JordanAceto/josh_Ox_ribbon_synth/circuit_boards/ribbon_board/protoboard_buffer/README.md

# Protoboard Softpot Ribbon Buffer

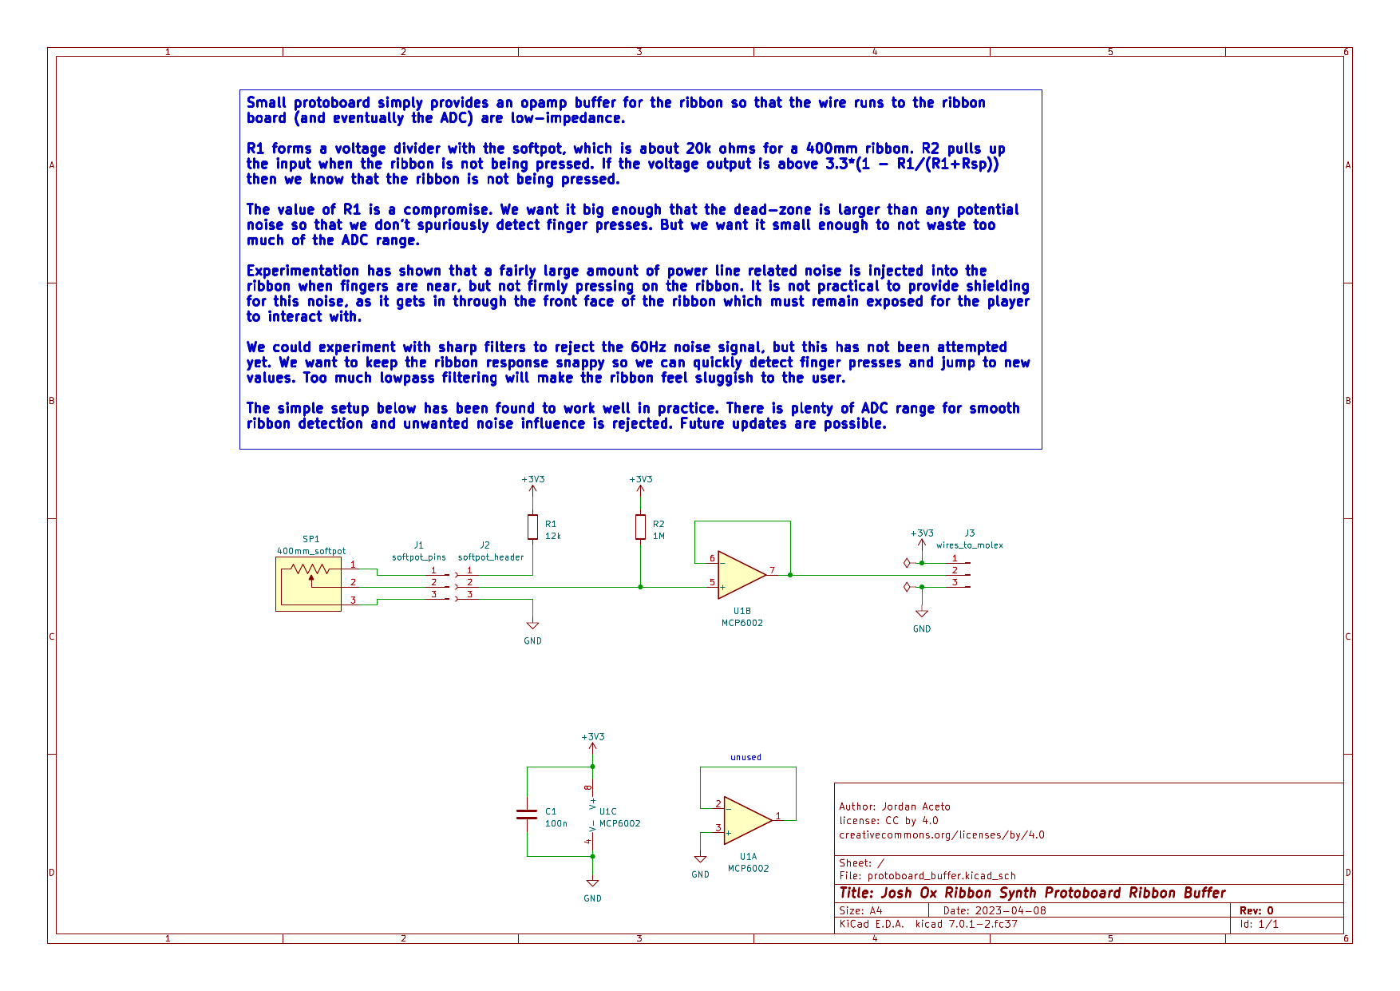
[picture p3: circuit_boards/ribbon_board/protoboard_buffer/images/schem.png]
schematic


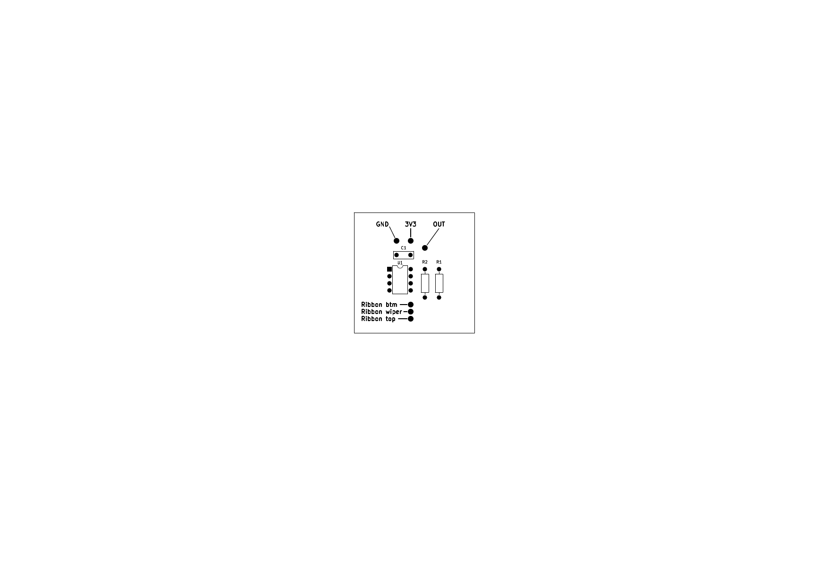
[picture p4: circuit_boards/ribbon_board/protoboard_buffer/images/layout.png]
layout
