JordanAceto/josh_Ox_ribbon_synth/circuit_boards/mains_transformer/mains_transformer.png

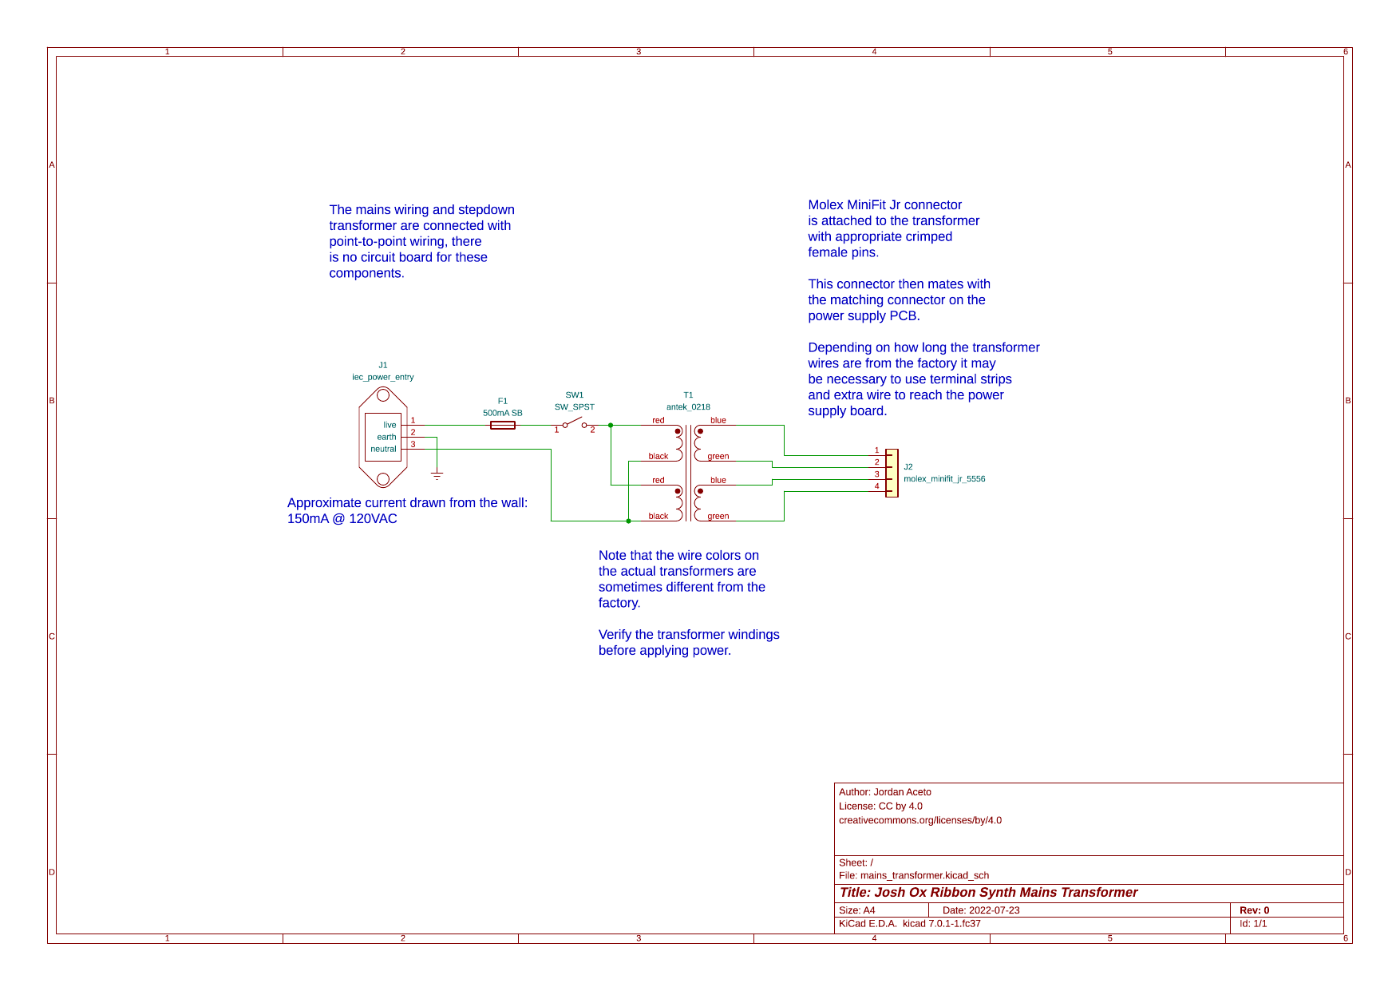
circuit_boards/mains_transformer/mains_transformer.png
