JordanAceto/josh_Ox_ribbon_synth/images/front_angle_2.JPG

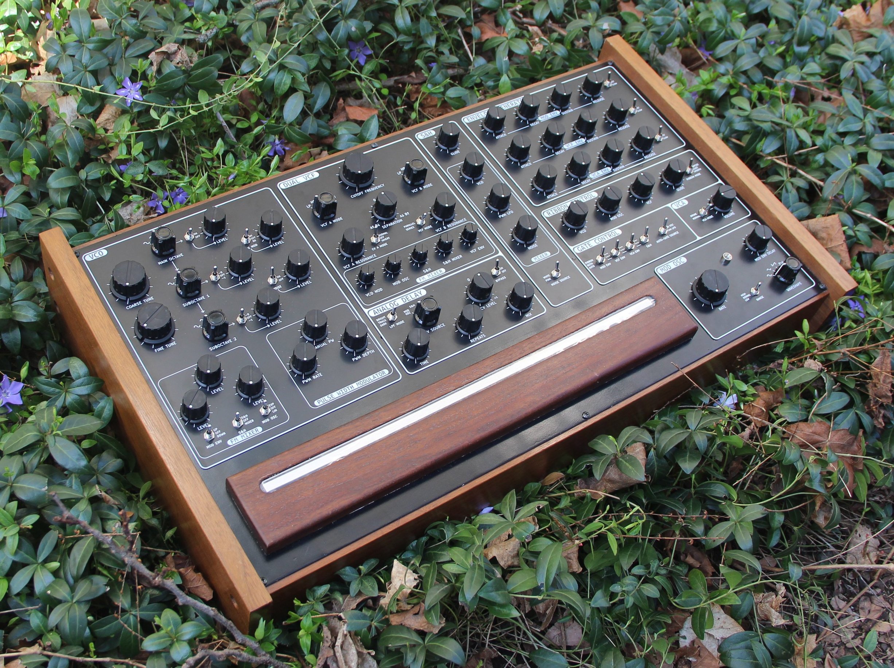
images/front_angle_2.JPG
