JordanAceto/josh_Ox_ribbon_synth/images/front_straight.JPG

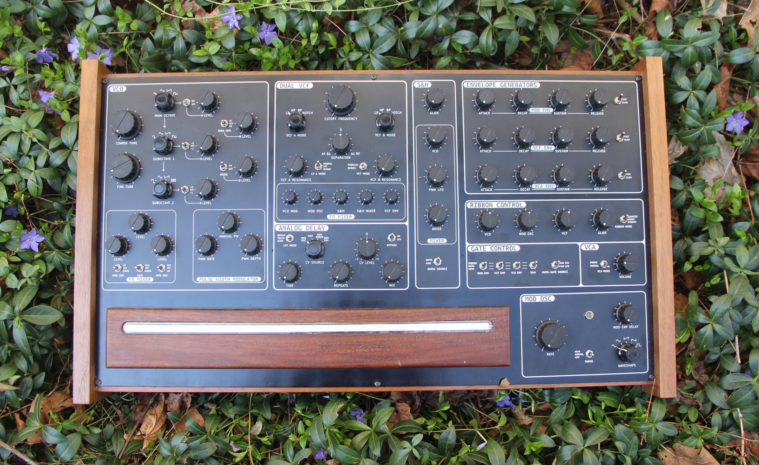
images/front_straight.JPG
