JordanAceto/josh_Ox_ribbon_synth/images/guts_angle.JPG

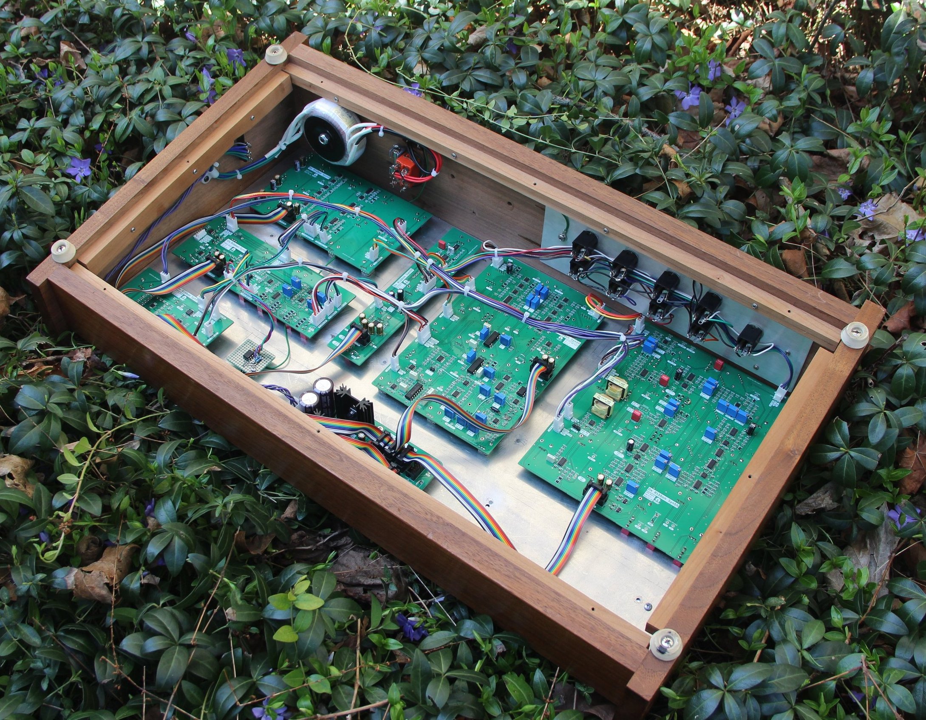
images/guts_angle.JPG
