JordanAceto/josh_Ox_ribbon_synth/images/guts_straight.JPG

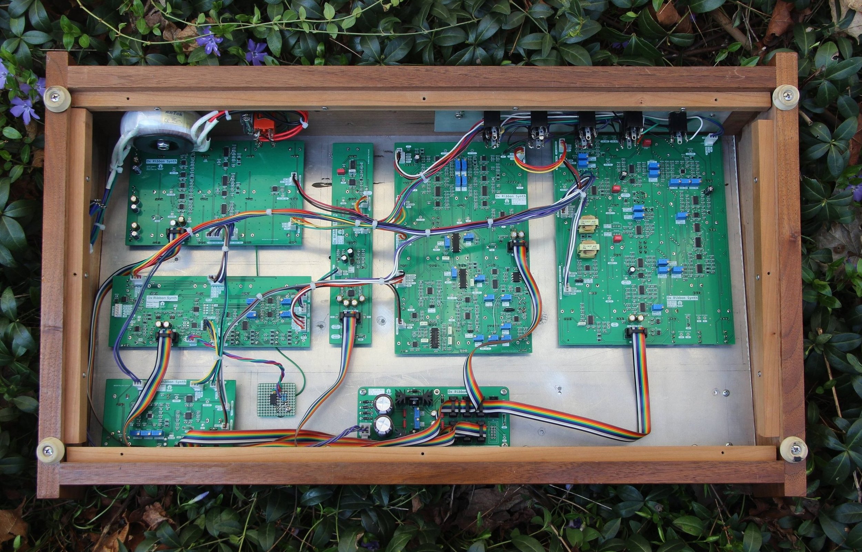
images/guts_straight.JPG
