JordanAceto/josh_Ox_ribbon_synth/images/ox_panel.png

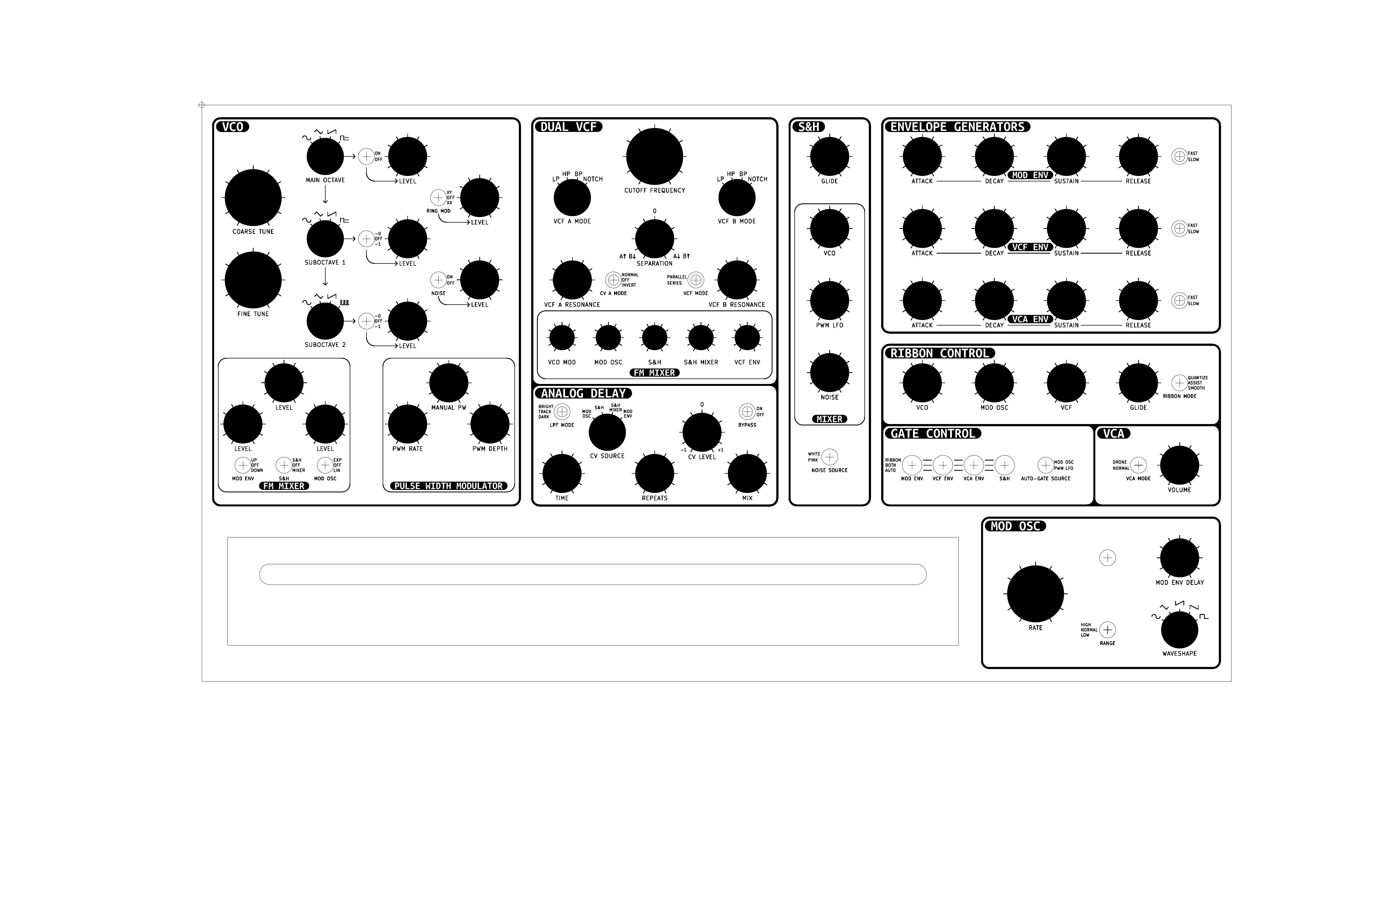
images/ox_panel.png
