JordanAceto/josh_Ox_ribbon_synth/panel/ribbon_pcb_panel/docs/2D/ribbon_pcb_panel_B.Cu.pdf

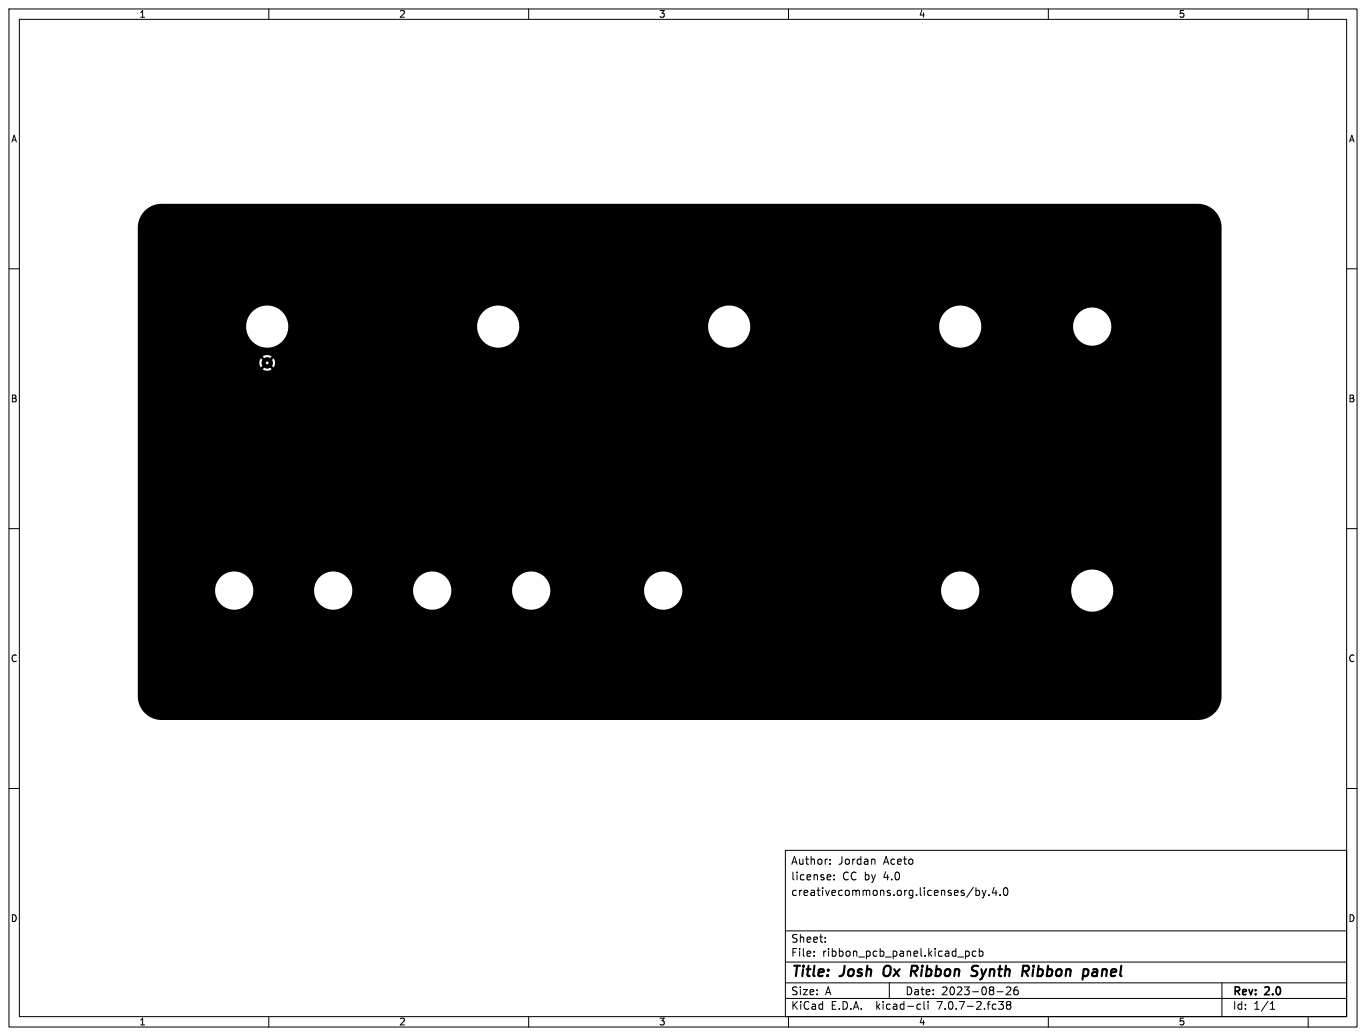
[picture p59: page 1]

license: CC by 4.0 Author: Jordan Aceto

Id: 1/1 Title: Josh Ox Ribbon Synth Ribbon panel File: ribbon_pcb_panel.kicad_pcb Sheet: creativecommons.org.licenses/by.4.0

E.D.A. | kicad-cli | 7.0.7-2.fc38 Size: A | Rev: 2.0 | D Date: 2023-08-26 KiCad
