JordanAceto/josh_Ox_ribbon_synth/circuit_boards/ADSR_board/docs/2D/ADSR_board_B.Cu.pdf

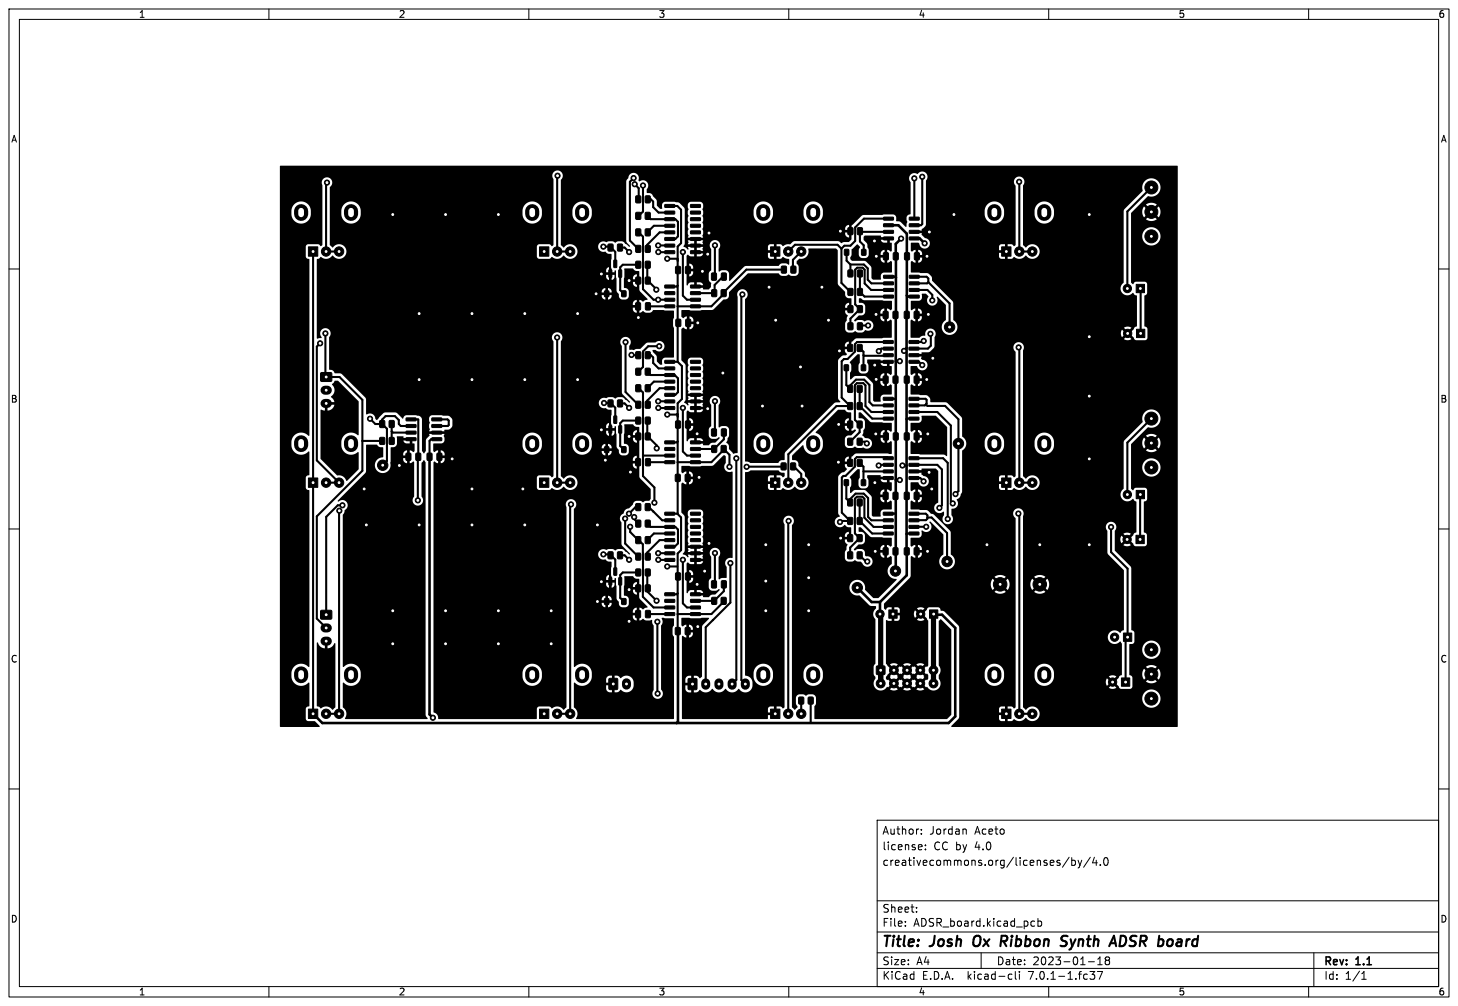
[picture p60: page 1]

File: ADSR_board.kicad_pcb Sheet: creativecommons.org/licenses/by/4.0

Id: 1/1 Title: Josh Ox Ribbon Synth ADSR board
