JordanAceto/josh_Ox_ribbon_synth/circuit_boards/main_VCO_board/docs/2D/main_VCO_board_B.Cu.pdf

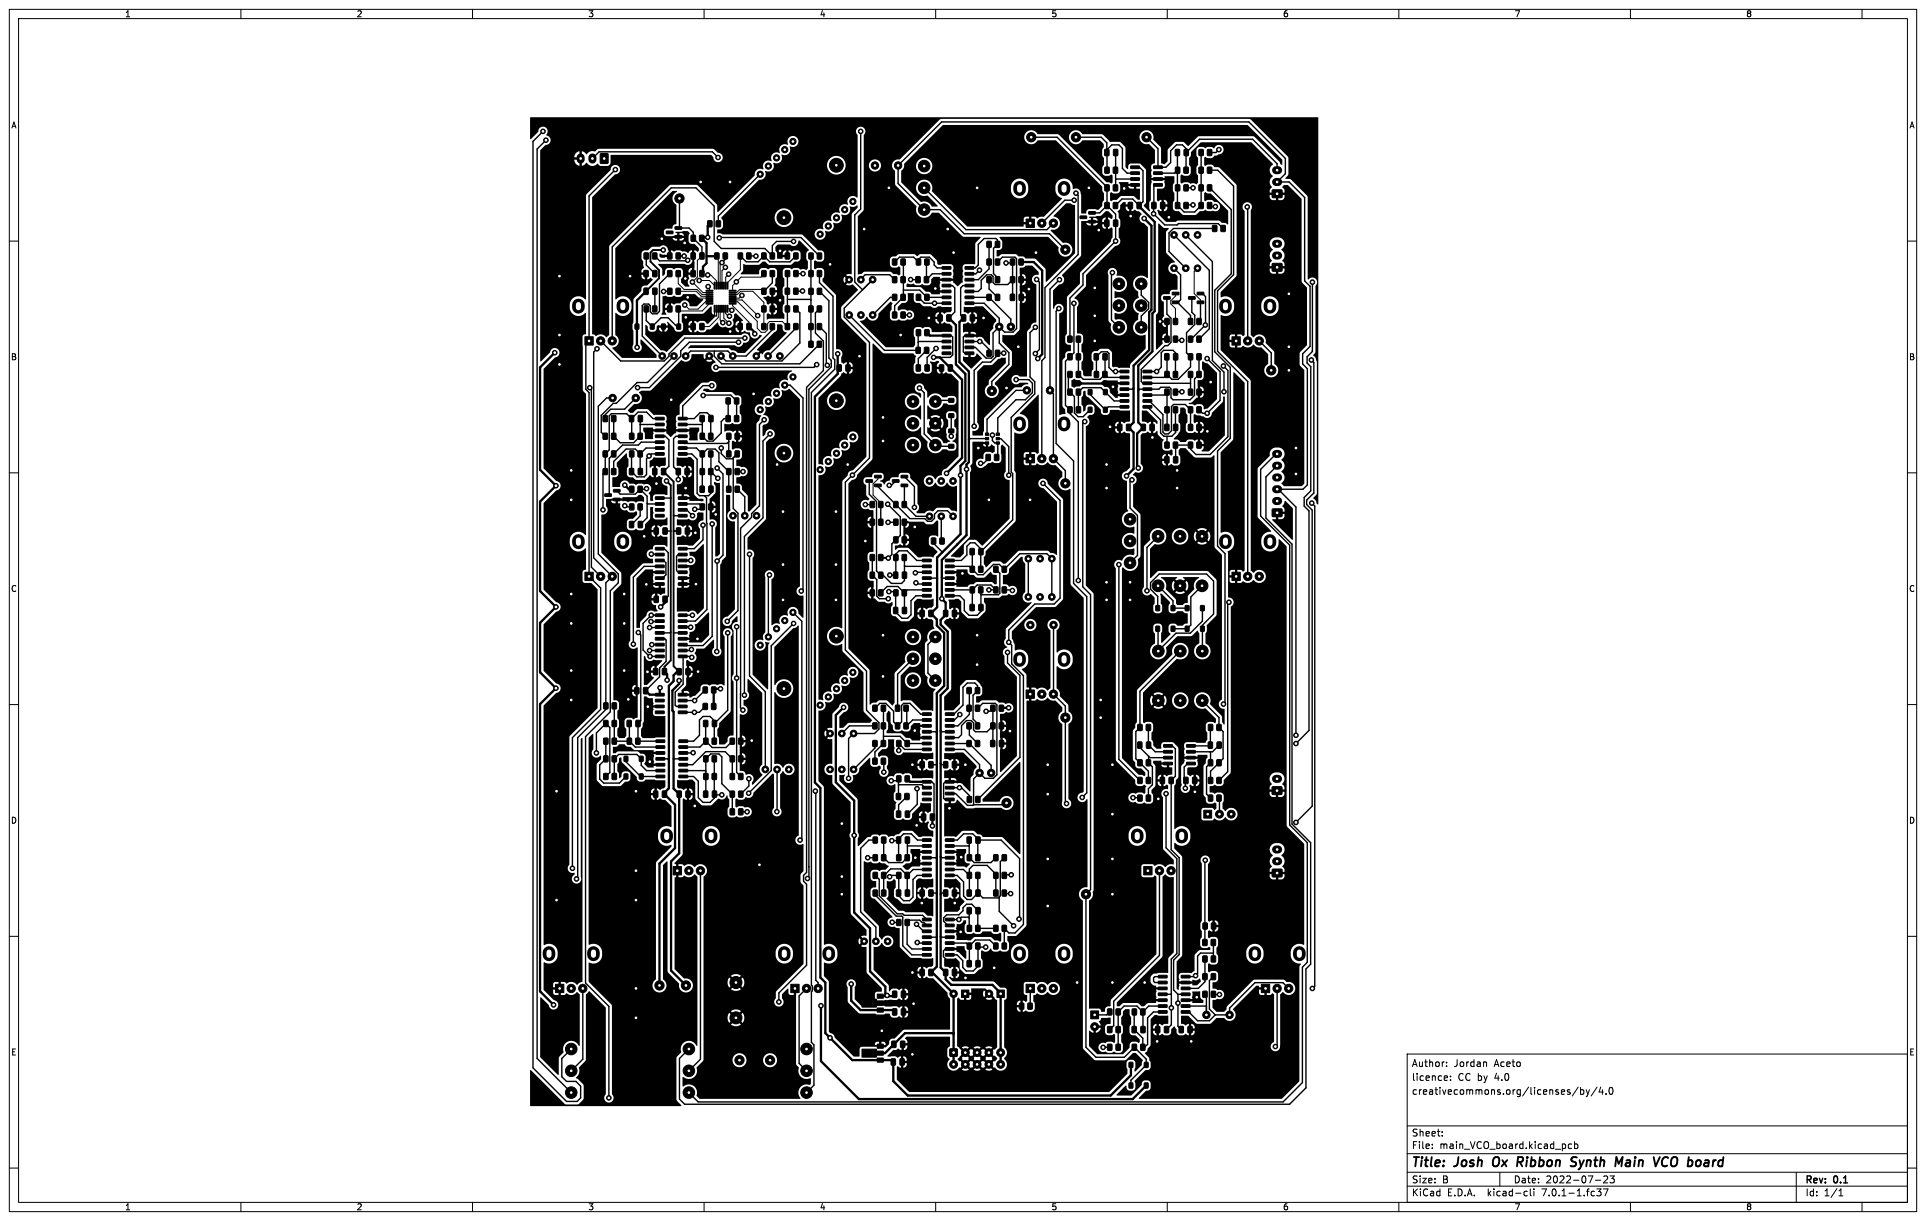
[picture p61: page 1]

File: main_VCO_board.kicad_pcb Sheet: creativecommons.org/licenses/by/4.0

Id: 1/1 Title: Josh Ox Ribbon Synth Main VCO board
