JordanAceto/josh_Ox_ribbon_synth/circuit_boards/power_supply_board/docs/2D/power_supply_F.Cu.pdf

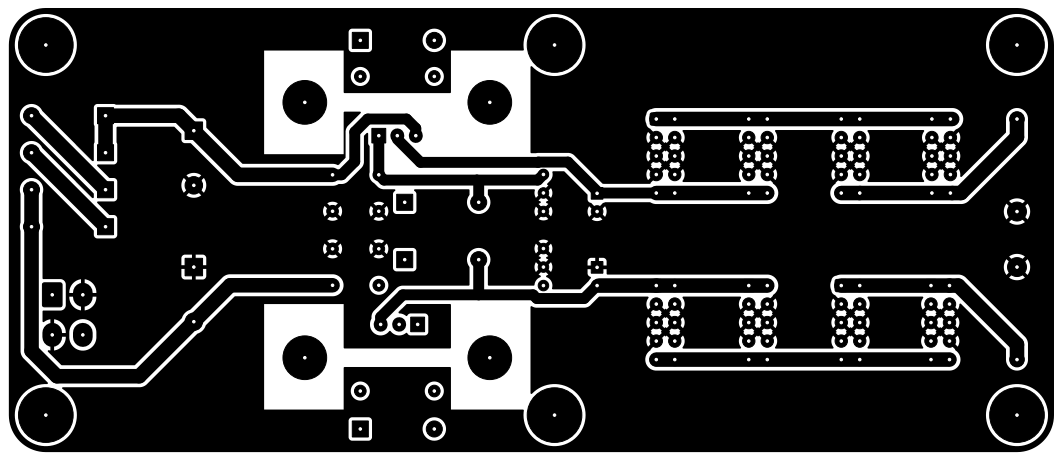
[picture p66: page 1]

Id: 1/1 Title: Josh Ox Ribbon Synth power supply board
