JordanAceto/josh_Ox_ribbon_synth/circuit_boards/power_supply_board/docs/2D/power_supply_F.Paste.pdf

Id: 1/1 Title: Josh Ox Ribbon Synth power supply board
