JordanAceto/josh_Ox_ribbon_synth/circuit_boards/VCF_VCA_BBD_board/docs/2D/VCF_VCA_BBD_board_B.Cu.pdf

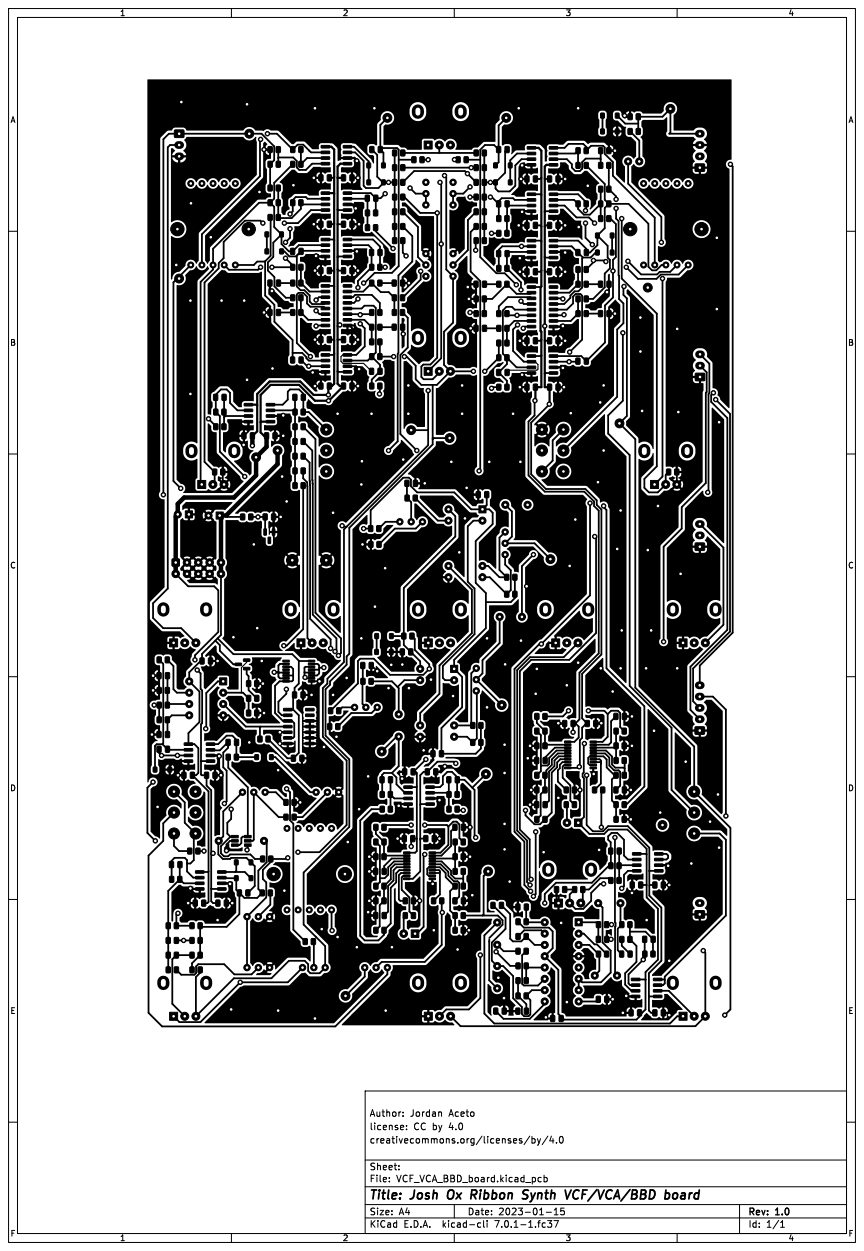
[picture p68: page 1]

File: VCF_VCA_BBD_board.kicad_pcb Sheet: creativecommons.org/licenses/by/4.0

Id: 1/1 Title: Josh Ox Ribbon Synth VCF/VCA/BBD board
