JordanAceto/josh_Ox_ribbon_synth/summer_2022_refurb/VCF_VCA_board/VCF_VCA_board.kicad_pcb

## KiCad design summer_2022_refurb/VCF_VCA_board/VCF_VCA_board.kicad_pcb (2022-06-16)

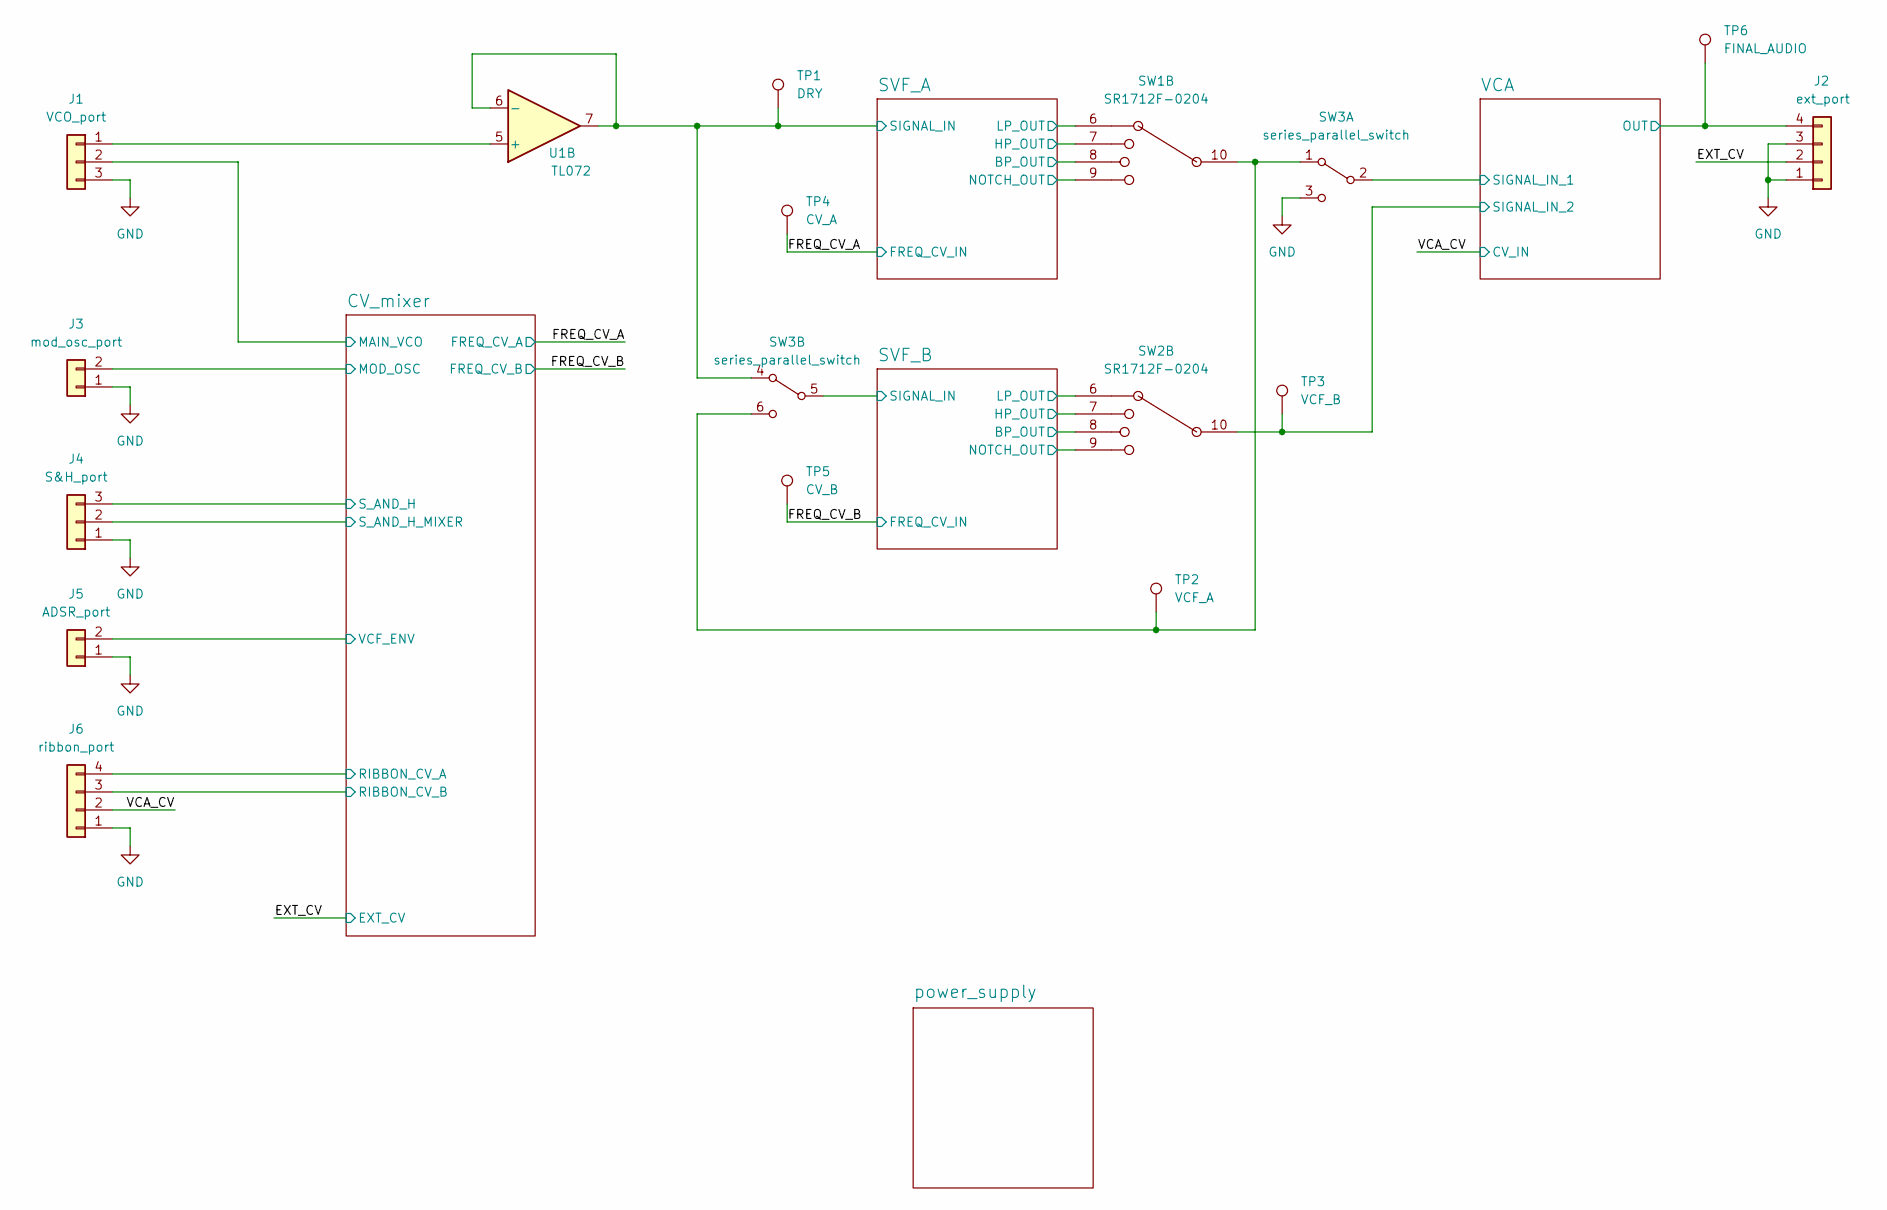
[picture p92: schematic VCF_VCA_board.kicad_sch, Josh Ox Ribbon Synth VCF/VCA board]

Parts:
J1: VCO_port; Molex_KK-254_AE-6410-03A_1x03_P2.54mm_Vertical
J2: ext_port; Molex_KK-254_AE-6410-04A_1x04_P2.54mm_Vertical
J3: mod_osc_port; Molex_KK-254_AE-6410-02A_1x02_P2.54mm_Vertical
J4: S&H_port; Molex_KK-254_AE-6410-03A_1x03_P2.54mm_Vertical
J5: ADSR_port; Molex_KK-254_AE-6410-02A_1x02_P2.54mm_Vertical
J6: ribbon_port; Molex_KK-254_AE-6410-04A_1x04_P2.54mm_Vertical
SW1, SW2: SR1712F-0204; SR1712F_rotary_switch
SW3: series_parallel_switch; DPDT_mini_toggle
TP1: DRY; TestPoint_Keystone_5000-5004_Miniature
TP2: VCF_A; TestPoint_Keystone_5000-5004_Miniature
TP3: VCF_B; TestPoint_Keystone_5000-5004_Miniature
TP4: CV_A; TestPoint_Keystone_5000-5004_Miniature
TP5: CV_B; TestPoint_Keystone_5000-5004_Miniature
TP6: FINAL_AUDIO; TestPoint_Keystone_5000-5004_Miniature
U1: TL072; SO-8_5.3x6.2mm_P1.27mm

Connections:
/CV_mixer/MAIN_VCO: J1.2; also elsewhere on the board
/CV_mixer/MOD_OSC: J3.2; also elsewhere on the board
/CV_mixer/RIBBON_CV_A: J6.4; also elsewhere on the board
/CV_mixer/RIBBON_CV_B: J6.3; also elsewhere on the board
/CV_mixer/S_AND_H: J4.3; also elsewhere on the board
/CV_mixer/S_AND_H_MIXER: J4.2; also elsewhere on the board
/CV_mixer/VCF_ENV: J5.2; also elsewhere on the board
/EXT_CV: J2.2; also elsewhere on the board
/FREQ_CV_A: TP4.1; also elsewhere on the board
/FREQ_CV_B: TP5.1; also elsewhere on the board
/SVF_A/BP_OUT: SW1.8; also elsewhere on the board
/SVF_A/HP_OUT: SW1.7; also elsewhere on the board
/SVF_A/LP_OUT: SW1.6; also elsewhere on the board
/SVF_A/NOTCH_OUT: SW1.9; also elsewhere on the board
/SVF_A/SIGNAL_IN: SW3.4 (A), TP1.1, U1.6 (-), U1.7; also elsewhere on the board
/SVF_B/BP_OUT: SW2.8; also elsewhere on the board
/SVF_B/HP_OUT: SW2.7; also elsewhere on the board
/SVF_B/LP_OUT: SW2.6; also elsewhere on the board
/SVF_B/NOTCH_OUT: SW2.9; also elsewhere on the board
/SVF_B/SIGNAL_IN: SW3.5 (B); also elsewhere on the board
/VCA/OUT: J2.4, TP6.1; also elsewhere on the board
/VCA/SIGNAL_IN_1: SW3.2 (B); also elsewhere on the board
/VCA/SIGNAL_IN_2: SW2.10, TP3.1; also elsewhere on the board
/VCA_CV: J6.2; also elsewhere on the board
unnamed: J1.1, U1.5 (+)
unnamed: SW1.10, SW3.1 (A), SW3.6 (C), TP2.1

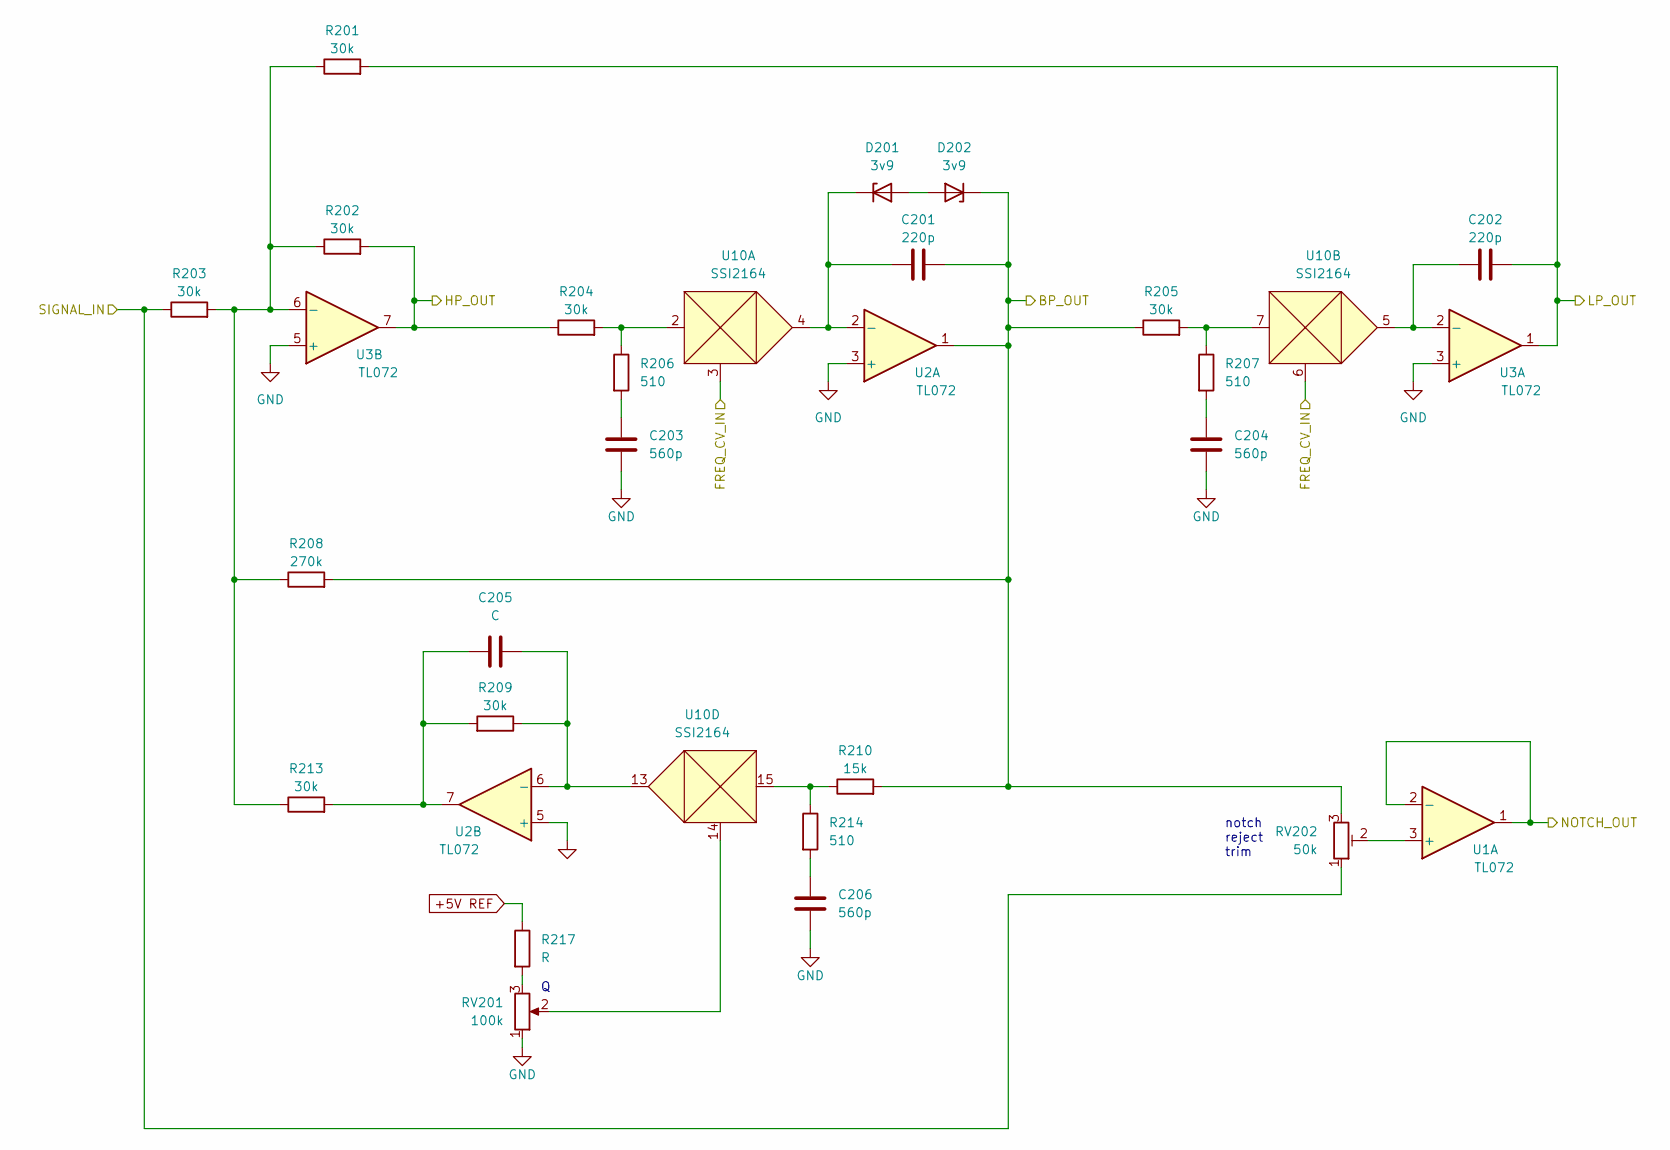
[picture p93: schematic SVF.kicad_sch, Josh Ox Ribbon Synth VCF/VCA board]

Parts:
C201, C202: 220p; C_Rect_L7.2mm_W4.5mm_P5.00mm_FKS2_FKP2_MKS2_MKP2
C203, C204, C206: 560p; C_0805_2012Metric
C205: C; C_0805_2012Metric
D201, D202: 3v9; D_SOD-123
R201, R202, R203, R204, R205, R209, R213: 30k; R_0805_2012Metric
R206, R207, R214: 510; R_0805_2012Metric
R208: 270k; R_0805_2012Metric
R210: 15k; R_0805_2012Metric
R217: R; R_0805_2012Metric
RV201: 100k; Potentiometer_Alpha_RD901F-40-00D_Single_Vertical
RV202: 50k; Potentiometer_Bourns_3296W_Vertical
U1, U2, U3: TL072; SO-8_5.3x6.2mm_P1.27mm
U10: SSI2164; SOIC-16_3.9x9.9mm_P1.27mm

Connections:
+5V REF: R217.1; also elsewhere on the board
/FREQ_CV_A: U10.3, U10.6; also elsewhere on the board
/SVF_A/BP_OUT: C201.2, D202.1 (K), R205.1, R208.2, R210.2, RV202.3, U2.1; also elsewhere on the board
/SVF_A/HP_OUT: R202.2, R204.1, U3.7; also elsewhere on the board
/SVF_A/LP_OUT: C202.2, R201.2, U3.1; also elsewhere on the board
/SVF_A/NOTCH_OUT: U1.1, U1.2 (-); also elsewhere on the board
/SVF_A/SIGNAL_IN: R203.1, RV202.1; also elsewhere on the board
unnamed: C201.1, D201.1 (K), U2.2 (-), U10.4
unnamed: C202.1, U3.2 (-), U10.5
unnamed: C203.1, R206.2
unnamed: C204.1, R207.2
unnamed: C205.1, R209.2, R213.2, U2.7
unnamed: C205.2, R209.1, U2.6 (-), U10.13
unnamed: C206.1, R214.2
unnamed: D201.2 (A), D202.2 (A)
unnamed: R201.1, R202.1, R203.2, R208.1, R213.1, U3.6 (-)
unnamed: R204.2, R206.1, U10.2
unnamed: R205.2, R207.1, U10.7
unnamed: R210.1, R214.1, U10.15
unnamed: R217.2, RV201.3
unnamed: RV201.2, U10.14
unnamed: RV202.2, U1.3 (+)

Notes on the sheet:
notch reject trim

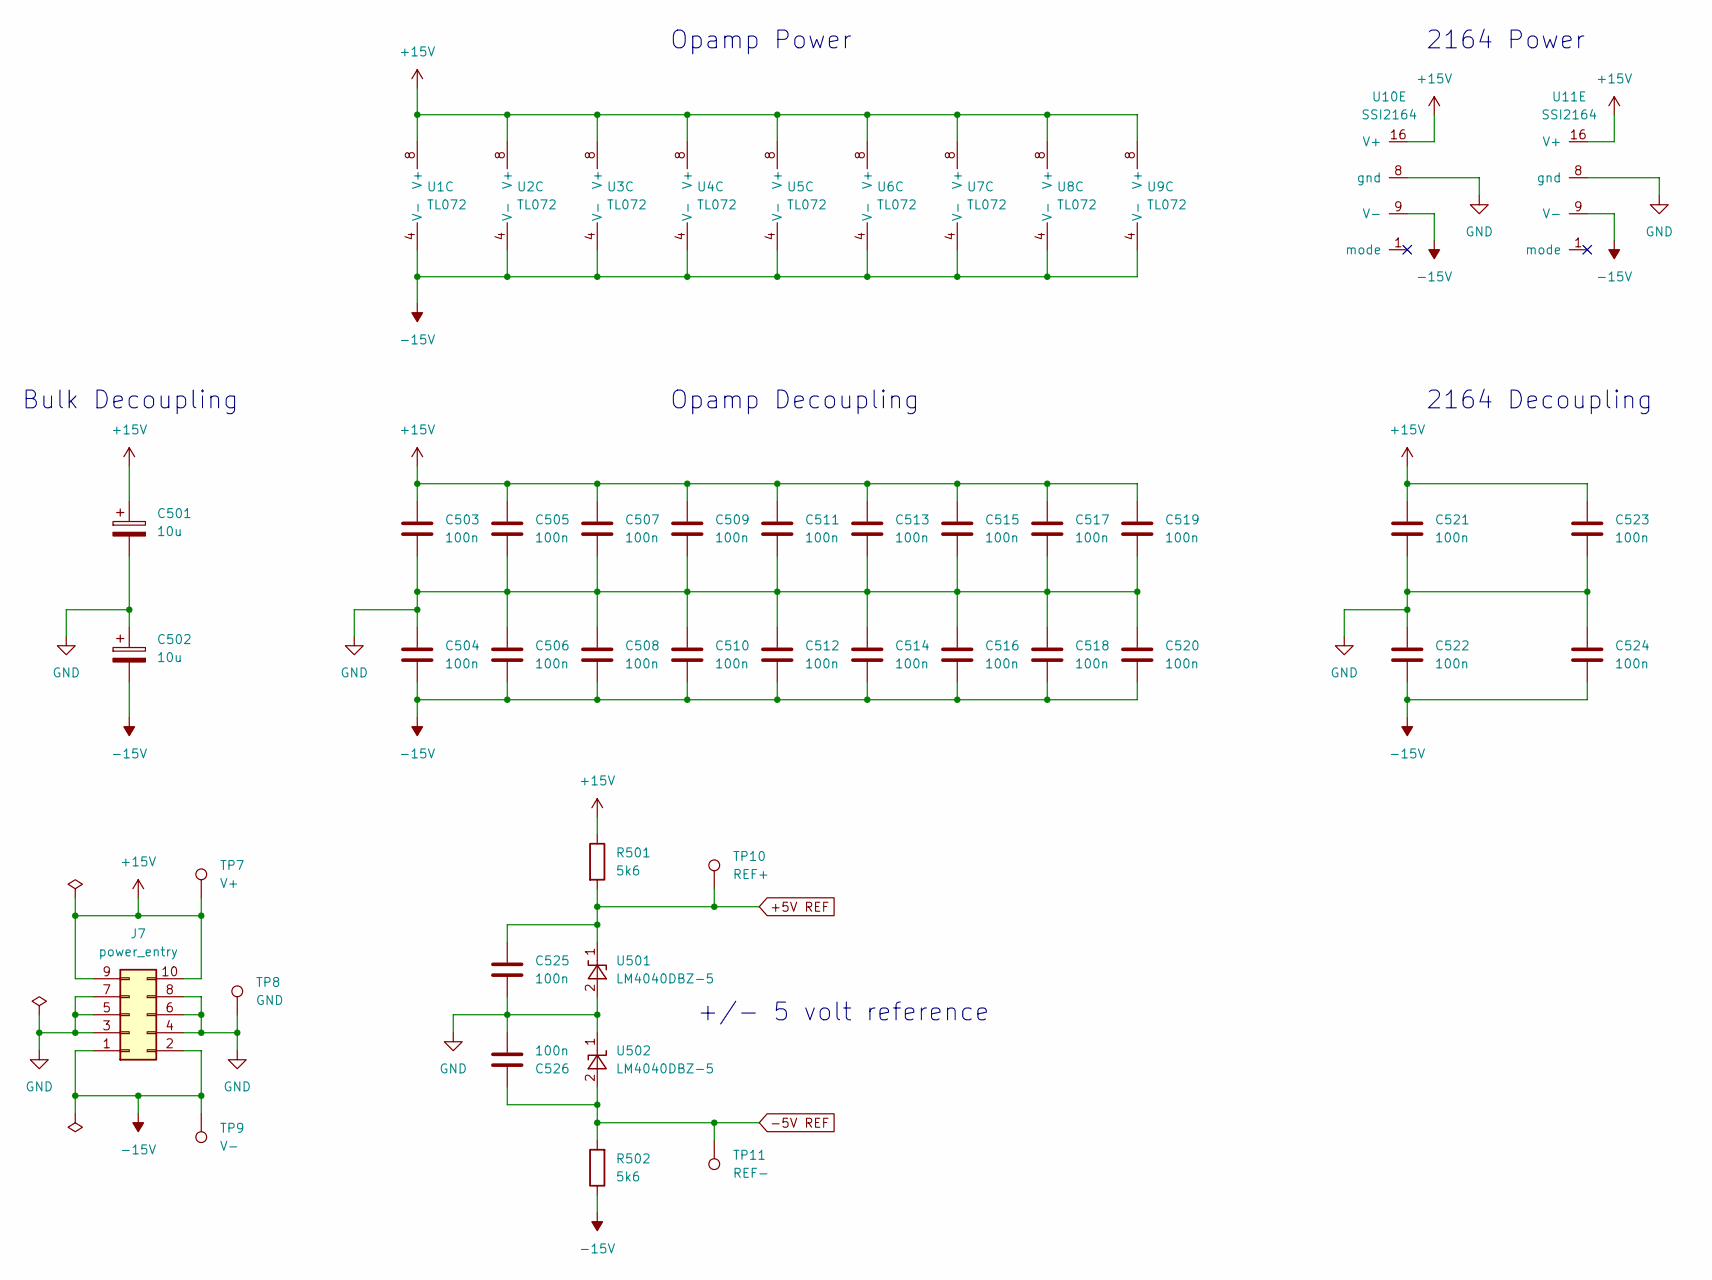
[picture p94: schematic power_supply.kicad_sch, Josh Ox Ribbon Synth VCF/VCA board]

Parts:
C501, C502: 10u; CP_Radial_D6.3mm_P2.50mm
C503, C504, C505, C506, C507, C508, C509, C510, C511, C512, C513, C514, C515, C516, C517, C518, C519, C520, C521, C522, C523, C524, C525, C526: 100n; C_0805_2012Metric
J7: power_entry; IDC-Header_2x05_P2.54mm_Vertical
R501, R502: 5k6; R_0805_2012Metric
TP7: V+; TestPoint_Keystone_5000-5004_Miniature
TP8: GND; TestPoint_Bridge_Pitch7.62mm_Drill1.3mm
TP9: V-; TestPoint_Keystone_5000-5004_Miniature
TP10: REF+; TestPoint_Keystone_5000-5004_Miniature
TP11: REF-; TestPoint_Keystone_5000-5004_Miniature
U1, U2, U3, U4, U5, U6, U7, U8, U9: TL072; SO-8_5.3x6.2mm_P1.27mm
U10, U11: SSI2164; SOIC-16_3.9x9.9mm_P1.27mm
U501, U502: LM4040DBZ-5; SOT-23

Connections:
+5V REF: C525.1, R501.2, TP10.1, U501.1 (K); also elsewhere on the board
+15V: C501.1, C503.1, C505.1, C507.1, C509.1, C511.1, C513.1, C515.1, C517.1, C519.1, C521.1, C523.1, J7.9, J7.10, R501.1, TP7.1, U1.8 (V+), U2.8 (V+), U3.8 (V+), U4.8 (V+), U5.8 (V+), U6.8 (V+), U7.8 (V+), U8.8 (V+), U9.8 (V+), U10.16 (V+), U11.16 (V+)
-5V REF: C526.1, R502.2, TP11.1, U502.2 (A); also elsewhere on the board
-15V: C502.2, C504.2, C506.2, C508.2, C510.2, C512.2, C514.2, C516.2, C518.2, C520.2, C522.2, C524.2, J7.1, J7.2, R502.1, TP9.1, U1.4 (V-), U2.4 (V-), U3.4 (V-), U4.4 (V-), U5.4 (V-), U6.4 (V-), U7.4 (V-), U8.4 (V-), U9.4 (V-), U10.9 (V-), U11.9 (V-)
/FREQ_CV_B: U11.3, U11.6; also elsewhere on the board
/SVF_B/BP_OUT: U4.1; also elsewhere on the board
/SVF_B/HP_OUT: U5.7; also elsewhere on the board
/SVF_B/LP_OUT: U5.1; also elsewhere on the board
/SVF_B/NOTCH_OUT: U6.6 (-), U6.7; also elsewhere on the board
unnamed 35: U4.2 (-), U11.4; also elsewhere on the board
unnamed 36: U5.2 (-), U11.5; also elsewhere on the board
unnamed 39: U4.7; also elsewhere on the board
unnamed 40: U4.6 (-), U11.13; also elsewhere on the board
unnamed 68: U5.6 (-); also elsewhere on the board
unnamed 69: U11.2; also elsewhere on the board
unnamed 70: U11.7; also elsewhere on the board
unnamed 71: U11.15; also elsewhere on the board
unnamed 90: U11.14; also elsewhere on the board
unnamed 91: U6.5 (+); also elsewhere on the board

Notes on the sheet:
Opamp Power
2164 Decoupling
+/- 5 volt reference
2164 Power
Bulk Decoupling
Opamp Decoupling

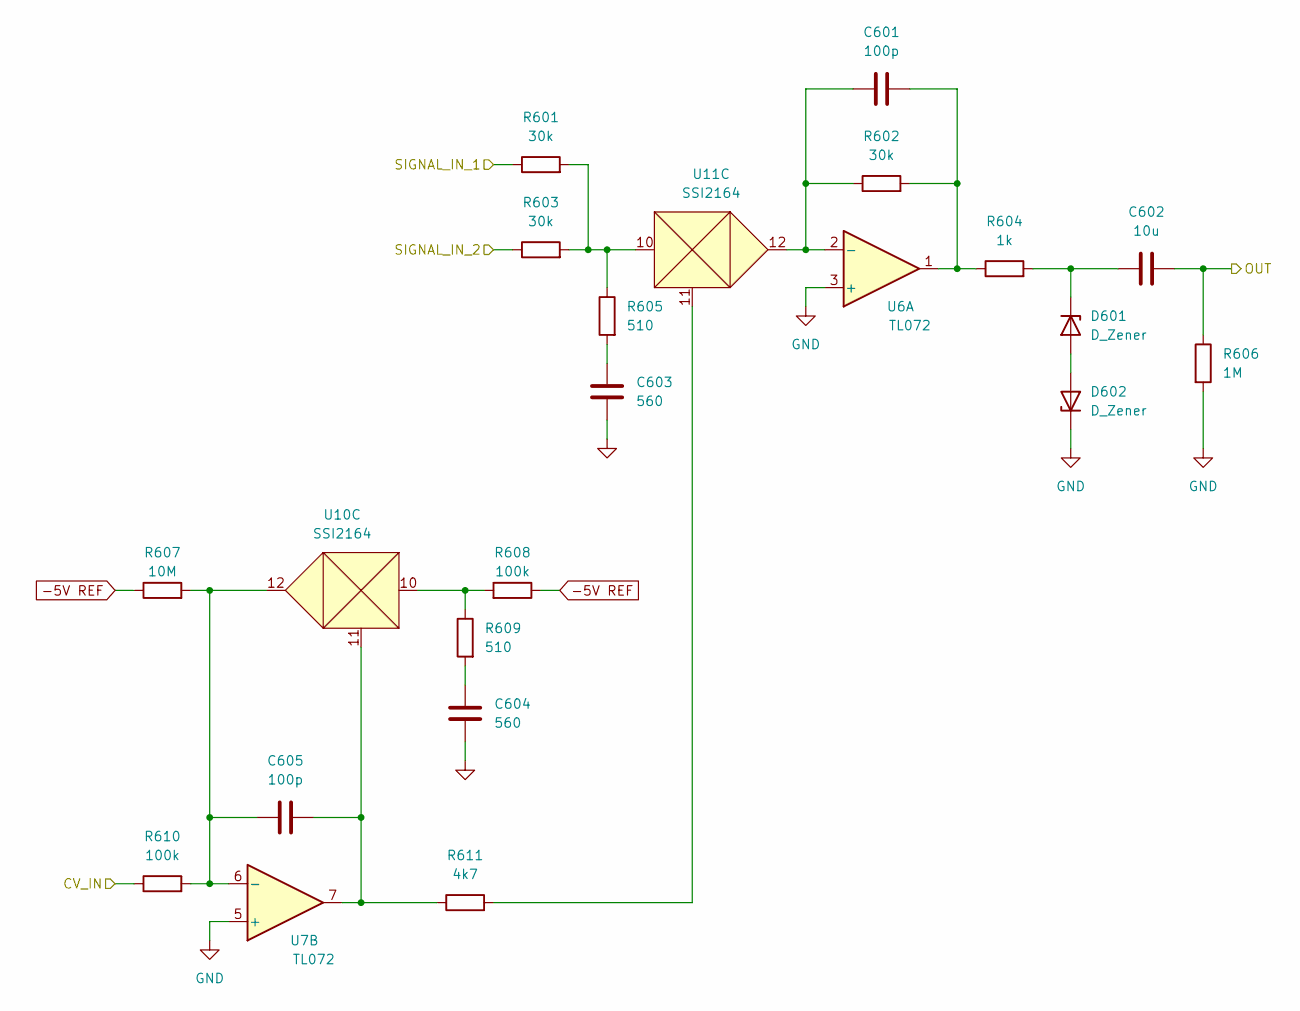
[picture p95: schematic VCA.kicad_sch, Josh Ox Ribbon Synth VCF/VCA board]

Parts:
C601, C605: 100p; C_0805_2012Metric
C602: 10u; C_Radial_D6.3mm_H5.0mm_P2.50mm
C603, C604: 560; C_0805_2012Metric
D601, D602: D_Zener; D_SOD-123
R601, R602, R603: 30k; R_0805_2012Metric
R604: 1k; R_0805_2012Metric
R605, R609: 510; R_0805_2012Metric
R606: 1M; R_0805_2012Metric
R607: 10M; R_0805_2012Metric
R608, R610: 100k; R_0805_2012Metric
R611: 4k7; R_0805_2012Metric
U6, U7: TL072; SO-8_5.3x6.2mm_P1.27mm
U10, U11: SSI2164; SOIC-16_3.9x9.9mm_P1.27mm

Connections:
-5V REF: R607.1, R608.1; also elsewhere on the board
/FREQ_CV_B: U11.3, U11.6; also elsewhere on the board
/SVF_B/NOTCH_OUT: U6.6 (-), U6.7; also elsewhere on the board
/VCA/OUT: C602.2, R606.1; also elsewhere on the board
/VCA/SIGNAL_IN_1: R601.1; also elsewhere on the board
/VCA/SIGNAL_IN_2: R603.1; also elsewhere on the board
/VCA_CV: R610.1; also elsewhere on the board
unnamed 35: U11.4; also elsewhere on the board
unnamed 36: U11.5; also elsewhere on the board
unnamed 40: U11.13; also elsewhere on the board
unnamed: C601.1, R602.1, U6.2 (-), U11.12
unnamed: C601.2, R602.2, R604.1, U6.1
unnamed: C602.1, D601.1 (K), R604.2
unnamed: C603.1, R605.2
unnamed: C604.1, R609.2
unnamed: C605.1, R607.2, R610.2, U7.6 (-), U10.12
unnamed: C605.2, R611.1, U7.7, U10.11
unnamed: D601.2 (A), D602.2 (A)
unnamed 69: U11.2; also elsewhere on the board
unnamed 70: U11.7; also elsewhere on the board
unnamed 71: U11.15; also elsewhere on the board
unnamed: R601.2, R603.2, R605.1, U11.10
unnamed: R608.2, R609.1, U10.10
unnamed: R611.2, U11.11
unnamed 90: U11.14; also elsewhere on the board
unnamed 91: U6.5 (+); also elsewhere on the board

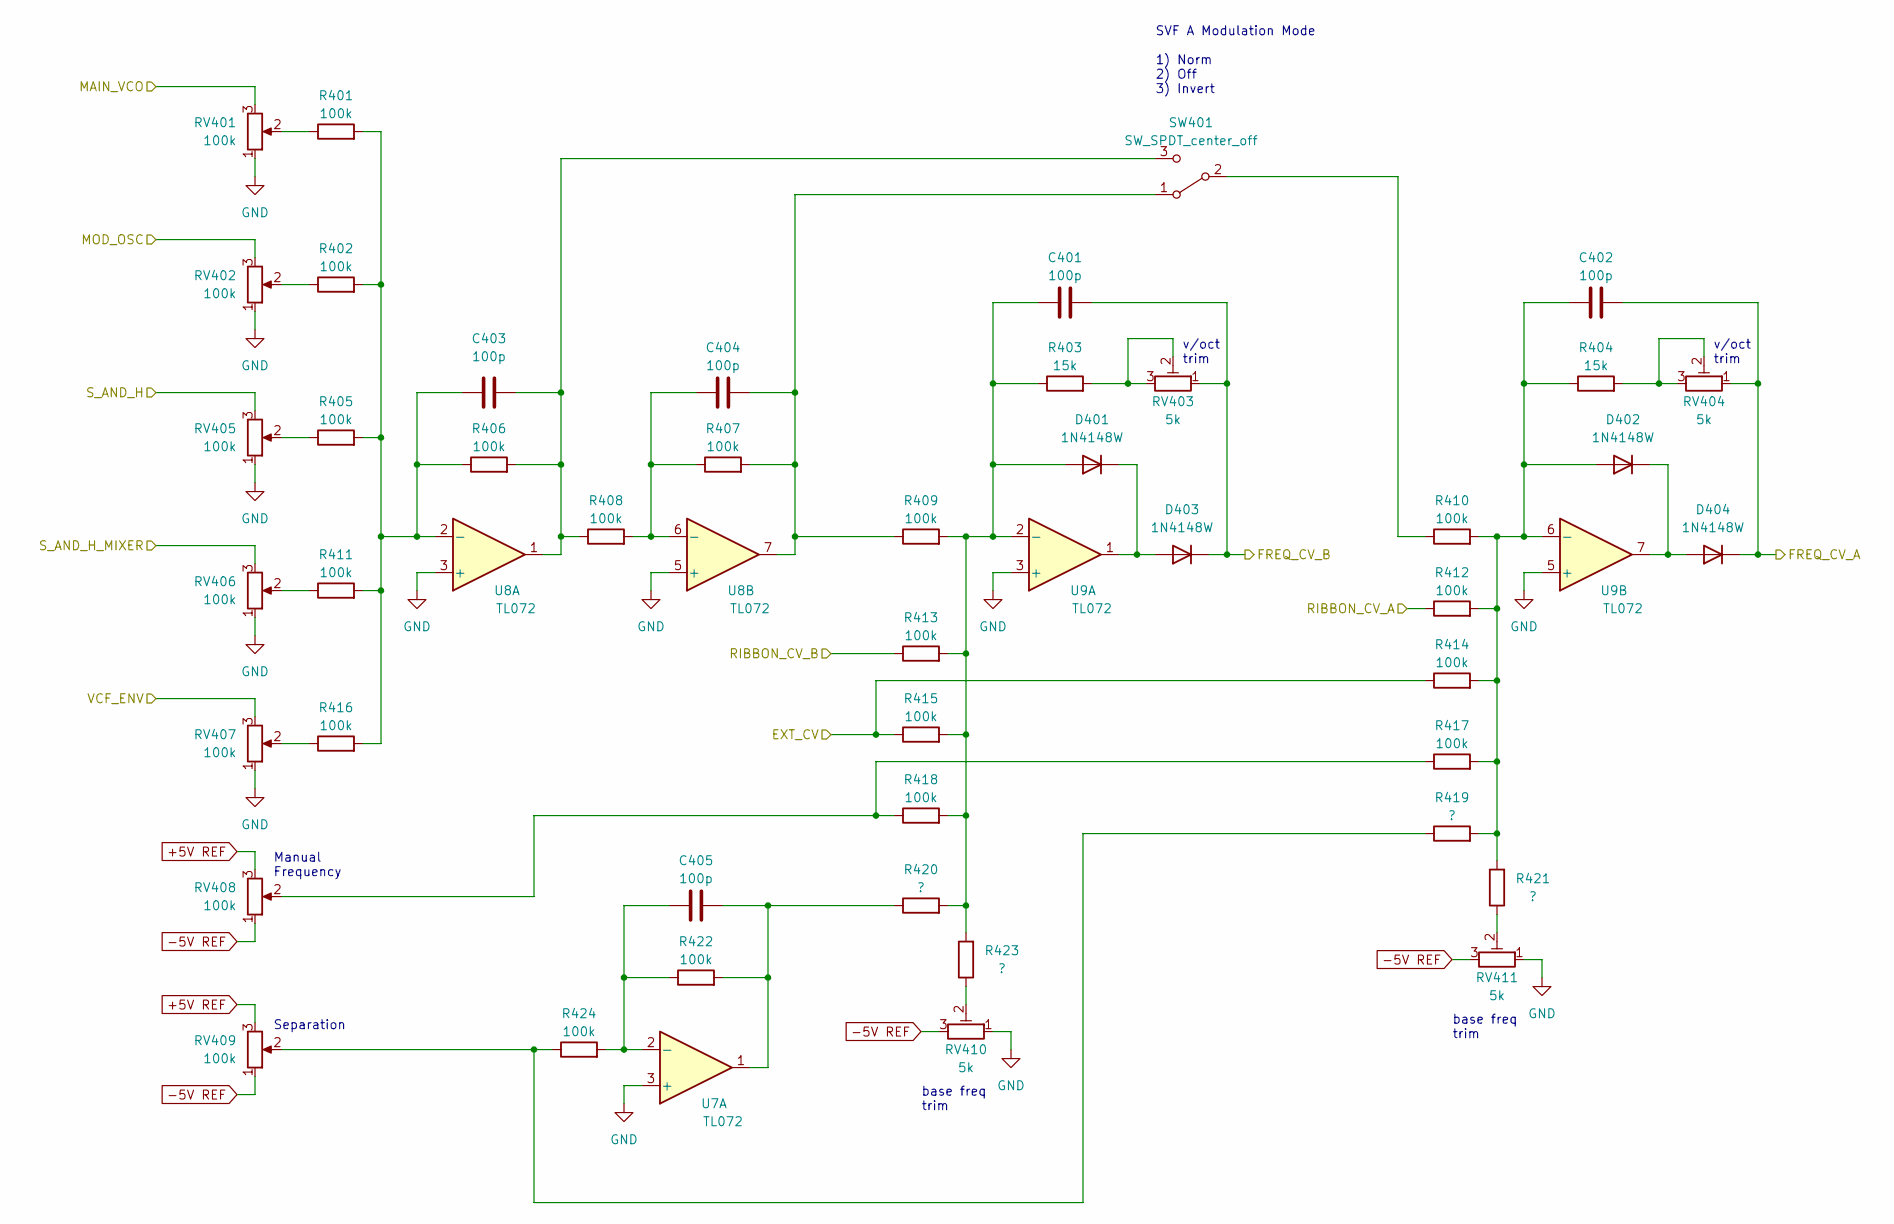
[picture p96: schematic CV_mixer.kicad_sch, Josh Ox Ribbon Synth VCF/VCA board]

Parts:
C401, C402, C403, C404, C405: 100p; C_0805_2012Metric
D401, D402, D403, D404: 1N4148W; D_SOD-123
R401, R402, R405, R406, R407, R408, R409, R410, R411, R412, R413, R414, R415, R416, R417, R418, R422, R424: 100k; R_0805_2012Metric
R403, R404: 15k; R_0805_2012Metric
R419, R420, R421, R423: ?; R_0805_2012Metric
RV401, RV402, RV405, RV406, RV407, RV408, RV409: 100k; Potentiometer_Alpha_RD901F-40-00D_Single_Vertical
RV403, RV404, RV410, RV411: 5k; Potentiometer_Bourns_3296W_Vertical
SW401: SW_SPDT_center_off; SPDT_mini_toggle
U7, U8, U9: TL072; SO-8_5.3x6.2mm_P1.27mm

Connections:
+5V REF: RV408.3, RV409.3; also elsewhere on the board
-5V REF: RV408.1, RV409.1, RV410.3, RV411.3; also elsewhere on the board
/CV_mixer/MAIN_VCO: RV401.3; also elsewhere on the board
/CV_mixer/MOD_OSC: RV402.3; also elsewhere on the board
/CV_mixer/RIBBON_CV_A: R412.1; also elsewhere on the board
/CV_mixer/RIBBON_CV_B: R413.1; also elsewhere on the board
/CV_mixer/S_AND_H: RV405.3; also elsewhere on the board
/CV_mixer/S_AND_H_MIXER: RV406.3; also elsewhere on the board
/CV_mixer/VCF_ENV: RV407.3; also elsewhere on the board
/EXT_CV: R414.1, R415.1; also elsewhere on the board
/FREQ_CV_A: C402.2, D404.1 (K), RV404.1; also elsewhere on the board
/FREQ_CV_B: C401.2, D403.1 (K), RV403.1; also elsewhere on the board
unnamed: C401.1, D401.2 (A), R403.1, R409.2, R413.2, R415.2, R418.2, R420.2, R423.2, U9.2 (-)
unnamed: C402.1, D402.2 (A), R404.1, R410.2, R412.2, R414.2, R417.2, R419.2, R421.2, U9.6 (-)
unnamed: C403.1, R401.2, R402.2, R405.2, R406.1, R411.2, R416.2, U8.2 (-)
unnamed: C403.2, R406.2, R408.1, SW401.3 (C), U8.1
unnamed: C404.1, R407.1, R408.2, U8.6 (-)
unnamed: C404.2, R407.2, R409.1, SW401.1 (A), U8.7
unnamed: C405.1, R422.1, R424.2, U7.2 (-)
unnamed: C405.2, R420.1, R422.2, U7.1
unnamed: D401.1 (K), D403.2 (A), U9.1
unnamed: D402.1 (K), D404.2 (A), U9.7
unnamed: R401.1, RV401.2
unnamed: R402.1, RV402.2
unnamed: R403.2, RV403.2, RV403.3
unnamed: R404.2, RV404.2, RV404.3
unnamed: R405.1, RV405.2
unnamed: R410.1, SW401.2 (B)
unnamed: R411.1, RV406.2
unnamed: R416.1, RV407.2
unnamed: R417.1, R418.1, RV408.2
unnamed: R419.1, R424.1, RV409.2
unnamed: R421.1, RV411.2
unnamed: R423.1, RV410.2

Notes on the sheet:
Manual Frequency
SVF A Modulation Mode 1) Norm 2) Off 3) Invert
Separation
base freq trim
v/oct trim

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
