JordanAceto/josh_Ox_ribbon_synth/summer_2022_refurb/VCF_VCA_board/VCF_VCA_board.kicad_pcb

## KiCad design summer_2022_refurb/VCF_VCA_board/VCF_VCA_board.kicad_pcb (continued)

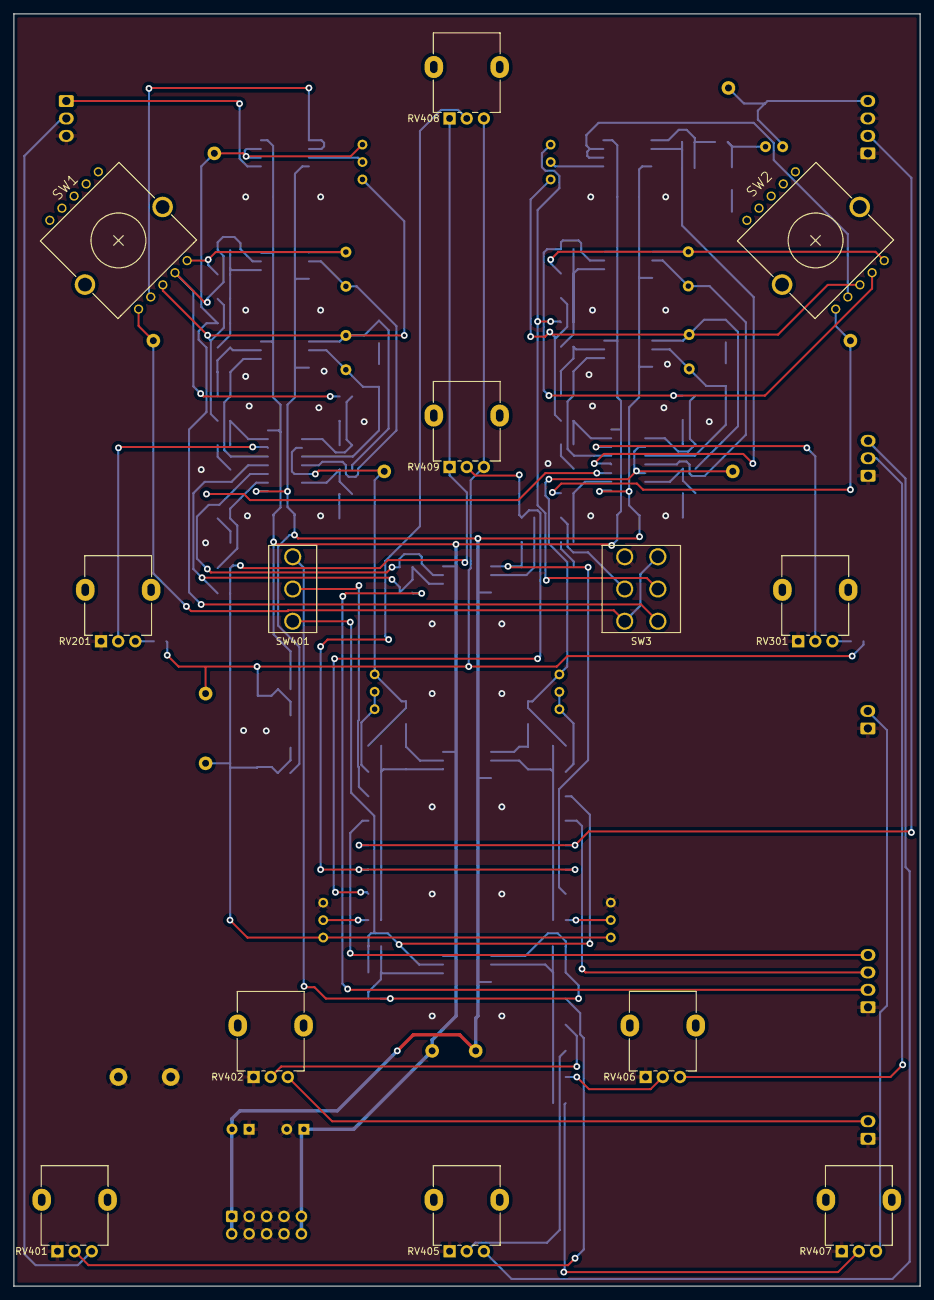
[picture p97: board VCF_VCA_board.kicad_pcb from above]

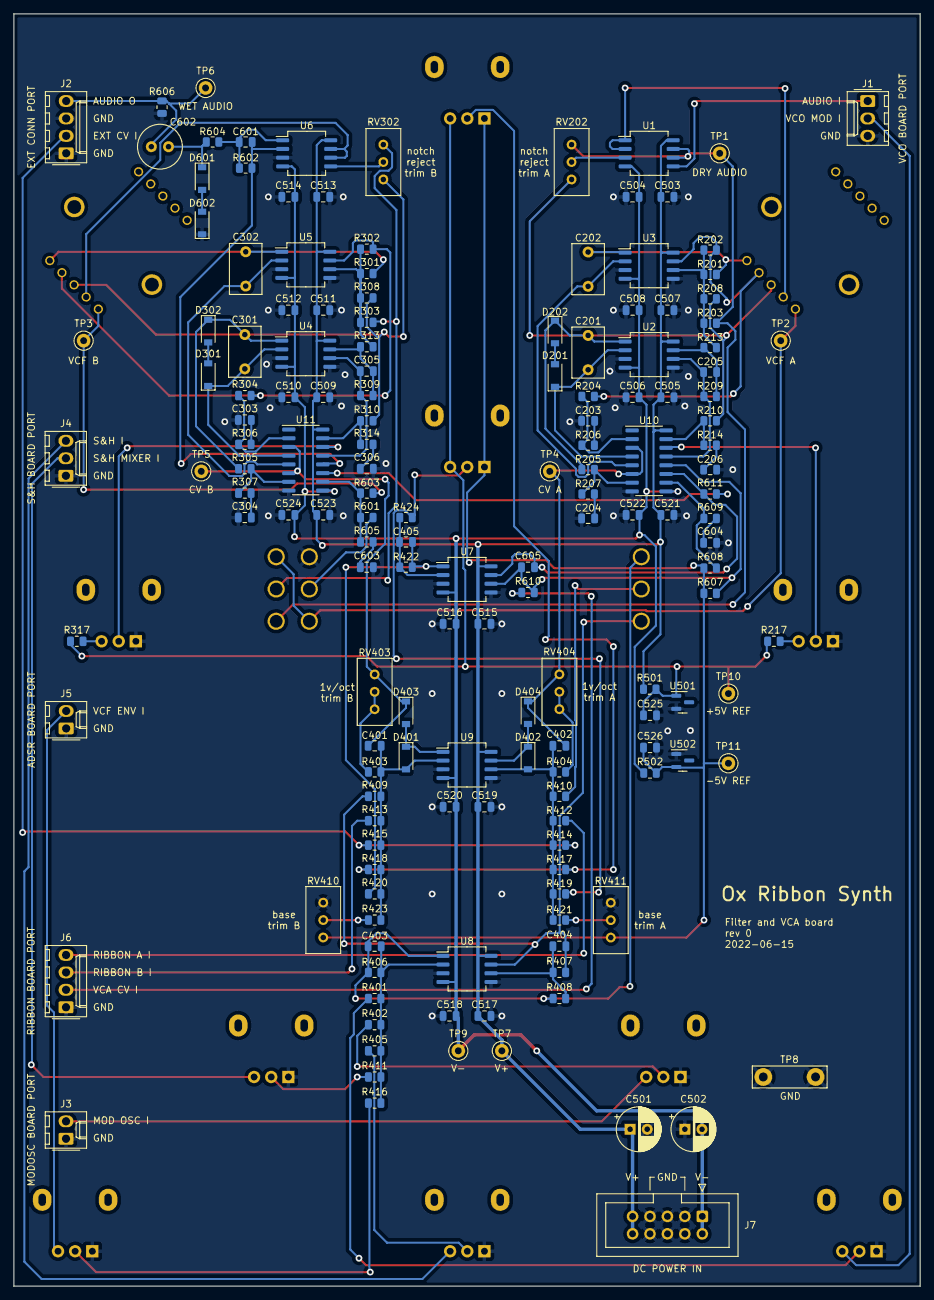
[picture p98: board VCF_VCA_board.kicad_pcb from below]

Board: 2 copper layers, 132.1 x 185.4 mm, 171 parts (158 on the bottom side), 94 nets.

Other parts of the board:
C301, C302: 220p; C_Rect_L7.2mm_W4.5mm_P5.00mm_FKS2_FKP2_MKS2_MKP2
C303, C304, C306: 560p; C_0805_2012Metric
C305: C; C_0805_2012Metric
D301, D302: 3v9; D_SOD-123
R301, R302, R303, R304, R305, R309, R313: 30k; R_0805_2012Metric
R306, R307, R314: 510; R_0805_2012Metric
R308: 270k; R_0805_2012Metric
R310: 15k; R_0805_2012Metric
R317: R; R_0805_2012Metric
RV301: 100k; Potentiometer_Alpha_RD901F-40-00D_Single_Vertical
RV302: 50k; Potentiometer_Bourns_3296W_Vertical

Their connections:
+5V REF: R317.1; also elsewhere on the board
/SVF_B/BP_OUT: C301.2, D302.1 (K), R305.1, R308.2, R310.2, RV302.3; also elsewhere on the board
/SVF_B/HP_OUT: R302.2, R304.1; also elsewhere on the board
/SVF_B/LP_OUT: C302.2, R301.2; also elsewhere on the board
/SVF_B/SIGNAL_IN: R303.1, RV302.1; also elsewhere on the board
unnamed 35: C301.1, D301.1 (K); also elsewhere on the board
unnamed 36: C302.1; also elsewhere on the board
unnamed: C303.1, R306.2
unnamed: C304.1, R307.2
unnamed 39: C305.1, R309.2, R313.2; also elsewhere on the board
unnamed 40: C305.2, R309.1; also elsewhere on the board
unnamed: C306.1, R314.2
unnamed: D301.2 (A), D302.2 (A)
unnamed 68: R301.1, R302.1, R303.2, R308.1, R313.1; also elsewhere on the board
unnamed 69: R304.2, R306.1; also elsewhere on the board
unnamed 70: R305.2, R307.1; also elsewhere on the board
unnamed 71: R310.1, R314.1; also elsewhere on the board
unnamed: R317.2, RV301.3
unnamed 90: RV301.2; also elsewhere on the board
unnamed 91: RV302.2; also elsewhere on the board
