JordanAceto/josh_Ox_ribbon_synth/summer_2022_refurb/ADSR_board/ADSR_board.kicad_pcb

## KiCad design summer_2022_refurb/ADSR_board/ADSR_board.kicad_pcb (2022-06-15, an earlier design)

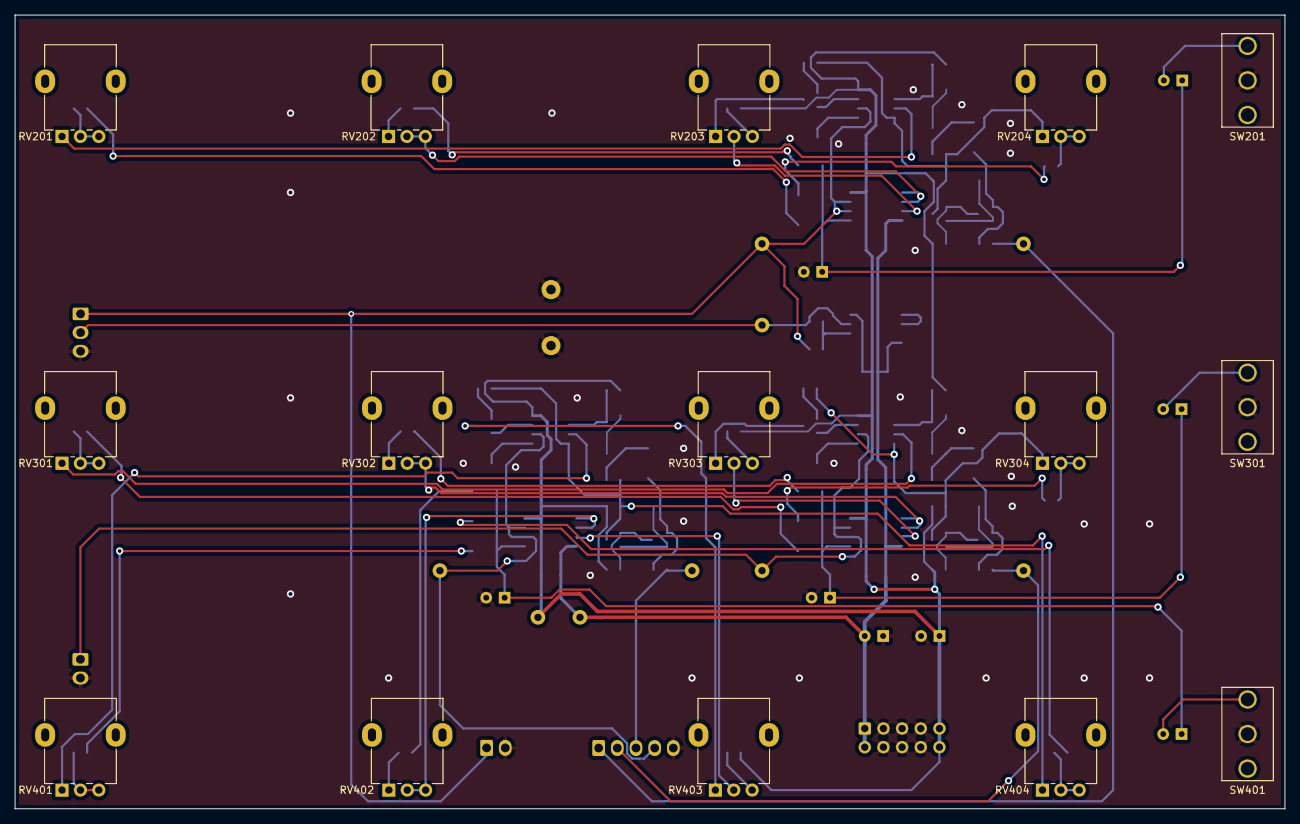
[picture p99: board summer_2022_refurb/ADSR_board/ADSR_board.kicad_pcb from above]

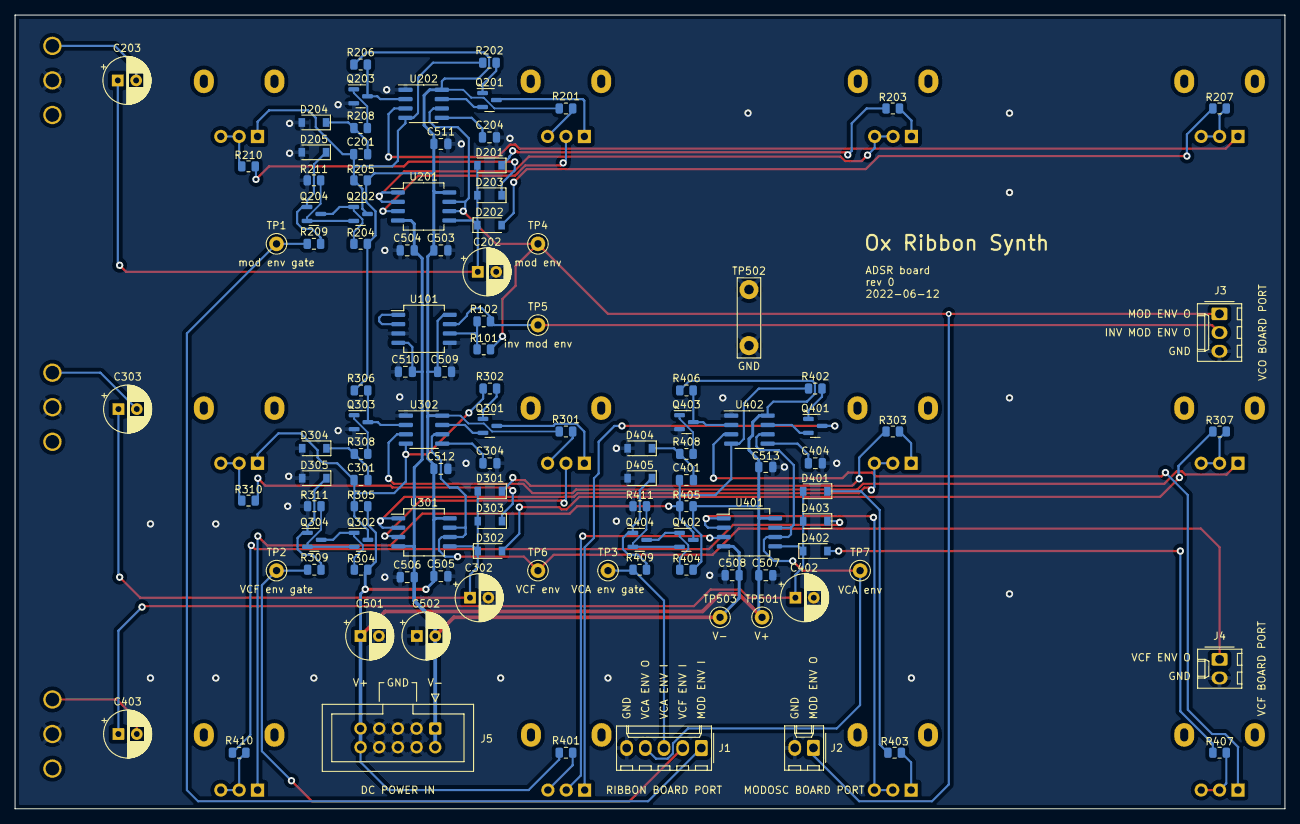
[picture p100: board summer_2022_refurb/ADSR_board/ADSR_board.kicad_pcb from below]

Board: 2 copper layers, 172.7 x 107.9 mm, 124 parts (109 on the bottom side), 81 nets.

Parts:
C201, C204, C301, C304, C401, C404: 10n; C_0805_2012Metric
C202, C302, C402: 2u2; CP_Radial_D6.3mm_P2.50mm
C203, C303, C403: 22u; CP_Radial_D6.3mm_P2.50mm
C501, C502: 10u; CP_Radial_D6.3mm_P2.50mm
C503, C504, C505, C506, C507, C508, C509, C510, C511, C512, C513: 100n; C_0805_2012Metric
D201, D202, D203, D204, D205, D301, D302, D303, D304, D305, D401, D402, D403, D404, D405: 1N4148W; D_SOD-123
J1: ribbon_port; Molex_KK-254_AE-6410-05A_1x05_P2.54mm_Vertical
J2: modosc_port; Molex_KK-254_AE-6410-02A_1x02_P2.54mm_Vertical
J3: VCO_port; Molex_KK-254_AE-6410-03A_1x03_P2.54mm_Vertical
J4: VCF_port; Molex_KK-254_AE-6410-02A_1x02_P2.54mm_Vertical
J5: power_entry; IDC-Header_2x05_P2.54mm_Vertical
Q201, Q301, Q401: 2N7002; SOT-23
Q202, Q203, Q204, Q302, Q303, Q304, Q402, Q403, Q404: MMBT3904; SOT-23
R101, R102, R209, R309, R409: 100k; R_0805_2012Metric
R201, R301, R401: 4k7; R_0805_2012Metric
R202, R302, R402: 1M; R_0805_2012Metric
R203, R207, R210, R303, R307, R310, R403, R407, R410: R; R_0805_2012Metric
R204, R205, R206, R208, R304, R305, R306, R308, R404, R405, R406, R408: 10k; R_0805_2012Metric
R211, R311, R411: 22; R_0805_2012Metric
RV201, RV202, RV204, RV301, RV302, RV304, RV401, RV402, RV404: 500kA; Potentiometer_Alpha_RD901F-40-00D_Single_Vertical
RV203, RV303, RV403: 10k; Potentiometer_Alpha_RD901F-40-00D_Single_Vertical
SW201, SW301, SW401: SW_SPDT; SPDT_mini_toggle
TP1: mod env gate; TestPoint_Keystone_5000-5004_Miniature
TP2: VCF env gate; TestPoint_Keystone_5000-5004_Miniature
TP3: VCA env gate; TestPoint_Keystone_5000-5004_Miniature
TP4: mod env; TestPoint_Keystone_5000-5004_Miniature
TP5: inv mod env; TestPoint_Keystone_5000-5004_Miniature
TP6: VCF env; TestPoint_Keystone_5000-5004_Miniature
TP7: VCA env; TestPoint_Keystone_5000-5004_Miniature
TP501: V+; TestPoint_Keystone_5000-5004_Miniature
TP502: GND; TestPoint_Bridge_Pitch7.62mm_Drill1.3mm
TP503: V-; TestPoint_Keystone_5000-5004_Miniature
U101, U201, U301, U401: TL072; SO-8_5.3x6.2mm_P1.27mm
U202, U302, U402: LM555xM; SOIC-8_3.9x4.9mm_P1.27mm

Connections:
+15V: C501.1, C503.1, C505.1, C507.1, C509.1, C511.1, C512.1, C513.1, J5.9, J5.10, R201.1, R204.1, R205.1, R206.1, R301.1, R304.1, R305.1, R306.1, R401.1, R404.1, R405.1, R406.1, TP501.1, U101.8 (V+), U201.8 (V+), U202.8 (VCC), U301.8 (V+), U302.8 (VCC), U401.8 (V+), U402.8 (VCC)
-15V: C502.2, C504.2, C506.2, C508.2, C510.2, J5.1, J5.2, TP503.1, U101.4 (V-), U201.4 (V-), U301.4 (V-), U401.4 (V-)
/VCA_ADSR/GATE: J1.3, R409.1, TP3.1
/VCA_ENV: J1.4, TP7.1, U401.6 (-), U401.7, U402.6 (THR)
/VCF_ADSR/GATE: J1.2, R309.1, TP2.1
/VCF_ADSR/OUT: J4.1, TP6.1, U301.6 (-), U301.7, U302.6 (THR)
/modulation_ADSR/GATE: J1.1, R209.1, TP1.1
/modulation_ADSR/OUT: J2.1, J3.1, R101.1, TP4.1, U201.6 (-), U201.7, U202.6 (THR)
GND: C202.2, C204.2, C302.2, C304.2, C402.2, C404.2, C501.2, C502.1, C503.2, C504.1, C505.2, C506.1, C507.2, C508.1, C509.2, C510.1, C511.2, C512.2, C513.2, D204.2 (A), D205.2 (A), D304.2 (A), D305.2 (A), D404.2 (A), D405.2 (A), J1.5, J2.2, J3.3, J4.2, J5.3, J5.4, J5.5, J5.6, J5.7, J5.8, Q203.2 (E), Q303.2 (E), Q403.2 (E), R211.2, R311.2, R411.2, SW201.2 (B), SW301.2 (B), SW401.2 (B), TP502.1, U101.3 (+), U101.5 (+), U202.1 (GND), U302.1 (GND), U402.1 (GND)
unnamed: C201.1, Q202.3 (C), R202.1, R205.2, RV204.1, U202.4 (R)
unnamed: C201.2, D204.1 (K), R208.1
unnamed: C202.1, C203.1, D201.2 (A), D202.1 (K), D203.2 (A), U201.5 (+)
unnamed: C203.2, SW201.3 (C)
unnamed: C204.1, U202.5 (CV)
unnamed: C301.1, Q302.3 (C), R302.1, R305.2, RV304.1, U302.4 (R)
unnamed: C301.2, D304.1 (K), R308.1
unnamed: C302.1, C303.1, D301.2 (A), D302.1 (K), D303.2 (A), U301.5 (+)
unnamed: C303.2, SW301.3 (C)
unnamed: C304.1, U302.5 (CV)
unnamed: C401.1, Q402.3 (C), R402.1, R405.2, RV404.1, U402.4 (R)
unnamed: C401.2, D404.1 (K), R408.1
unnamed: C402.1, C403.1, D401.2 (A), D402.1 (K), D403.2 (A), U401.5 (+)
unnamed: C403.2, SW401.3 (C)
unnamed: C404.1, U402.5 (CV)
unnamed: D201.1 (K), R203.2
unnamed: D202.2 (A), R207.2
unnamed: D203.1 (K), R210.1
unnamed: D205.1 (K), Q204.1 (B), R209.2
unnamed: D301.1 (K), R303.2
unnamed: D302.2 (A), R307.2
unnamed: D303.1 (K), R310.1
unnamed: D305.1 (K), Q304.1 (B), R309.2
unnamed: D401.1 (K), R403.2
unnamed: D402.2 (A), R407.2
unnamed: D403.1 (K), R410.1
unnamed: D405.1 (K), Q404.1 (B), R409.2
unnamed: Q201.1 (G), R202.2
unnamed: Q201.2 (S), U202.7 (DIS)
unnamed: Q201.3 (D), RV203.1
unnamed: Q202.1 (B), Q204.3 (C), R204.2
unnamed: Q202.2 (E), Q204.2 (E), R211.1
unnamed: Q203.1 (B), R208.2
unnamed: Q203.3 (C), R206.2, U202.2 (TR)
unnamed: Q301.1 (G), R302.2
unnamed: Q301.2 (S), U302.7 (DIS)
unnamed: Q301.3 (D), RV303.1
unnamed: Q302.1 (B), Q304.3 (C), R304.2
unnamed: Q302.2 (E), Q304.2 (E), R311.1
unnamed: Q303.1 (B), R308.2
unnamed: Q303.3 (C), R306.2, U302.2 (TR)
unnamed: Q401.1 (G), R402.2
unnamed: Q401.2 (S), U402.7 (DIS)
unnamed: Q401.3 (D), RV403.1
unnamed: Q402.1 (B), Q404.3 (C), R404.2
unnamed: Q402.2 (E), Q404.2 (E), R411.1
unnamed: Q403.1 (B), R408.2
unnamed: Q403.3 (C), R406.2, U402.2 (TR)
unnamed: R101.2, R102.1, U101.6 (-)
unnamed: J3.2, R102.2, TP5.1, U101.7
unnamed: R201.2, RV203.3
unnamed: R203.1, RV202.1
unnamed: R207.1, RV201.2, RV201.3
unnamed: R210.2, RV204.2, RV204.3
unnamed: R301.2, RV303.3
unnamed: R303.1, RV302.1
unnamed: R307.1, RV301.2, RV301.3
unnamed: R310.2, RV304.2, RV304.3
unnamed: R401.2, RV403.3
unnamed: R403.1, RV402.1
unnamed: R407.1, RV401.2, RV401.3
unnamed: R410.2, RV404.2, RV404.3
unnamed: RV201.1, U202.3 (Q)
unnamed: RV202.2, RV202.3, U201.1, U201.2 (-)
unnamed: RV203.2, U201.3 (+)
unnamed: RV301.1, U302.3 (Q)
unnamed: RV302.2, RV302.3, U301.1, U301.2 (-)
unnamed: RV303.2, U301.3 (+)
unnamed: RV401.1, U402.3 (Q)
unnamed: RV402.2, RV402.3, U401.1, U401.2 (-)
unnamed: RV403.2, U401.3 (+)
unnamed: U101.1, U101.2 (-)
