JordanAceto/josh_Ox_ribbon_synth/summer_2022_refurb/main_VCO_board/kicad_6_docs/main_VCO_board.kicad_pcb

## KiCad design summer_2022_refurb/main_VCO_board/kicad_6_docs/main_VCO_board.kicad_pcb (2022-06-19)

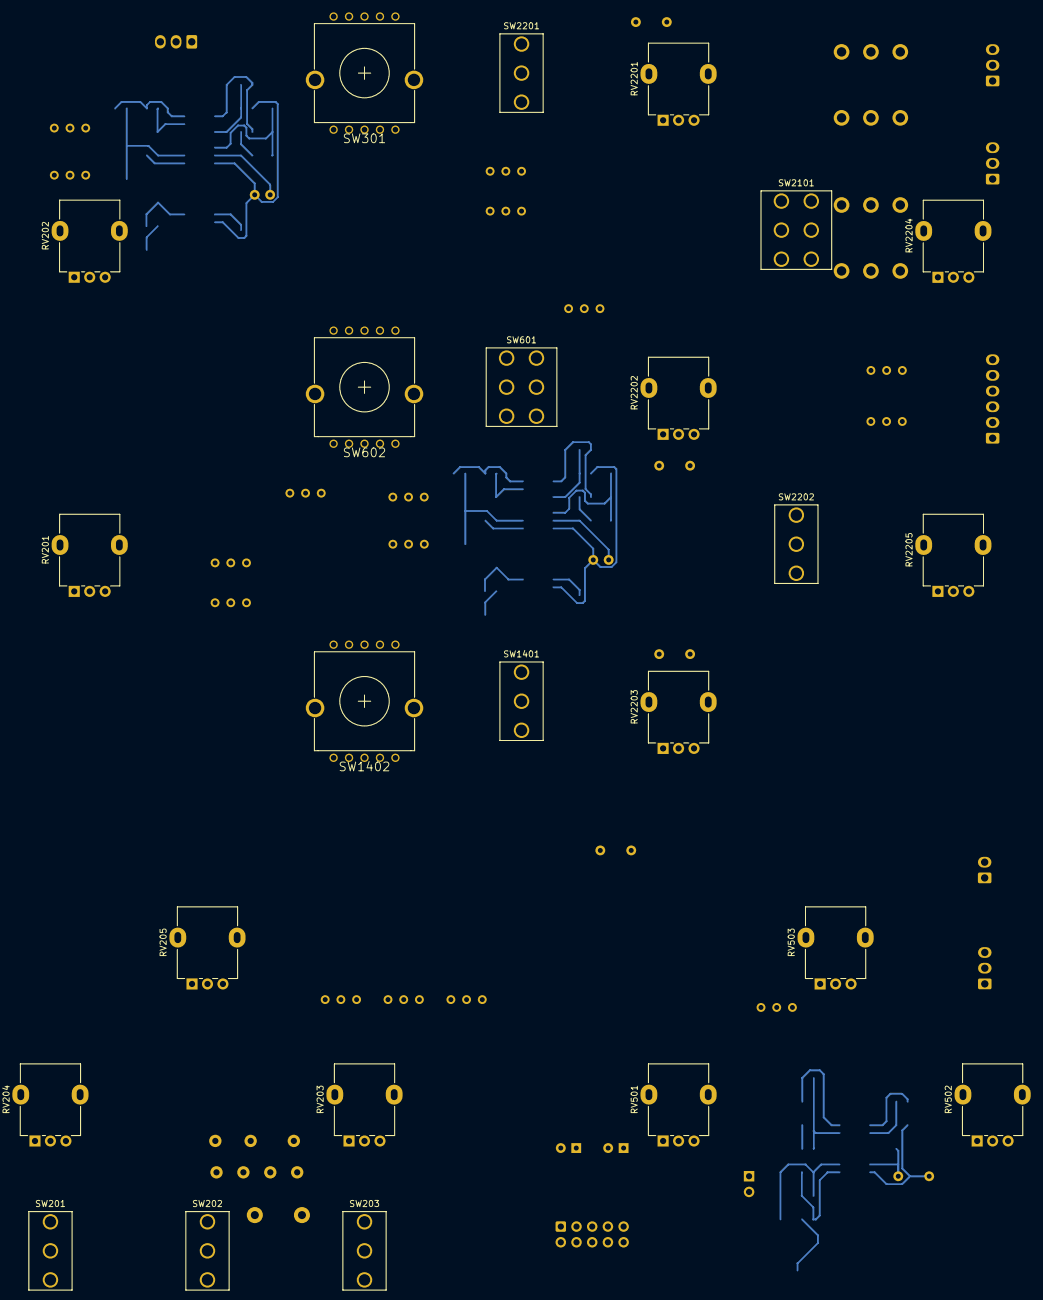
[picture p101: board main_VCO_board.kicad_pcb from above]

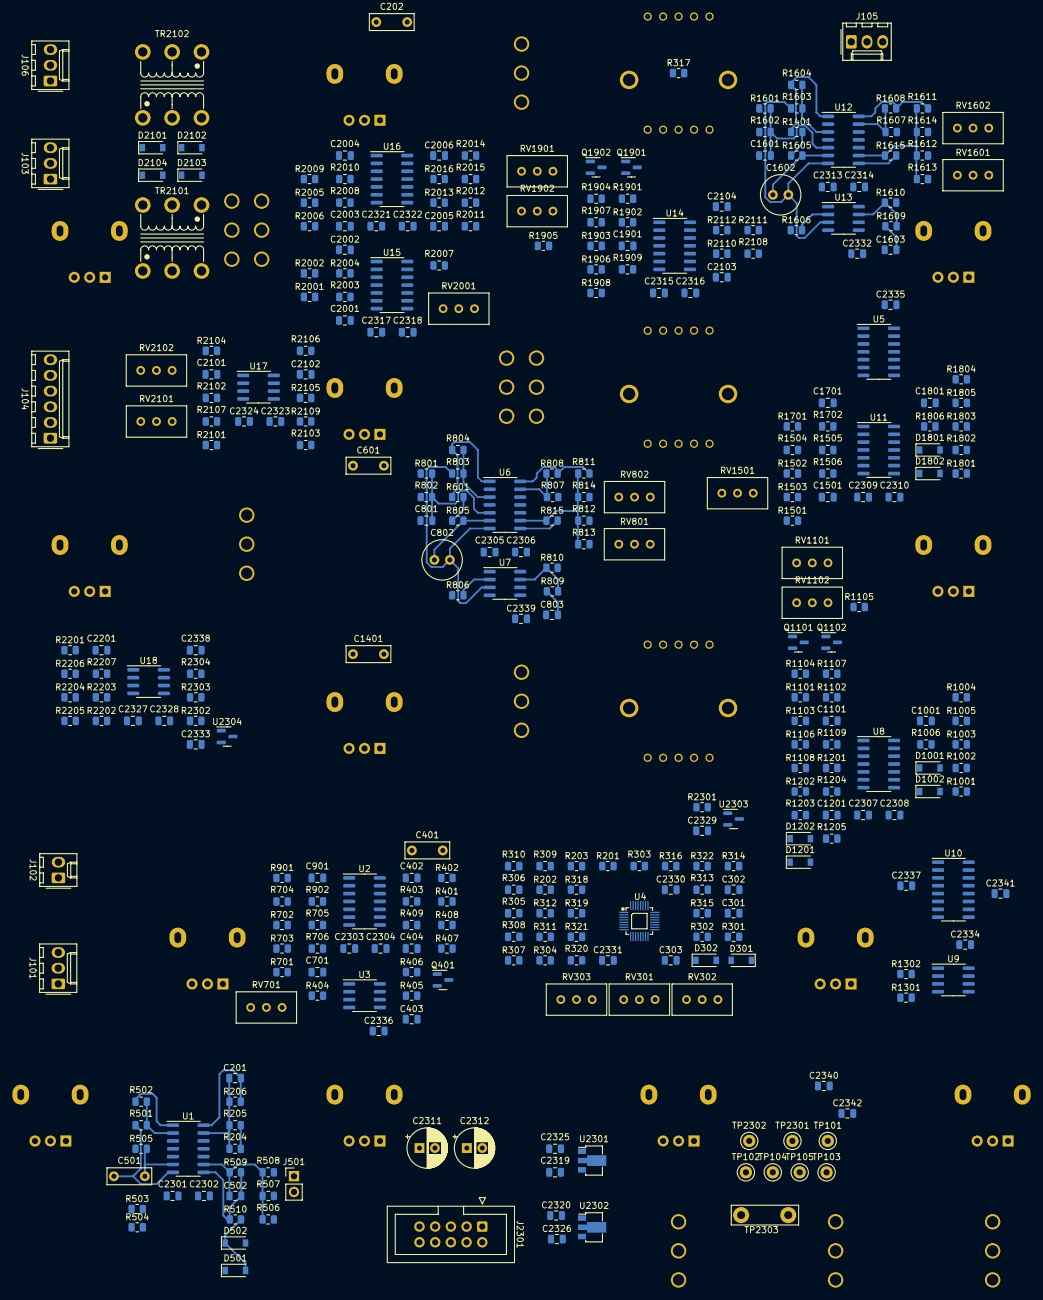
[picture p102: board main_VCO_board.kicad_pcb from below]

Board: 2 copper layers, 351 parts (327 on the bottom side), 214 nets.

Parts:
C201, C701, C901, C1001, C1101, C1501, C1701, C1801, C1901: C; C_0805_2012Metric
C202, C501, C601, C1401: 220n; C_Rect_L7.0mm_W2.5mm_P5.00mm
C301, C801, C1601: 10u; C_0805_2012Metric
C302: 10N; C_0805_2012Metric
C303: 3N9 COG; C_0805_2012Metric
C401: 100n; C_Rect_L7.0mm_W2.5mm_P5.00mm
C402: 20p; C_0805_2012Metric
C403, C404, C502, C803, C1603, C2003, C2004, C2101, C2102, C2103, C2104: 100p; C_0805_2012Metric
C802, C1602: 10u BP; C_Radial_D6.3mm_H5.0mm_P2.50mm
C1201, C2001, C2002, C2005, C2006, C2201: 10p; C_0805_2012Metric
C2301, C2302, C2303, C2304, C2305, C2306, C2307, C2308, C2309, C2310, C2313, C2314, C2315, C2316, C2317, C2318, C2321, C2322, C2323, C2324, C2325, C2326, C2327, C2328, C2329, C2330, C2331, C2332, C2333, C2334, C2335, C2336, C2337, C2338, C2339, C2340, C2341, C2342: 100n; C_0805_2012Metric
C2311, C2312: 10u; CP_Radial_D6.3mm_P2.50mm
C2319, C2320: 330n; C_0805_2012Metric
D301, D302, D1001, D1002, D1801, D1802: 1N4148W; D_SOD-123
D501, D502: D_Schottky; D_SOD-123
D1201, D1202: 5v1; D_SOD-123
D2101, D2102, D2103, D2104: BAT48ZFILM; D_SOD-123
J101: ribbon_port; Molex_KK-254_AE-6410-03A_1x03_P2.54mm_Vertical
J102: modosc_port; Molex_KK-254_AE-6410-02A_1x02_P2.54mm_Vertical
J103: ADSR_port; Molex_KK-254_AE-6410-03A_1x03_P2.54mm_Vertical
J104: S&H_port; Molex_KK-254_AE-6410-06A_1x06_P2.54mm_Vertical
J105: ext_con; Molex_KK-254_AE-6410-03A_1x03_P2.54mm_Vertical
J106: vcf_port; Molex_KK-254_AE-6410-03A_1x03_P2.54mm_Vertical
J501: aux_pwm; PinHeader_1x02_P2.54mm_Vertical
J2301: power_entry; IDC-Header_2x05_P2.54mm_Vertical
Q401: 2N7002; SOT-23
Q1101, Q1102, Q1901, Q1902: MMBT3904; SOT-23
R201: 150k; R_0805_2012Metric
R202: 56k; R_0805_2012Metric
R203, R804, R1004, R1006, R1604, R1804, R1806: 120k; R_0805_2012Metric
R204, R205, R311, R317, R401, R402, R403, R405, R501, R505, R509, R704, R705, R706, R805, R807, R808, R811, R813, R815, R902, R1504, R1505, R1506, R1605, R1607, R1608, R1611, R1613, R1615, R1702, R2002, R2004, R2008, R2009, R2010, R2011, R2012, R2015, R2101, R2102, R2103, R2105, R2107, R2108, R2109, R2110, R2112, R2201, R2202, R2203, R2204, R2205, R2206: 100k; R_0805_2012Metric
R206, R702, R703, R814, R1502, R1503, R1614, R2005, R2006: 200k; R_0805_2012Metric
R301, R302, R322, R406, R504, R803, R1103, R1106, R1201, R1301, R1302, R1603, R1903, R1906, R2001, R2303, R2304: 10k; R_0805_2012Metric
R303, R304, R306, R307, R308, R309, R310: 100K; R_0805_2012Metric
R305: 1m; R_0805_2012Metric
R312: 270K; R_0805_2012Metric
R313: 47K; R_0805_2012Metric
R314: 270; R_0805_2012Metric
R315: 470K; R_0805_2012Metric
R316, R2302: 4k7; R_0805_2012Metric
R318: 3K9; R_0805_2012Metric
R319, R321: 4K7; R_0805_2012Metric
R320: 12K; R_0805_2012Metric
R404, R503: 100; R_0805_2012Metric
R407, R408, R409, R2013: 20k; R_0805_2012Metric
R502: 270k; R_0805_2012Metric
R506, R2014: 220k; R_0805_2012Metric
R507, R508, R701, R812, R1501, R1612, R2016: 180k; R_0805_2012Metric
R510, R806, R810, R1606, R1610: 1k; R_0805_2012Metric
R601: 1M5; R_0805_2012Metric
R801, R1601: 8k2; R_0805_2012Metric
R802, R1602: 2k7; R_0805_2012Metric
R809, R1609: 51k; R_0805_2012Metric
R901, R1701: 33k; R_0805_2012Metric
R1001, R1002, R1005, R1801, R1802, R1805: 15k; R_0805_2012Metric
R1003, R1803: 7k5; R_0805_2012Metric
R1101, R1901: 27k; R_0805_2012Metric
R1102, R1107, R1205, R1902, R1907: 2k2; R_0805_2012Metric
R1104, R1904: 390; R_0805_2012Metric
R1105, R1905: 18k; R_0805_2012Metric
R1108, R1109, R1908, R1909: 12k; R_0805_2012Metric
R1202, R1203, R2111: R; R_0805_2012Metric
R1204, R2003: 10M; R_0805_2012Metric
R1401: 2M2; R_0805_2012Metric
R2007: 2k; R_0805_2012Metric
R2104, R2106: 330; R_0805_2012Metric
R2207: 82k; R_0805_2012Metric
R2301: 1k8; R_0805_2012Metric
RV201, RV202: 10k; Potentiometer_Alpha_RD901F-40-00D_Single_Vertical
RV203, RV204, RV205, RV501, RV502, RV503, RV2201, RV2202, RV2203, RV2204, RV2205: 100k; Potentiometer_Alpha_RD901F-40-00D_Single_Vertical
RV301, RV302, RV303, RV802, RV1602: 5k; Potentiometer_Bourns_3296W_Vertical
RV701, RV801, RV1101, RV1102, RV1501, RV1601, RV1901, RV1902, RV2001: 50k; Potentiometer_Bourns_3296W_Vertical
RV2101, RV2102: 20k; Potentiometer_Bourns_3296W_Vertical
SW201, SW202, SW203, SW1401: SW_SPDT_CO; SPDT_mini_toggle
SW301, SW602, SW1402: SR1712F-0204; SR1712F_rotary_switch
SW601, SW2101: SW_DPDT_CO; DPDT_mini_toggle
SW2201, SW2202: SW_SPDT; SPDT_mini_toggle
TP101: pwm_cv; TestPoint_Keystone_5000-5004_Miniature
TP102: oct_0; TestPoint_Keystone_5000-5004_Miniature
TP103: oct_1; TestPoint_Keystone_5000-5004_Miniature
TP104: oct_2; TestPoint_Keystone_5000-5004_Miniature
TP105: ring_mod; TestPoint_Keystone_5000-5004_Miniature
TP2301: V+; TestPoint_Keystone_5000-5004_Miniature
TP2302: V-; TestPoint_Keystone_5000-5004_Miniature
TP2303: GND; TestPoint_Bridge_Pitch7.62mm_Drill1.3mm
TR2101, TR2102: Triad_TY_141P; Triad_TY-141P
U1, U2, U6, U8, U11, U12, U14, U15, U16: TL074; SOIC-14_3.9x8.7mm_P1.27mm
U3, U7, U13: LM311; SOIC-8_3.9x4.9mm_P1.27mm
U4: SSI2130; PQN32_HandSoldering
U5: 4013; SOIC-14_3.9x8.7mm_P1.27mm
U9: LM555xM; SOIC-8_3.9x4.9mm_P1.27mm
U10: DG413xY; SOIC-16_3.9x9.9mm_P1.27mm
U17: NE5532; SOIC-8_3.9x4.9mm_P1.27mm
U18: TL072; SOIC-8_3.9x4.9mm_P1.27mm
U2301: L78L05_SOT89; SOT-89-3
U2302: L79L05_SOT89; SOT-89-3
U2303: LM4040C-2.5; SOT-23
U2304: LM4040DBZ-5; SOT-23

Connections:
+2V5 REF: C2329.1, R2301.2, U2303.1 (K)
+2V5_REF: R303.2, R320.2, R401.2, RV301.3, RV302.2, RV302.3, U4.23 (vref)
+5V: C301.2, C2325.1, C2330.1, C2332.1, C2334.1, C2335.1, C2336.1, C2339.1, C2341.1, D301.1 (K), D501.1 (K), R316.2, R317.1, R406.2, R801.1, R810.2, R1301.1, R1302.1, R1601.1, R1610.2, R2301.1, U4.27 (V+), U5.14 (VDD), U7.8 (V+), U9.8 (VCC), U10.12 (VL), U10.13 (V+), U13.8 (V+), U2301.1 (OUT)
+5V REF: C2333.1, R1004.2, R1804.2, R2302.2, R2303.2, U2304.1 (K)
+5V_REF: R203.1, R2005.1, RV201.3, RV202.3, RV503.3
+15V: C2301.1, C2303.1, C2305.1, C2307.1, C2309.1, C2311.1, C2313.1, C2315.1, C2317.1, C2319.1, C2321.1, C2323.1, C2327.1, J2301.9, J2301.10, R1103.1, R1106.1, R1903.1, R1906.1, R2302.1, TP2301.1, U1.4 (V+), U2.4 (V+), U3.8 (V+), U6.4 (V+), U8.4 (V+), U11.4 (V+), U12.4 (V+), U14.4 (V+), U15.4 (V+), U16.4 (V+), U17.8 (V+), U18.8 (V+), U2301.3 (IN)
-5V: C2326.2, C2331.2, C2337.2, C2340.2, C2342.2, D502.2 (A), U4.8 (V-), U10.4 (V-), U2302.3 (VO)
-5V REF: C2338.1, R703.1, R1503.1, R2304.1, RV802.3, RV1602.3, U18.7
-5V_REF: RV201.1, RV202.1, RV503.1
-15V: C2302.2, C2304.2, C2306.2, C2308.2, C2310.2, C2312.2, C2314.2, C2316.2, C2318.2, C2320.2, C2322.2, C2324.2, C2328.2, J2301.1, J2301.2, R1105.2, R1905.2, TP2302.1, U1.11 (V-), U2.11 (V-), U3.4 (V-), U6.11 (V-), U8.11 (V-), U11.11 (V-), U12.11 (V-), U14.11 (V-), U15.11 (V-), U16.11 (V-), U17.4 (V-), U18.4 (V-), U2302.2 (VI)
/EXT_AUDIO: J105.1, R2201.1
/MOD_OSC: J102.1, RV203.3, SW2101.1
/NOISE: J104.3, SW2202.1 (A)
/OCTAVE_0: C202.2, J104.4, J106.2, R2101.1, SW2101.3, SW2201.1 (A), TP102.1
/PWM_LFO_SQR: J101.2, R504.2
/PWM_LFO_TRI: C501.2, J104.5, R501.2, RV502.3, U1.7
/PWM_generator/PWM_CV_OUT: D501.2 (A), D502.1 (K), R201.1, R510.2, R1202.1, R2006.1, TP101.1
/audio_mixer/OUT: C2201.2, J106.1, R2207.2, U18.1
/audio_mixer/RING_MOD: RV2204.3, SW2101.5, TP105.1
/audio_mixer/SUBOSC_1: C601.2, RV2202.3, TP103.1
/audio_mixer/SUBOSC_2: C1401.2, RV2203.3, TP104.1
/main_VCO/EXT_CV: J105.2, R306.2
/main_VCO/MOD_ENV_DOWN: J103.2, SW201.3
/main_VCO/MOD_ENV_UP: J103.1, SW201.1
/main_VCO/RIBBON_CV: J101.1, R307.2
/main_VCO/S_AND_H: J104.1, SW202.1
/main_VCO/S_AND_H_MIXER: J104.2, SW202.3
/main_VCO/VCO_core/COARSE_TUNE_IN: R304.2, RV202.2
/main_VCO/VCO_core/FINE_TUNE_IN: R305.2, RV201.2
/main_VCO/VCO_core/LIN_FM_IN: C404.1, R315.2, R409.1, U2.8
/main_VCO/VCO_core/PWM_CV_IN: R201.2, R202.1, R203.2, U4.32 (pwm_in_+)
/main_VCO/VCO_core/SWITCHED_OUT: R204.1, R205.1, R322.2, U4.25 (mix_out)
/main_VCO/VCO_core/TIME_REV_IN: C403.1, Q401.1 (G), R406.1, U3.7, U4.18 (time_rev)
/main_VCO/VCO_core/V_PER_OCT_IN_3: R308.2, RV204.2
/main_VCO/VCO_core/V_PER_OCT_IN_4: R309.2, RV205.2
/main_VCO/VCO_core/V_PER_OCT_IN_5: R310.2, SW203.1
/main_VCO/lin_FM_conditioner/LIN_FM_IN: C401.2, SW203.3
/sub_osc_1/OCT_DWN_SAW: C701.2, R705.2, R706.2, SW601.3, U2.7, U10.2
/sub_osc_1/OCT_DWN_SQR: RV701.1, U5.1 (Q), U10.6
/sub_osc_1/SAW_IN: R702.1, SW601.1, U4.29 (saw_out), U10.15
/sub_osc_1/SQUARE_IN: R316.1, U4.28 (square_out), U5.3 (C), U10.10
/sub_osc_1/SQUARE_OUT: U5.11 (C), U10.7, U10.11
/sub_osc_1/STATIC_SAW_OUT: R1502.1, SW1401.1, U10.3, U10.14
/sub_osc_1/basic_pulse_shaper/PULSE_OUT: D1201.1 (K), R1205.2, SW602.5
/sub_osc_1/basic_pulse_shaper/SIGNAL_IN: C1001.2, R1006.1, R1201.1, RV1101.2, RV1101.3, SW602.3, U8.14
/sub_osc_1/level_shifter_1/IN: R815.2, R1001.2, R1005.2, U2.3 (+), U6.8
/sub_osc_1/level_shifter_1/OUT: C901.2, R902.2, SW602.4, U2.1
/sub_osc_1/passthrough_switching/SWITCH_0: R1302.2, SW601.6, U9.2 (TR)
/sub_osc_1/passthrough_switching/SWITCH_1: R1301.2, SW601.4, U9.4 (R)
/sub_osc_1/passthrough_switching/SWITCH_CTL: U9.3 (Q), U10.1, U10.8, U10.9, U10.16
/sub_osc_1/saw_animator_1/RATE_R_1: R601.1, R804.2, U6.1
/sub_osc_1/saw_animator_1/RATE_R_2: R601.2, R805.1
/sub_osc_1/saw_animator_1/SAW_IN: R806.1, R807.1, SW601.2
/sub_osc_1/tri_to_sine_shaper_1/SINE_OUT: C1101.2, R1109.2, SW602.2, U8.1
/sub_osc_2/harmonic_pulse_shaper/PULSE_OUT: C2006.2, R2016.2, SW1402.5, U16.14
/sub_osc_2/harmonic_pulse_shaper/SIGNAL_IN: C1801.2, R1806.1, R2001.1, R2002.1, RV1901.2, RV1901.3, SW1402.3, U11.14
/sub_osc_2/level_shifter_2/IN: R1615.2, R1801.2, R1805.2, U11.3 (+), U12.8
/sub_osc_2/level_shifter_2/OUT: C1701.2, R1702.2, SW1402.4, U11.1
/sub_osc_2/octave_divider_2/OCTAVE_DOWN_SAW_OUT: C1501.2, R1505.2, R1506.2, SW1401.3, U11.7
/sub_osc_2/octave_divider_2/OCTAVE_DOWN_SQR_OUT: RV1501.1, U5.13 (Q)
/sub_osc_2/saw_animator_2/RATE_R_1: R1401.1, R1604.2, U12.1
/sub_osc_2/saw_animator_2/RATE_R_2: R1401.2, R1605.1
/sub_osc_2/saw_animator_2/SAW_IN: R1606.1, R1607.1, SW1401.2
/sub_osc_2/tri_to_sine_shaper_2/SINE_OUT: C1901.2, R1909.2, SW1402.2, U14.1
GND: C302.2, C303.2, C801.2, C1601.2, C2301.2, C2302.1, C2303.2, C2304.1, C2305.2, C2306.1, C2307.2, C2308.1, C2309.2, C2310.1, C2311.2, C2312.1, C2313.2, C2314.1, C2315.2, C2316.1, C2317.2, C2318.1, C2319.2, C2320.1, C2321.2, C2322.1, C2323.2, C2324.1, C2325.2, C2326.1, C2327.2, C2328.1, C2329.2, C2330.2, C2331.1, C2332.2, C2333.2, C2334.2, C2335.2, C2336.2, C2337.1, C2339.2, C2340.1, C2341.2, C2342.1, D302.2 (A), D1202.1 (K), J101.3, J102.2, J103.3, J104.6, J105.3, J106.3, J501.2, J2301.3, J2301.4, J2301.5, J2301.6, J2301.7, J2301.8, Q401.2 (S), R202.2, R302.2, R319.1, R321.1, R322.1, R404.1, R503.2, R704.2, R802.2, R901.1, R1102.2, R1107.2, R1108.1, R1203.2, R1504.2, R1602.2, R1701.1, R1902.2, R1907.2, R1908.1, RV203.1, RV204.1, RV205.1, RV301.1, RV303.1, RV502.1, RV802.1, RV1602.1, RV2001.1, RV2201.1, RV2202.1, RV2203.1, RV2204.1, RV2205.1, SW601.5, TP2303.1, TR2101.3, TR2102.2, TR2102.6, U1.3 (+), U1.5 (+), U1.10 (+), U1.12 (+), U2.12 (+), U3.1 (GND), U4.15 (dgnd), U4.16 (agnd), U4.20 (hft_base), U5.4 (R), U5.6 (S), U5.7 (VSS), U5.8 (S), U5.10 (R), U6.10 (+), U6.12 (+), U7.1 (GND), U7.4 (V-), U8.10 (+), U8.12 (+), U9.1 (GND), U9.6 (THR), U10.5 (GND), U11.10 (+), U11.12 (+), U12.10 (+), U12.12 (+), U13.1 (GND), U13.4 (V-), U14.10 (+), U14.12 (+), U15.3 (+), U15.6 (-), U16.3 (+), U16.5 (+), U16.10 (+), U16.12 (+), U17.3 (+), U17.5 (+), U18.3 (+), U18.5 (+), U2301.2 (GND), U2302.1 (GND), U2303.2 (A), U2304.2 (A)
unnamed: C201.1, R204.2, R205.2, R206.1, U1.13 (-)
unnamed: C201.2, C202.1, R206.2, U1.14
unnamed: C301.1, R301.1
unnamed: C302.1, R314.2
unnamed: C303.1, U4.14 (tcap)
unnamed: C401.1, R402.2
unnamed: C402.1, R403.1, R407.2, R408.2, U2.14, U3.3 (-)
unnamed: C402.2, R401.1, R402.1, R403.2, U2.13 (-)
unnamed: C403.2, R405.1
unnamed: C404.2, R407.1, R409.2, U2.9 (-)
unnamed: C501.1, R505.2, U1.6 (-)
unnamed: C502.1, R506.2, R507.2, R508.2, R509.1, U1.9 (-)
unnamed: C502.2, R509.2, R510.1, U1.8
unnamed: C601.1, SW602.1
unnamed: C701.1, R701.2, R703.2, R705.1, R706.1, U2.6 (-)
unnamed: C801.1, R801.2, R802.1, U6.2 (-), U6.5 (+)
unnamed: C802.1, R805.2, U6.6 (-)
unnamed: C802.2, R803.2, R813.2, U6.7, U7.3 (-)
unnamed: C803.1, R806.2, U7.2 (+)
unnamed: C803.2, R809.1
unnamed: C1001.1, R1003.1, R1004.1, R1005.1, R1006.2, U8.13 (-)
unnamed: C1101.1, Q1101.3 (C), R1103.2, R1109.1, U8.2 (-)
unnamed: C1201.1, R1201.2, R1204.1, U8.5 (+)
unnamed: C1201.2, R1204.2, R1205.1, U8.7
unnamed: C1401.1, SW1402.1
unnamed: C1501.1, R1501.2, R1503.2, R1505.1, R1506.1, U11.6 (-)
unnamed: C1601.1, R1601.2, R1602.1, U12.2 (-), U12.5 (+)
unnamed: C1602.1, R1605.2, U12.6 (-)
unnamed: C1602.2, R1603.2, R1613.2, U12.7, U13.3 (-)
unnamed: C1603.1, R1606.2, U13.2 (+)
unnamed: C1603.2, R1609.1
unnamed: C1801.1, R1803.1, R1804.1, R1805.1, R1806.2, U11.13 (-)
unnamed: C1901.1, Q1901.3 (C), R1903.2, R1909.1, U14.2 (-)
unnamed: C2001.1, R2001.2, R2003.1, U15.5 (+)
unnamed: C2001.2, R2003.2, RV2001.3, U15.7
unnamed: C2002.1, R2002.2, R2004.1, U15.2 (-)
unnamed: C2002.2, R2004.2, R2007.1, U15.1
unnamed: C2003.1, R2005.2, R2006.2, R2008.1, U16.6 (-)
unnamed: C2003.2, R2008.2, R2009.1, U15.10 (+), U16.7
unnamed: C2004.1, R2009.2, R2010.1, U16.2 (-)
unnamed: C2004.2, R2010.2, U15.12 (+), U16.1
unnamed: C2005.1, R2011.2, R2012.2, R2013.1, U16.9 (-)
unnamed: C2005.2, R2013.2, R2015.1, U16.8
unnamed: C2006.1, R2014.2, R2015.2, R2016.1, U16.13 (-)
unnamed: C2101.1, R2101.2, R2102.1, U17.2 (-)
unnamed: C2101.2, R2104.1, U17.1
unnamed: C2102.1, R2103.2, R2105.1, U17.6 (-)
unnamed: C2102.2, R2106.1, U17.7
unnamed: C2103.1, R2108.2, R2110.1, RV2101.1, RV2102.1, U14.9 (-)
unnamed: C2103.2, R2110.2, R2111.1, U14.8
unnamed: C2104.1, R2111.2, R2112.1, RV2101.3, RV2102.3, U14.13 (-)
unnamed: C2104.2, R2112.2, SW2101.4, SW2101.6, U14.14
unnamed: C2201.1, R2201.2, R2202.2, R2203.2, R2204.2, R2205.2, R2206.2, R2207.1, U18.2 (-)
unnamed: C2338.2, R2303.1, R2304.2, U18.6 (-)
unnamed: D301.2 (A), D302.1 (K), R301.2, R302.1, U4.17 (hard_sync)
unnamed: D1001.1 (K), R1001.1, R1002.2, U8.9 (-)
unnamed: D1001.2 (A), D1002.1 (K), U8.8
unnamed: D1002.2 (A), R1002.1, R1003.2
unnamed: D1201.2 (A), D1202.2 (A)
unnamed: D1801.1 (K), R1801.1, R1802.2, U11.9 (-)
unnamed: D1801.2 (A), D1802.1 (K), U11.8
unnamed: D1802.2 (A), R1802.1, R1803.2
unnamed: D2101.1 (K), D2103.2 (A), TR2101.4
unnamed: D2101.2 (A), D2102.1 (K), TR2102.3
unnamed: D2102.2 (A), D2104.1 (K), TR2101.6
unnamed: D2103.1 (K), D2104.2 (A), TR2102.1
unnamed: J501.1, R508.1
unnamed: Q401.3 (D), R408.1, U2.10 (+)
unnamed: Q1101.1 (B), R1101.2, R1102.1
unnamed: Q1101.2 (E), R1104.1, RV1102.3
unnamed: Q1102.1 (B), R1107.1
unnamed: Q1102.2 (E), R1104.2, RV1102.1
unnamed: Q1102.3 (C), R1106.2, R1108.2, U8.3 (+)
unnamed: Q1901.1 (B), R1901.2, R1902.1
unnamed: Q1901.2 (E), R1904.1, RV1902.3
unnamed: Q1902.1 (B), R1907.1
unnamed: Q1902.2 (E), R1904.2, RV1902.1
unnamed: Q1902.3 (C), R1906.2, R1908.2, U14.3 (+)
unnamed: R303.1, R304.1, R305.1, R306.1, R307.1, R308.1, R309.1, R310.1, R311.1, R312.2, U4.7 (expo_freq)
unnamed: R311.2, RV301.2
unnamed: R312.1, RV303.2
unnamed: R313.1, RV302.1
unnamed: R313.2, U4.22 (expo_scale)
unnamed: R314.1, U4.26 (bw_comp)
unnamed: R315.1, U4.21 (lin_freq)
unnamed: R317.2, SW301.1
unnamed: R318.1, R319.2, U4.2 (sine_in_+)
unnamed: R318.2, U4.1 (tri_out), U4.31 (pwm_in_-)
unnamed: R320.1, R321.2, U4.3 (sine_in_-)
unnamed: R404.2, R405.2, U3.2 (+)
unnamed: R501.1, R502.1, U1.2 (-)
unnamed: R502.2, R504.1, RV501.3, U1.1
unnamed: R503.1, RV501.1
unnamed: R505.1, RV501.2
unnamed: R506.1, RV502.2
unnamed: R507.1, RV503.2
unnamed: R701.1, RV701.2, RV701.3
unnamed: R702.2, R704.1, U2.5 (+)
unnamed: R803.1, R804.1, U6.3 (+)
unnamed: R807.2, R808.1, U6.13 (-)
unnamed: R808.2, R811.1, U6.14
unnamed: R809.2, R810.1, RV801.1, U7.7
unnamed: R811.2, R812.2, R813.1, R814.2, R815.1, U6.9 (-)
unnamed: R812.1, RV801.2, RV801.3
unnamed: R814.1, RV802.2
unnamed: C901.1, R901.2, R902.1, U2.2 (-)
unnamed: R1101.1, RV1101.1
unnamed: R1105.1, RV1102.2
unnamed: R1202.2, R1203.1, U8.6 (-)
unnamed: R1501.1, RV1501.2, RV1501.3
unnamed: R1502.2, R1504.1, U11.5 (+)
unnamed: R1603.1, R1604.1, U12.3 (+)
unnamed: R1607.2, R1608.1, U12.13 (-)
unnamed: R1608.2, R1611.1, U12.14
unnamed: R1609.2, R1610.1, RV1601.1, U13.7
unnamed: R1611.2, R1612.2, R1613.1, R1614.2, R1615.1, U12.9 (-)
unnamed: R1612.1, RV1601.2, RV1601.3
unnamed: R1614.1, RV1602.2
unnamed: C1701.1, R1701.2, R1702.1, U11.2 (-)
unnamed: R1901.1, RV1901.1
unnamed: R1905.1, RV1902.2
unnamed: R2007.2, U15.9 (-), U15.13 (-)
unnamed: R2011.1, U15.8
unnamed: R2012.1, U15.14
unnamed: R2014.1, RV2001.2
unnamed: R2102.2, R2104.2, R2107.1, TR2101.1
unnamed: R2103.1, SW2101.2
unnamed: R2105.2, R2106.2, R2109.1, TR2101.5
unnamed: R2107.2, RV2101.2
unnamed: R2108.1, TR2102.4
unnamed: R2109.2, RV2102.2
unnamed: R2202.1, RV2201.2
unnamed: R2203.1, RV2202.2
unnamed: R2204.1, RV2203.2
unnamed: R2205.1, RV2204.2
unnamed: R2206.1, RV2205.2
unnamed: RV203.2, SW203.2
unnamed: RV204.3, SW201.2
unnamed: RV205.3, SW202.2
unnamed: RV303.3, U4.6 (hf_track)
unnamed: RV2201.3, SW2201.2 (B)
unnamed: RV2205.3, SW2202.2 (B)
unnamed: SW301.2, U4.13 (aux_2_mix)
unnamed: SW301.3, U4.9 (tri_mix)
unnamed: SW301.4, U4.10 (saw_mix)
unnamed: SW301.5, U4.11 (pulse_mix)
unnamed: U4.5 (aux_in_2), U4.24 (sine_out)
unnamed: U5.2 (~Q), U5.5 (D)
unnamed: U5.9 (D), U5.12 (~Q)
