JordanAceto/josh_Ox_ribbon_synth/circuit_boards/VCF_VCA_BBD_board/kicad_7/BBD_LPF.kicad_sch

## KiCad design circuit_boards/VCF_VCA_BBD_board/kicad_7/BBD_LPF.kicad_sch (2023-03-27)

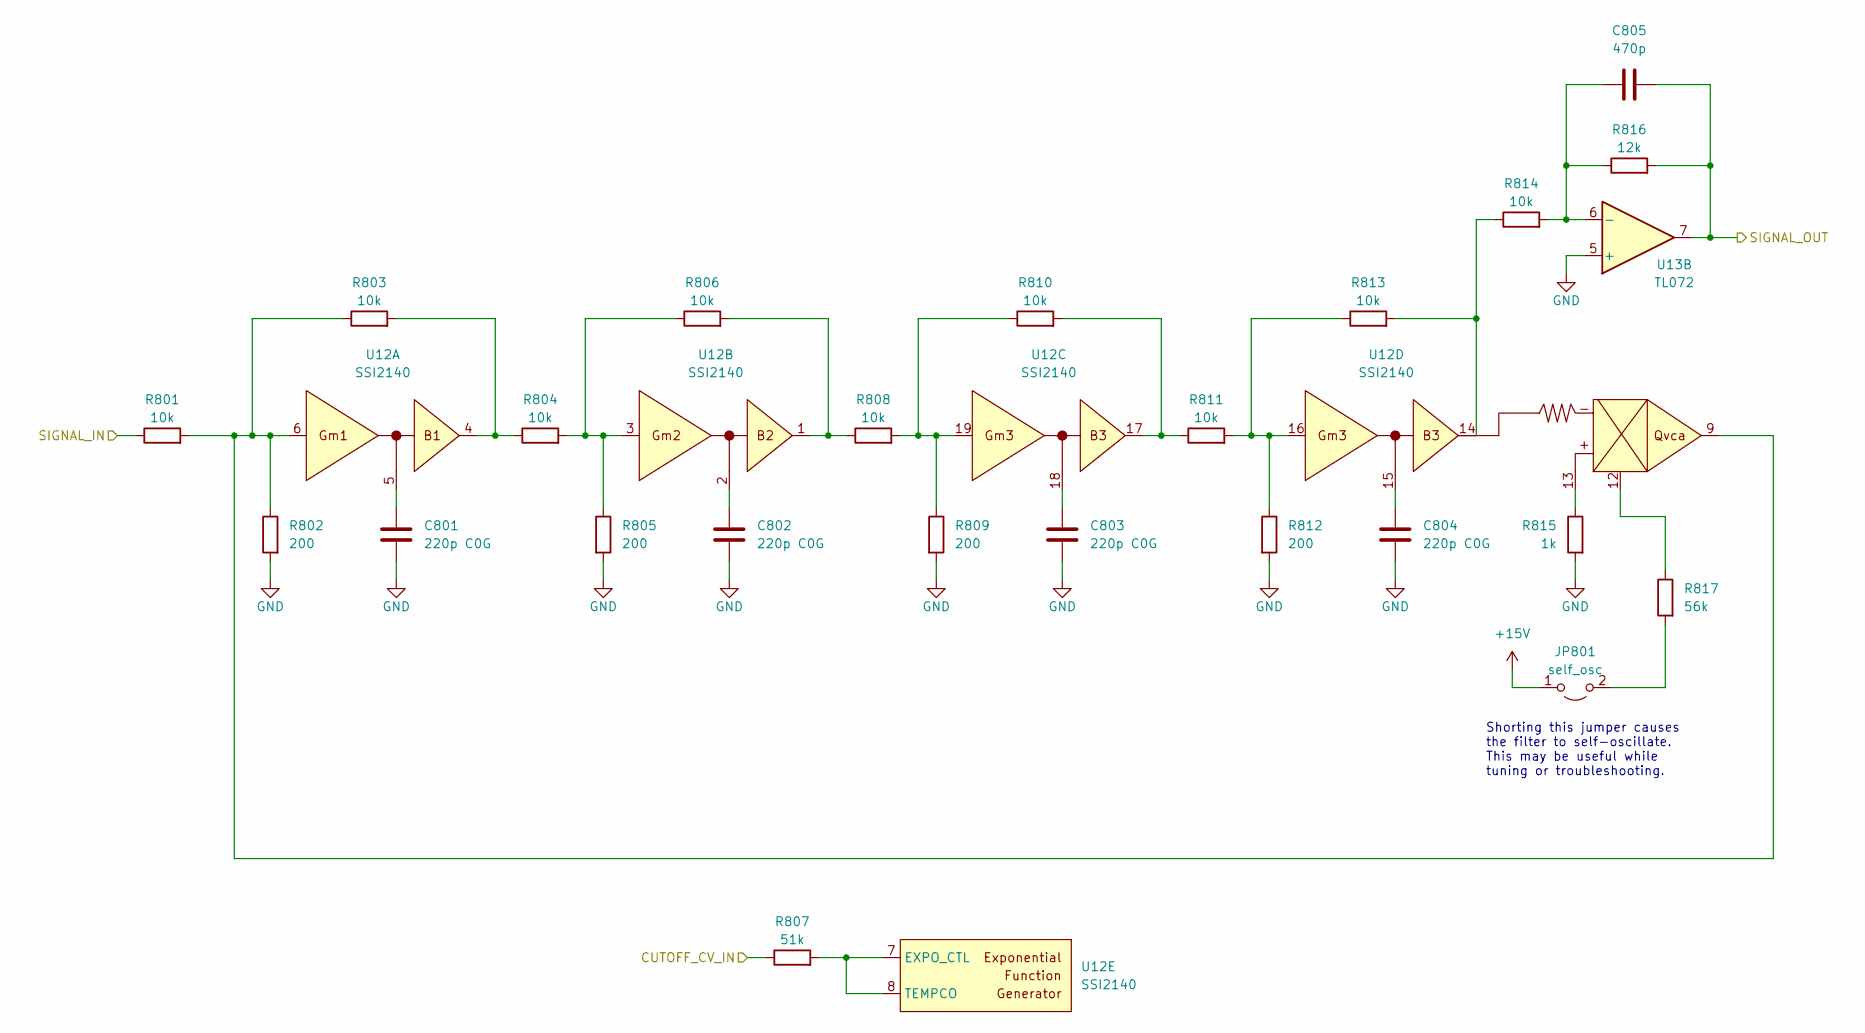
[picture p103: schematic BBD_LPF.kicad_sch]

Parts:
C801, C802, C803, C804: 220p C0G; C_0805_2012Metric
C805: 470p; C_0805_2012Metric
JP801: self_osc; PinHeader_1x02_P2.54mm_Vertical
R801, R803, R804, R806, R808, R810, R811, R813, R814: 10k; R_0805_2012Metric
R802, R805, R809, R812: 200; R_0805_2012Metric
R807: 51k; R_0805_2012Metric
R815: 1k; R_0805_2012Metric
R816: 12k; R_0805_2012Metric
R817: 56k; R_0805_2012Metric
U12: SSI2140; TSSOP-20_4.4x6.5mm_P0.65mm
U13: TL072; SOIC-8_3.9x4.9mm_P1.27mm

Connections:
+15V: JP801.1 (A)
CUTOFF_CV_IN: R807.1
GND: C801.2, C802.2, C803.2, C804.2, R802.2, R805.2, R809.2, R812.2, R815.2, U13.5 (+)
unnamed: C801.1, U12.5
unnamed: C802.1, U12.2
unnamed: C803.1, U12.18
unnamed: C804.1, U12.15
unnamed: C805.1, R814.2, R816.1, U13.6 (-)
unnamed: JP801.2 (B), R817.2
unnamed: R801.2, R802.1, R803.1, U12.6, U12.9
unnamed: R803.2, R804.1, U12.4
unnamed: R804.2, R805.1, R806.1, U12.3
unnamed: R806.2, R808.1, U12.1
unnamed: R807.2, U12.7 (EXPO_CTL), U12.8 (TEMPCO)
unnamed: R808.2, R809.1, R810.1, U12.19
unnamed: R810.2, R811.1, U12.17
unnamed: R811.2, R812.1, R813.1, U12.16
unnamed: R813.2, R814.1, U12.14
unnamed: R815.1, U12.13
unnamed: R817.1, U12.12
SIGNAL_IN: R801.1
SIGNAL_OUT: C805.2, R816.2, U13.7

Notes on the sheet:
Shorting this jumper causes the filter to self-oscillate. This may be useful while tuning or troubleshooting.
