JordanAceto/josh_Ox_ribbon_synth/circuit_boards/VCF_VCA_BBD_board/kicad_7/BBD_ctl_generators.kicad_sch

## KiCad design circuit_boards/VCF_VCA_BBD_board/kicad_7/BBD_ctl_generators.kicad_sch (2023-03-27)

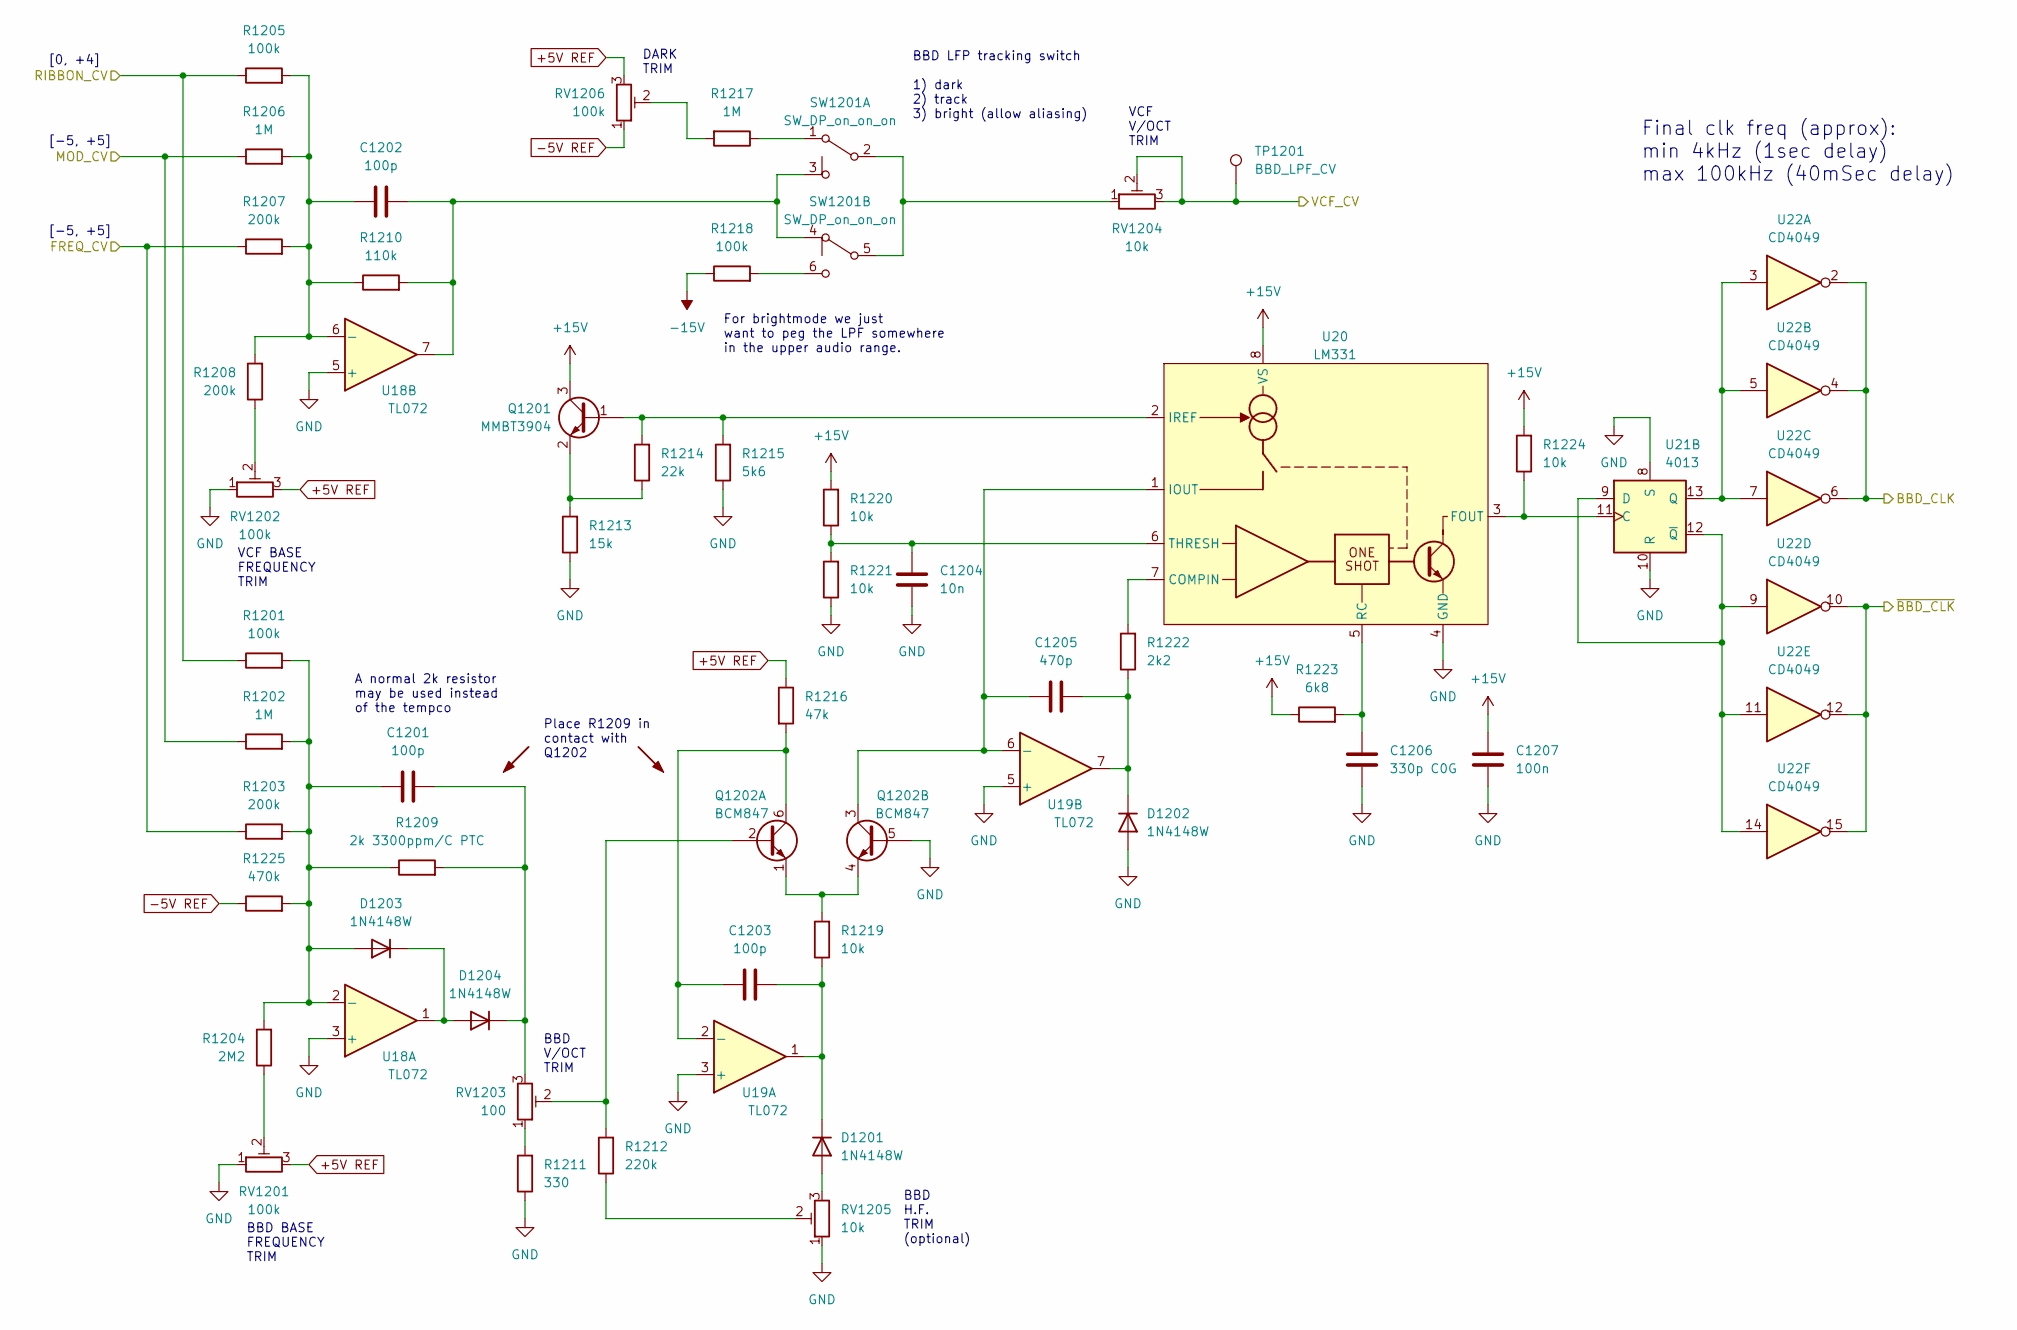
[picture p104: schematic BBD_ctl_generators.kicad_sch]

Parts:
C1201, C1202, C1203: 100p; C_0805_2012Metric
C1204: 10n; C_0805_2012Metric
C1205: 470p; C_0805_2012Metric
C1206: 330p C0G; C_0805_2012Metric
C1207: 100n; C_0805_2012Metric
D1201, D1202, D1203, D1204: 1N4148W; D_SOD-123
Q1201: MMBT3904; SOT-23
Q1202: BCM847; SOT457
R1201, R1205, R1218: 100k; R_0805_2012Metric
R1202, R1206, R1217: 1M; R_0805_2012Metric
R1203, R1207, R1208: 200k; R_0805_2012Metric
R1204: 2M2; R_0805_2012Metric
R1209: 2k 3300ppm/C PTC; R_Axial_DIN0207_L6.3mm_D2.5mm_P10.16mm_Horizontal
R1210: 110k; R_0805_2012Metric
R1211: 330; R_0805_2012Metric
R1212: 220k; R_0805_2012Metric
R1213: 15k; R_0805_2012Metric
R1214: 22k; R_0805_2012Metric
R1215: 5k6; R_0805_2012Metric
R1216: 47k; R_0805_2012Metric
R1219, R1220, R1221, R1224: 10k; R_0805_2012Metric
R1222: 2k2; R_0805_2012Metric
R1223: 6k8; R_0805_2012Metric
R1225: 470k; R_0805_2012Metric
RV1201, RV1202, RV1206: 100k; Potentiometer_Bourns_3296W_Vertical
RV1203: 100; Potentiometer_Bourns_3296W_Vertical
RV1204, RV1205: 10k; Potentiometer_Bourns_3296W_Vertical
SW1201: SW_DP_on_on_on; DPDT_mini_toggle
TP1201: BBD_LPF_CV; TestPoint_Keystone_5000-5004_Miniature
U18, U19: TL072; SOIC-8_3.9x4.9mm_P1.27mm
U20: LM331; DIP-8_W7.62mm_Socket
U21: 4013; SOIC-14_3.9x8.7mm_P1.27mm
U22: CD4049; TSSOP-16_4.4x5mm_P0.65mm

Connections:
+5V REF: R1216.1, RV1201.3, RV1202.3, RV1206.3
+15V: C1207.1, Q1201.3 (C), R1220.2, R1223.1, R1224.2, U20.8 (VS)
-5V REF: R1225.1, RV1206.1
-15V: R1218.1
BBD_CLK: U22.2, U22.4, U22.6
FREQ_CV: R1203.1, R1207.1
GND: C1204.2, C1206.2, C1207.2, D1202.2 (A), Q1202.5 (B), R1211.1, R1213.1, R1215.1, R1221.1, RV1201.1, RV1202.1, RV1205.1, U18.3 (+), U18.5 (+), U19.3 (+), U19.5 (+), U20.4 (GND), U21.8 (S), U21.10 (R)
MOD_CV: R1202.1, R1206.1
unnamed: C1201.1, D1203.2 (A), R1201.2, R1202.2, R1203.2, R1204.2, R1209.1, R1225.2, U18.2 (-)
unnamed: C1201.2, D1204.1 (K), R1209.2, RV1203.3
unnamed: C1202.1, R1205.2, R1206.2, R1207.2, R1208.2, R1210.1, U18.6 (-)
unnamed: C1202.2, R1210.2, SW1201.3 (C), SW1201.4 (A), U18.7
unnamed: C1203.1, Q1202.6 (C), R1216.2, U19.2 (-)
unnamed: C1203.2, D1201.1 (K), R1219.1, U19.1
unnamed: C1204.1, R1220.1, R1221.2, U20.6 (THRESH)
unnamed: C1205.1, Q1202.3 (C), U19.6 (-), U20.1 (IOUT)
unnamed: C1205.2, D1202.1 (K), R1222.1, U19.7
unnamed: C1206.1, R1223.2, U20.5 (RC)
unnamed: D1201.2 (A), RV1205.3
unnamed: D1203.1 (K), D1204.2 (A), U18.1
unnamed: Q1201.1 (B), R1214.2, R1215.2, U20.2 (IREF)
unnamed: Q1201.2 (E), R1213.2, R1214.1
unnamed: Q1202.1 (E), Q1202.4 (E), R1219.2
unnamed: Q1202.2 (B), R1212.2, RV1203.2
unnamed: R1204.1, RV1201.2
unnamed: R1208.1, RV1202.2
unnamed: R1211.2, RV1203.1
unnamed: R1212.1, RV1205.2
unnamed: R1217.1, SW1201.1 (A)
unnamed: R1217.2, RV1206.2
unnamed: R1218.2, SW1201.6 (C)
unnamed: R1222.2, U20.7 (COMPIN)
unnamed: R1224.1, U20.3 (FOUT), U21.11 (C)
unnamed: RV1204.1, SW1201.2 (B), SW1201.5 (B)
unnamed: U21.9 (D), U21.12 (~Q), U22.9, U22.11, U22.14
unnamed: U21.13 (Q), U22.3, U22.5, U22.7
RIBBON_CV: R1201.1, R1205.1
VCF_CV: RV1204.2, RV1204.3, TP1201.1
~BBD_CLK: U22.10, U22.12, U22.15

Notes on the sheet:
BBD BASE FREQUENCY TRIM
DARK TRIM
VCF V/OCT TRIM
Place R1209 in contact with Q1202
For brightmode we just want to peg the LPF somewhere in the upper audio range.
A normal 2k resistor may be used instead of the tempco
Final clk freq (approx): min 4kHz (1sec delay) max 100kHz (40mSec delay)
[-5, +5]
BBD V/OCT TRIM
BBD H.F. TRIM (optional)
[0, +4]
VCF BASE FREQUENCY TRIM
BBD LFP tracking switch 1) dark 2) track 3) bright (allow aliasing)
