JordanAceto/josh_Ox_ribbon_synth/circuit_boards/VCF_VCA_BBD_board/kicad_7/BBD_stages.kicad_sch

## KiCad design circuit_boards/VCF_VCA_BBD_board/kicad_7/BBD_stages.kicad_sch (2023-03-27)

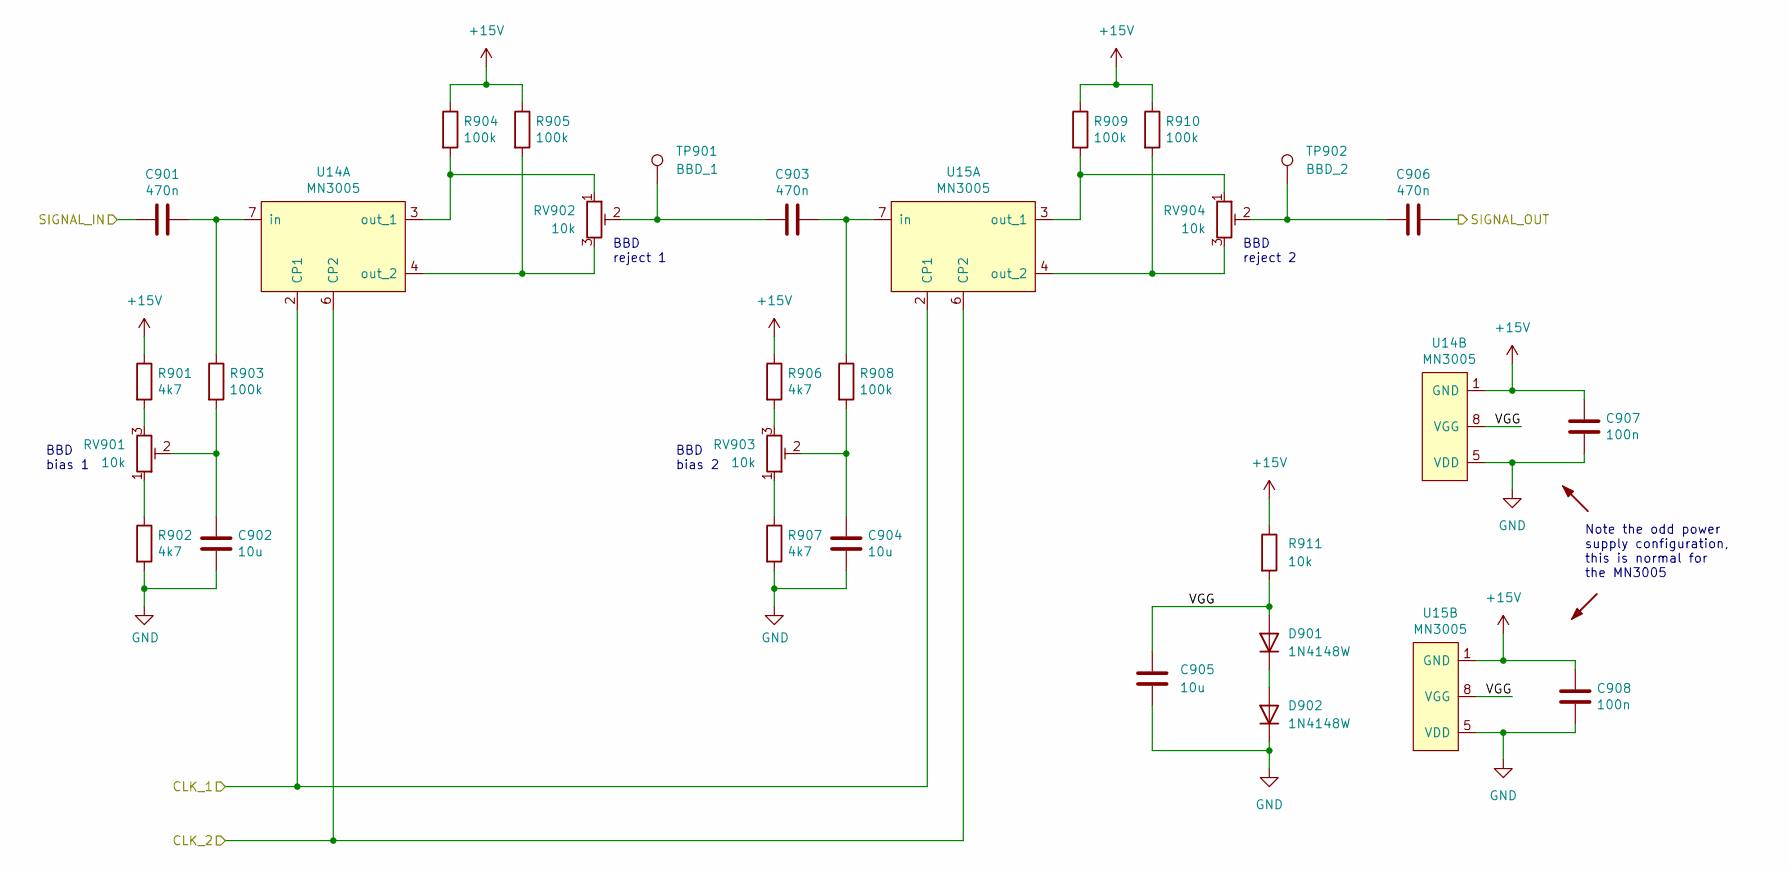
[picture p105: schematic BBD_stages.kicad_sch]

Parts:
C901, C903, C906: 470n; C_Rect_L7.0mm_W3.5mm_P5.00mm
C902, C904, C905: 10u; C_0805_2012Metric
C907, C908: 100n; C_0805_2012Metric
D901, D902: 1N4148W; D_SOD-123
R901, R902, R906, R907: 4k7; R_0805_2012Metric
R903, R904, R905, R908, R909, R910: 100k; R_0805_2012Metric
R911: 10k; R_0805_2012Metric
RV901, RV902, RV903, RV904: 10k; Potentiometer_Bourns_3296W_Vertical
TP901: BBD_1; TestPoint_Keystone_5000-5004_Miniature
TP902: BBD_2; TestPoint_Keystone_5000-5004_Miniature
U14, U15: MN3005; DIP-8-14_W7.62mm_Socket

Connections:
+15V: C907.1, C908.1, R901.1, R904.1, R905.1, R906.1, R909.1, R910.1, R911.1, U14.1 (GND), U15.1 (GND)
CLK_1: U14.2 (CP1), U15.2 (CP1)
CLK_2: U14.6 (CP2), U15.6 (CP2)
GND: C902.2, C904.2, C905.2, C907.2, C908.2, D902.1 (K), R902.2, R907.2, U14.5 (VDD), U15.5 (VDD)
unnamed: C901.1, R903.1, U14.7 (in)
unnamed: C902.1, R903.2, RV901.2
unnamed: C903.1, R908.1, U15.7 (in)
unnamed: C903.2, RV902.2, TP901.1
unnamed: C904.1, R908.2, RV903.2
unnamed: C906.2, RV904.2, TP902.1
unnamed: D901.1 (K), D902.2 (A)
unnamed: R901.2, RV901.3
unnamed: R902.1, RV901.1
unnamed: R904.2, RV902.1, U14.3 (out_1)
unnamed: R905.2, RV902.3, U14.4 (out_2)
unnamed: R906.2, RV903.3
unnamed: R907.1, RV903.1
unnamed: R909.2, RV904.1, U15.3 (out_1)
unnamed: R910.2, RV904.3, U15.4 (out_2)
SIGNAL_IN: C901.2
SIGNAL_OUT: C906.1
VGG: C905.1, D901.2 (A), R911.2, U14.8 (VGG), U15.8 (VGG)

Notes on the sheet:
BBD reject 1
BBD bias 2
BBD bias 1
Note the odd power supply configuration, this is normal for the MN3005
BBD reject 2
