JordanAceto/josh_Ox_ribbon_synth/circuit_boards/VCF_VCA_BBD_board/kicad_7/CV_mixer.kicad_sch

## KiCad design circuit_boards/VCF_VCA_BBD_board/kicad_7/CV_mixer.kicad_sch (2023-03-27)

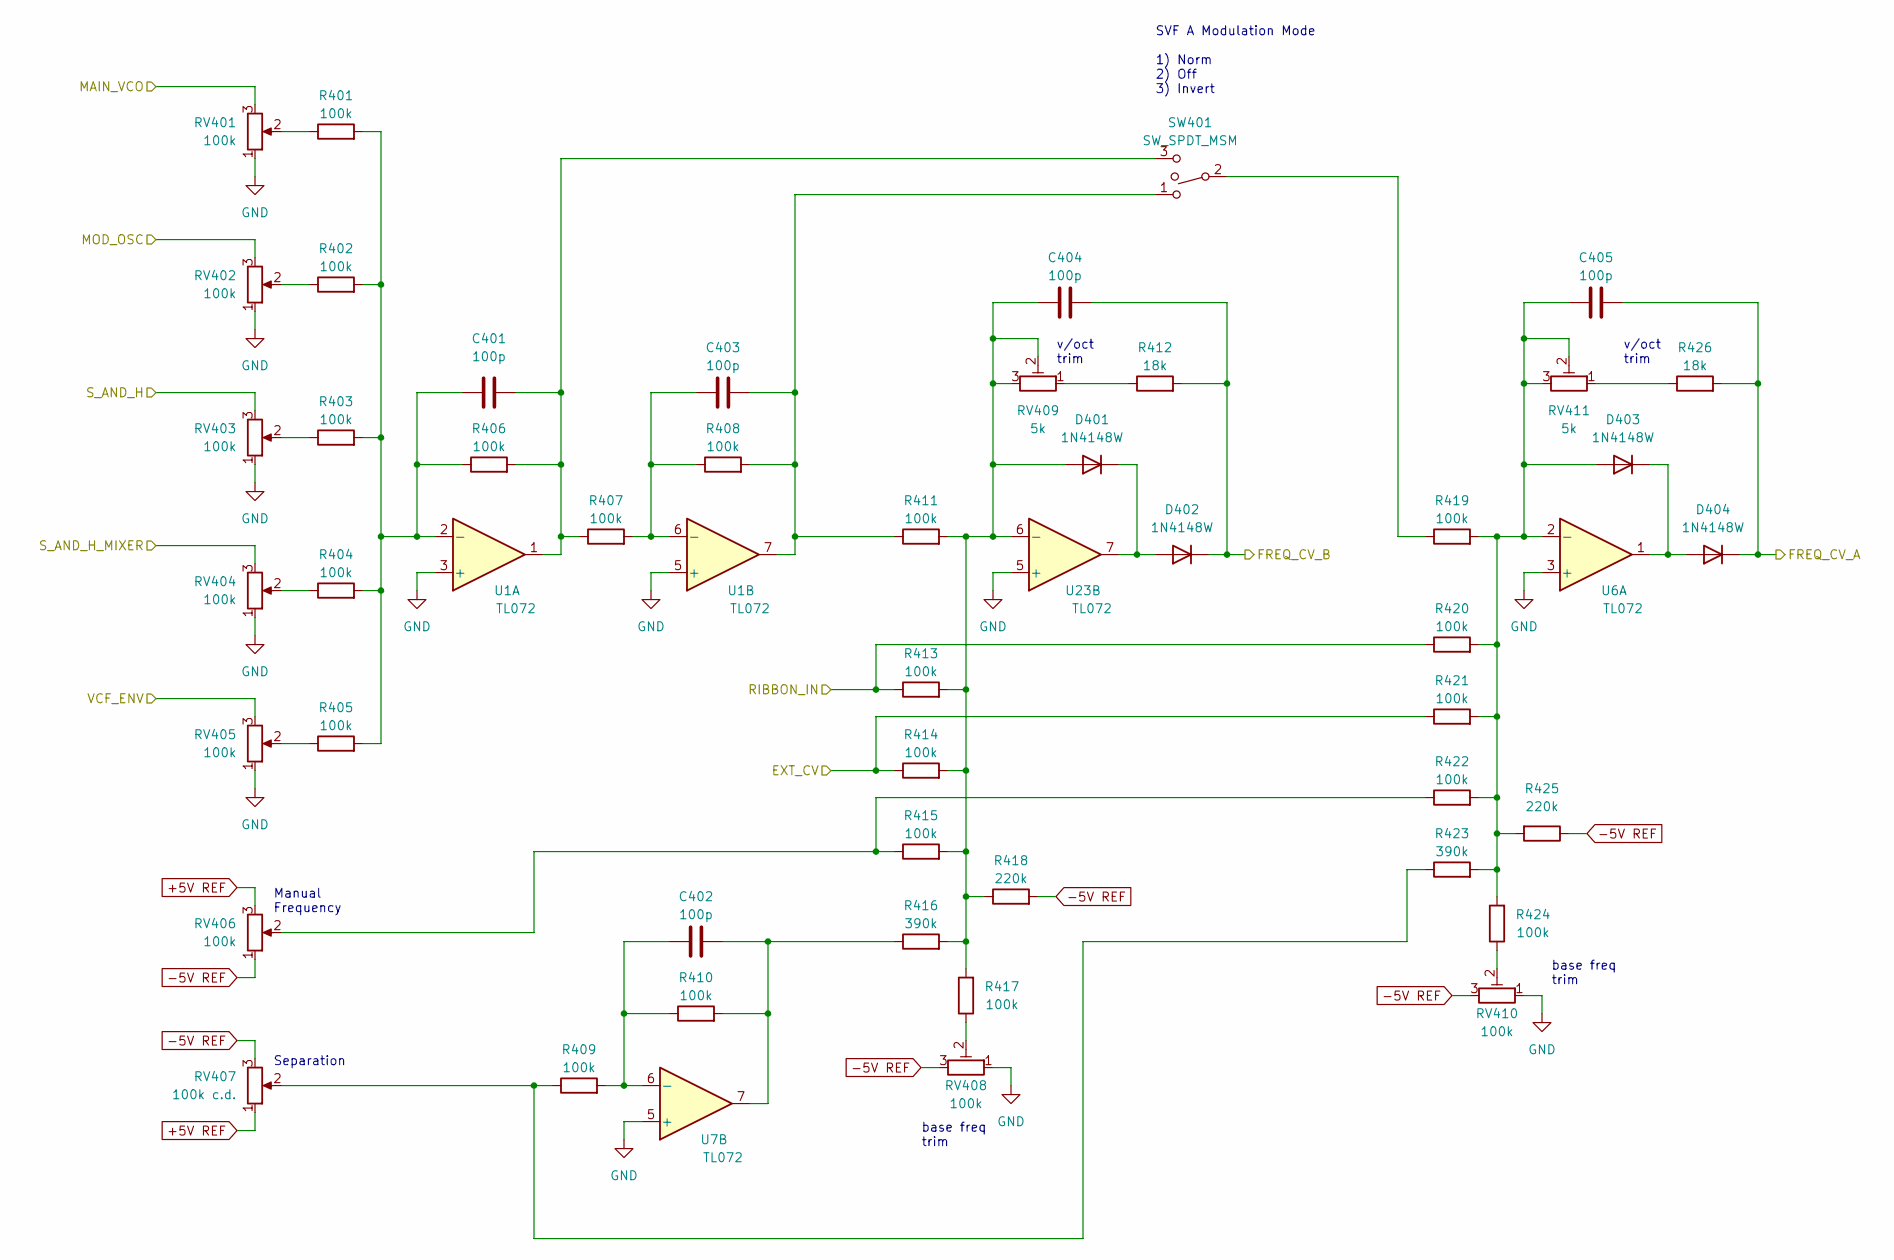
[picture p106: schematic CV_mixer.kicad_sch]

Parts:
C401, C402, C403, C404, C405: 100p; C_0805_2012Metric
D401, D402, D403, D404: 1N4148W; D_SOD-123
R401, R402, R403, R404, R405, R406, R407, R408, R409, R410, R411, R413, R414, R415, R417, R419, R420, R421, R422, R424: 100k; R_0805_2012Metric
R412, R426: 18k; R_0805_2012Metric
R416, R423: 390k; R_0805_2012Metric
R418, R425: 220k; R_0805_2012Metric
RV401, RV402, RV403, RV404, RV405, RV406: 100k; Potentiometer_Alpha_RD901F-40-00D_Single_Vertical
RV407: 100k c.d.; Potentiometer_Alpha_RD901F-40-00D_Single_Vertical
RV408, RV410: 100k; Potentiometer_Bourns_3296W_Vertical
RV409, RV411: 5k; Potentiometer_Bourns_3296W_Vertical
SW401: SW_SPDT_MSM; SPDT_mini_toggle
U1, U6, U7, U23: TL072; SOIC-8_3.9x4.9mm_P1.27mm

Connections:
+5V REF: RV406.3, RV407.1
-5V REF: R418.2, R425.1, RV406.1, RV407.3, RV408.3, RV410.3
EXT_CV: R414.1, R421.1
FREQ_CV_A: C405.2, D404.1 (K), R426.2
FREQ_CV_B: C404.2, D402.1 (K), R412.2
GND: RV401.1, RV402.1, RV403.1, RV404.1, RV405.1, RV408.1, RV410.1, U1.3 (+), U1.5 (+), U6.3 (+), U7.5 (+), U23.5 (+)
MAIN_VCO: RV401.3
MOD_OSC: RV402.3
unnamed: C401.1, R401.2, R402.2, R403.2, R404.2, R405.2, R406.1, U1.2 (-)
unnamed: C401.2, R406.2, R407.1, SW401.3, U1.1
unnamed: C402.1, R409.2, R410.1, U7.6 (-)
unnamed: C402.2, R410.2, R416.1, U7.7
unnamed: C403.1, R407.2, R408.1, U1.6 (-)
unnamed: C403.2, R408.2, R411.1, SW401.1, U1.7
unnamed: C404.1, D401.2 (A), R411.2, R413.2, R414.2, R415.2, R416.2, R417.2, R418.1, RV409.2, RV409.3, U23.6 (-)
unnamed: C405.1, D403.2 (A), R419.2, R420.2, R421.2, R422.2, R423.2, R424.2, R425.2, RV411.2, RV411.3, U6.2 (-)
unnamed: D401.1 (K), D402.2 (A), U23.7
unnamed: D403.1 (K), D404.2 (A), U6.1
unnamed: R401.1, RV401.2
unnamed: R402.1, RV402.2
unnamed: R403.1, RV403.2
unnamed: R404.1, RV404.2
unnamed: R405.1, RV405.2
unnamed: R409.1, R423.1, RV407.2
unnamed: R412.1, RV409.1
unnamed: R415.1, R422.1, RV406.2
unnamed: R417.1, RV408.2
unnamed: R419.1, SW401.2
unnamed: R424.1, RV410.2
unnamed: R426.1, RV411.1
RIBBON_IN: R413.1, R420.1
S_AND_H: RV403.3
S_AND_H_MIXER: RV404.3
VCF_ENV: RV405.3

Notes on the sheet:
Manual Frequency
SVF A Modulation Mode 1) Norm 2) Off 3) Invert
Separation
base freq trim
v/oct trim
