JordanAceto/josh_Ox_ribbon_synth/circuit_boards/VCF_VCA_BBD_board/kicad_7/SVF.kicad_sch

## KiCad design circuit_boards/VCF_VCA_BBD_board/kicad_7/SVF.kicad_sch (2023-03-27)

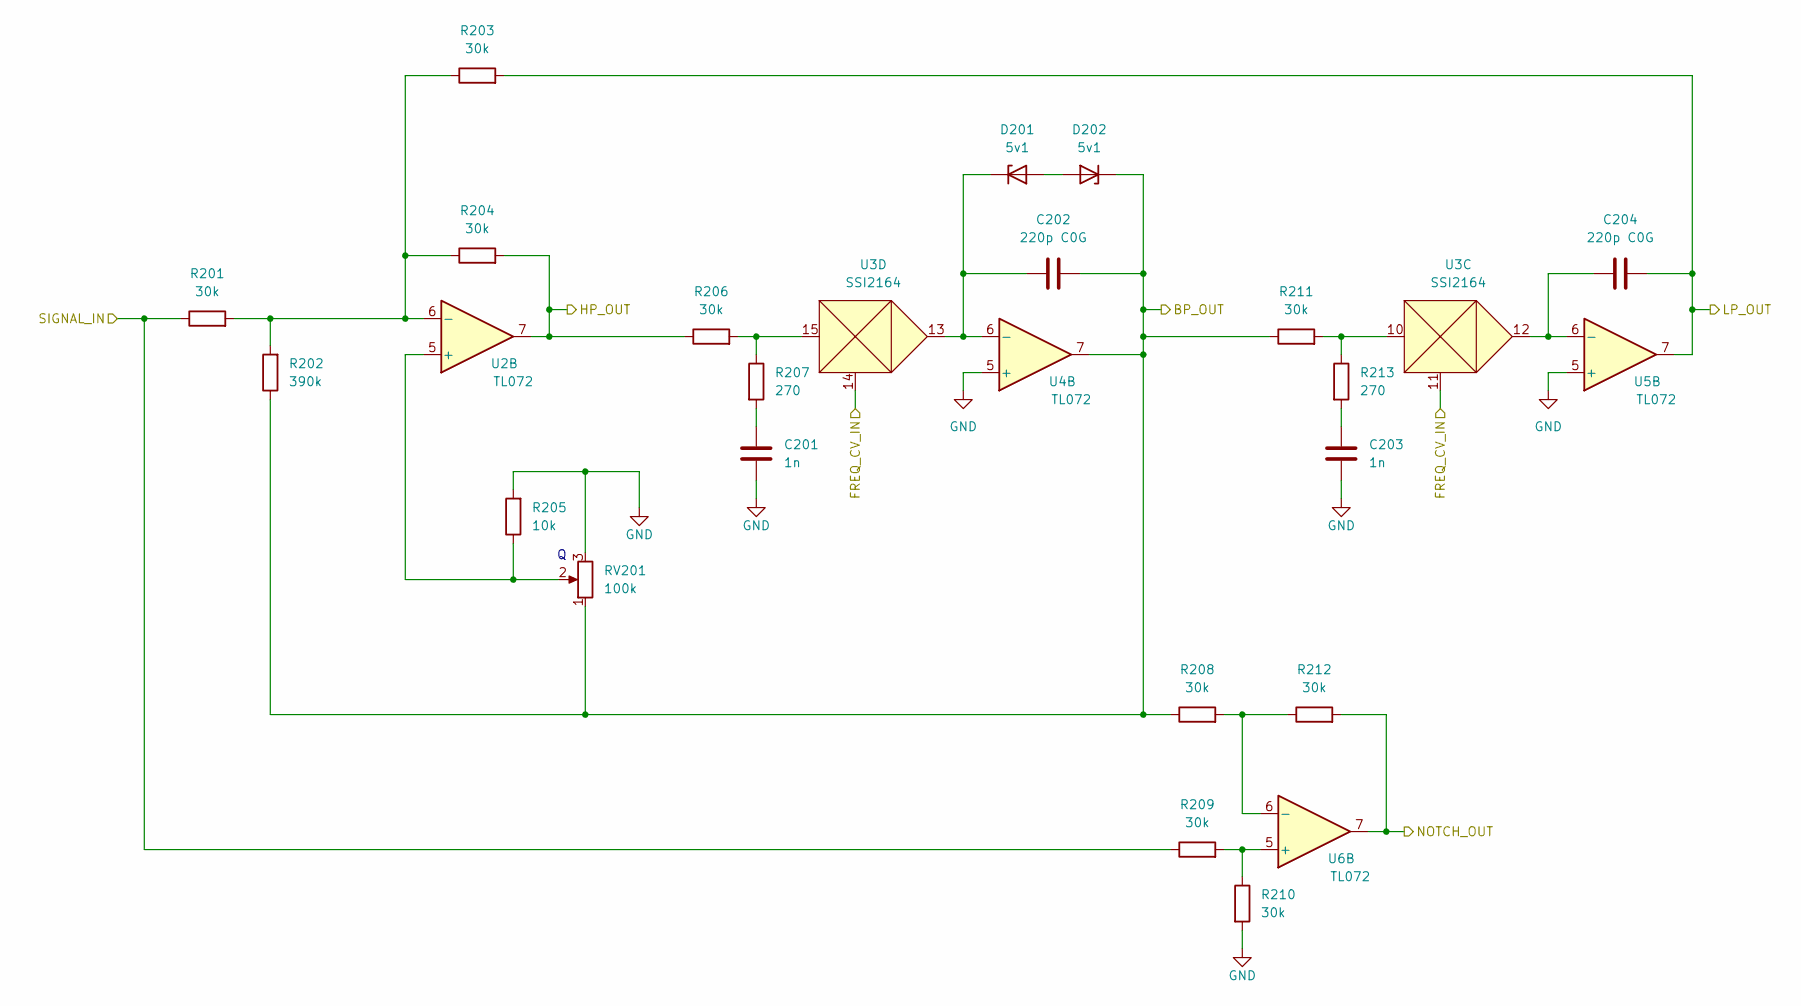
[picture p107: schematic SVF.kicad_sch]

Parts:
C201, C203: 1n; C_0805_2012Metric
C202, C204: 220p C0G; C_0805_2012Metric
D201, D202: 5v1; D_SOD-123
R201, R203, R204, R206, R208, R209, R210, R211, R212: 30k; R_0805_2012Metric
R202: 390k; R_0805_2012Metric
R205: 10k; R_0805_2012Metric
R207, R213: 270; R_0805_2012Metric
RV201: 100k; Potentiometer_Alpha_RD901F-40-00D_Single_Vertical
U2, U4, U5, U6: TL072; SOIC-8_3.9x4.9mm_P1.27mm
U3: SSI2164; SOIC-16_3.9x9.9mm_P1.27mm

Connections:
BP_OUT: C202.2, D202.1 (K), R202.1, R208.1, R211.1, RV201.1, U4.7
FREQ_CV_IN: U3.11, U3.14
GND: C201.2, C203.2, R205.2, R210.2, RV201.3, U4.5 (+), U5.5 (+)
HP_OUT: R204.2, R206.1, U2.7
LP_OUT: C204.2, R203.2, U5.7
NOTCH_OUT: R212.2, U6.7
unnamed: C201.1, R207.2
unnamed: C202.1, D201.1 (K), U3.13, U4.6 (-)
unnamed: C203.1, R213.2
unnamed: C204.1, U3.12, U5.6 (-)
unnamed: D201.2 (A), D202.2 (A)
unnamed: R201.2, R202.2, R203.1, R204.1, U2.6 (-)
unnamed: R205.1, RV201.2, U2.5 (+)
unnamed: R206.2, R207.1, U3.15
unnamed: R208.2, R212.1, U6.6 (-)
unnamed: R209.2, R210.1, U6.5 (+)
unnamed: R211.2, R213.1, U3.10
SIGNAL_IN: R201.1, R209.1
