JordanAceto/josh_Ox_ribbon_synth/circuit_boards/VCF_VCA_BBD_board/kicad_7/VCA.kicad_sch

## KiCad design circuit_boards/VCF_VCA_BBD_board/kicad_7/VCA.kicad_sch (2023-03-27)

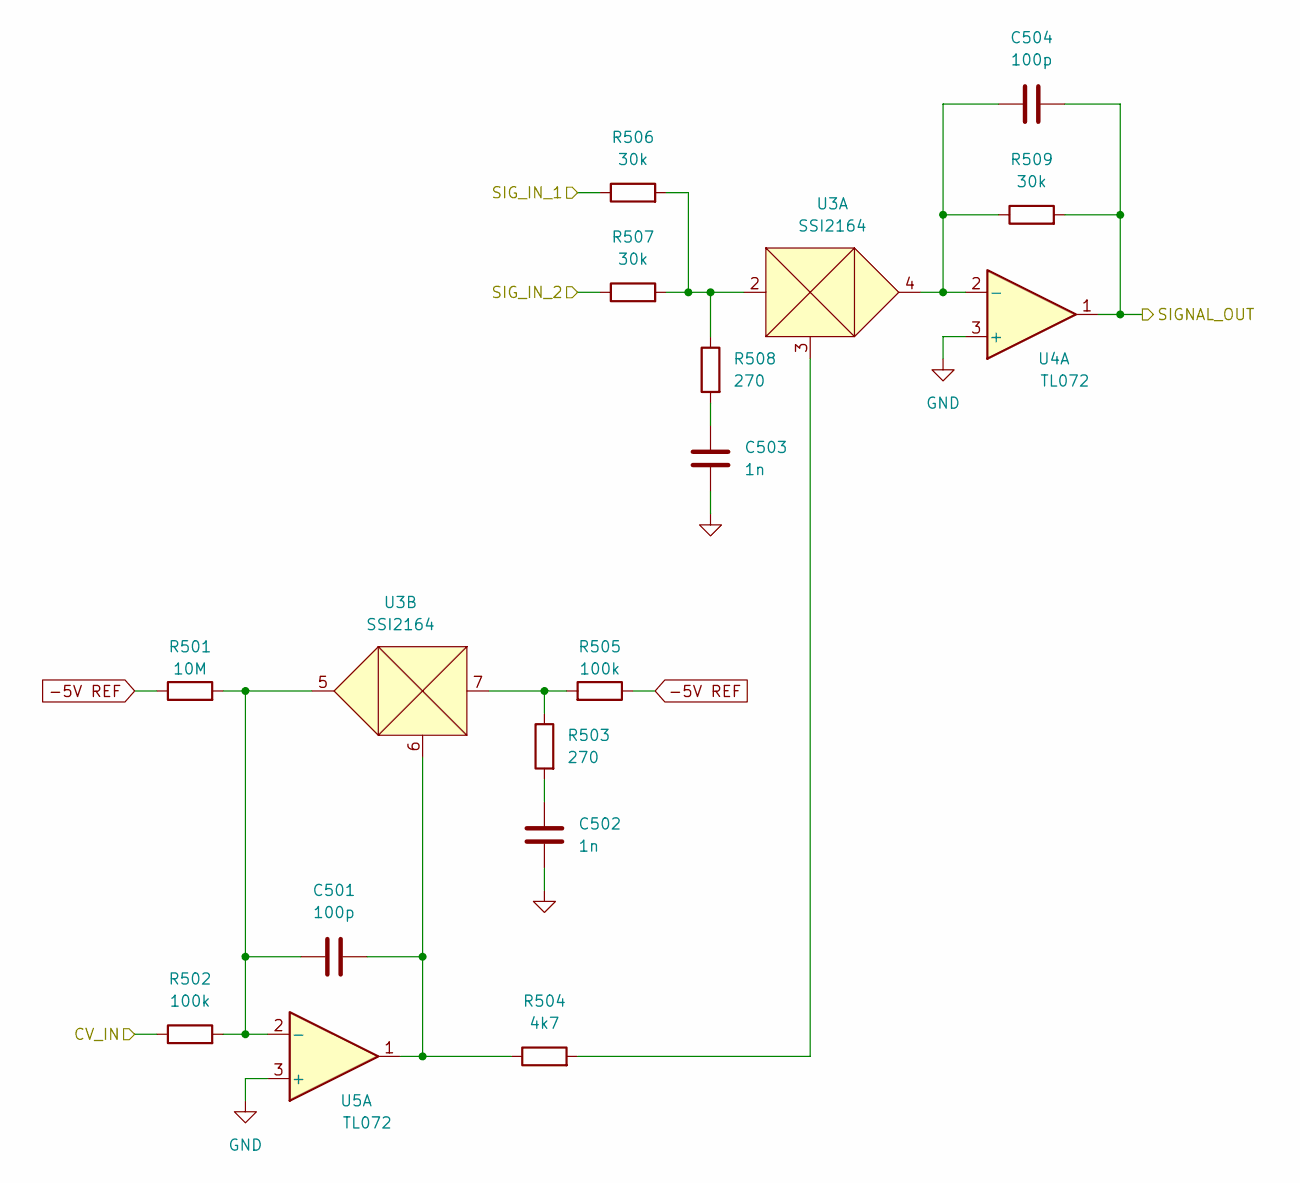
[picture p108: schematic VCA.kicad_sch]

Parts:
C501, C504: 100p; C_0805_2012Metric
C502, C503: 1n; C_0805_2012Metric
R501: 10M; R_0805_2012Metric
R502, R505: 100k; R_0805_2012Metric
R503, R508: 270; R_0805_2012Metric
R504: 4k7; R_0805_2012Metric
R506, R507, R509: 30k; R_0805_2012Metric
U3: SSI2164; SOIC-16_3.9x9.9mm_P1.27mm
U4, U5: TL072; SOIC-8_3.9x4.9mm_P1.27mm

Connections:
-5V REF: R501.1, R505.1
CV_IN: R502.1
GND: U4.3 (+), U5.3 (+)
unnamed: C501.1, R501.2, R502.2, U3.5, U5.2 (-)
unnamed: C501.2, R504.1, U3.6, U5.1
unnamed: C502.1, R503.2
unnamed: C503.1, R508.2
unnamed: C504.1, R509.1, U3.4, U4.2 (-)
unnamed: R503.1, R505.2, U3.7
unnamed: R504.2, U3.3
unnamed: R506.2, R507.2, R508.1, U3.2
SIGNAL_OUT: C504.2, R509.2, U4.1
SIG_IN_1: R506.1
SIG_IN_2: R507.1
~: C502.2, C503.2
