JordanAceto/josh_Ox_ribbon_synth/circuit_boards/VCF_VCA_BBD_board/kicad_7/VCF_VCA_BBD_board.kicad_sch

## KiCad design circuit_boards/VCF_VCA_BBD_board/kicad_7/VCF_VCA_BBD_board.kicad_sch (2023-03-27)

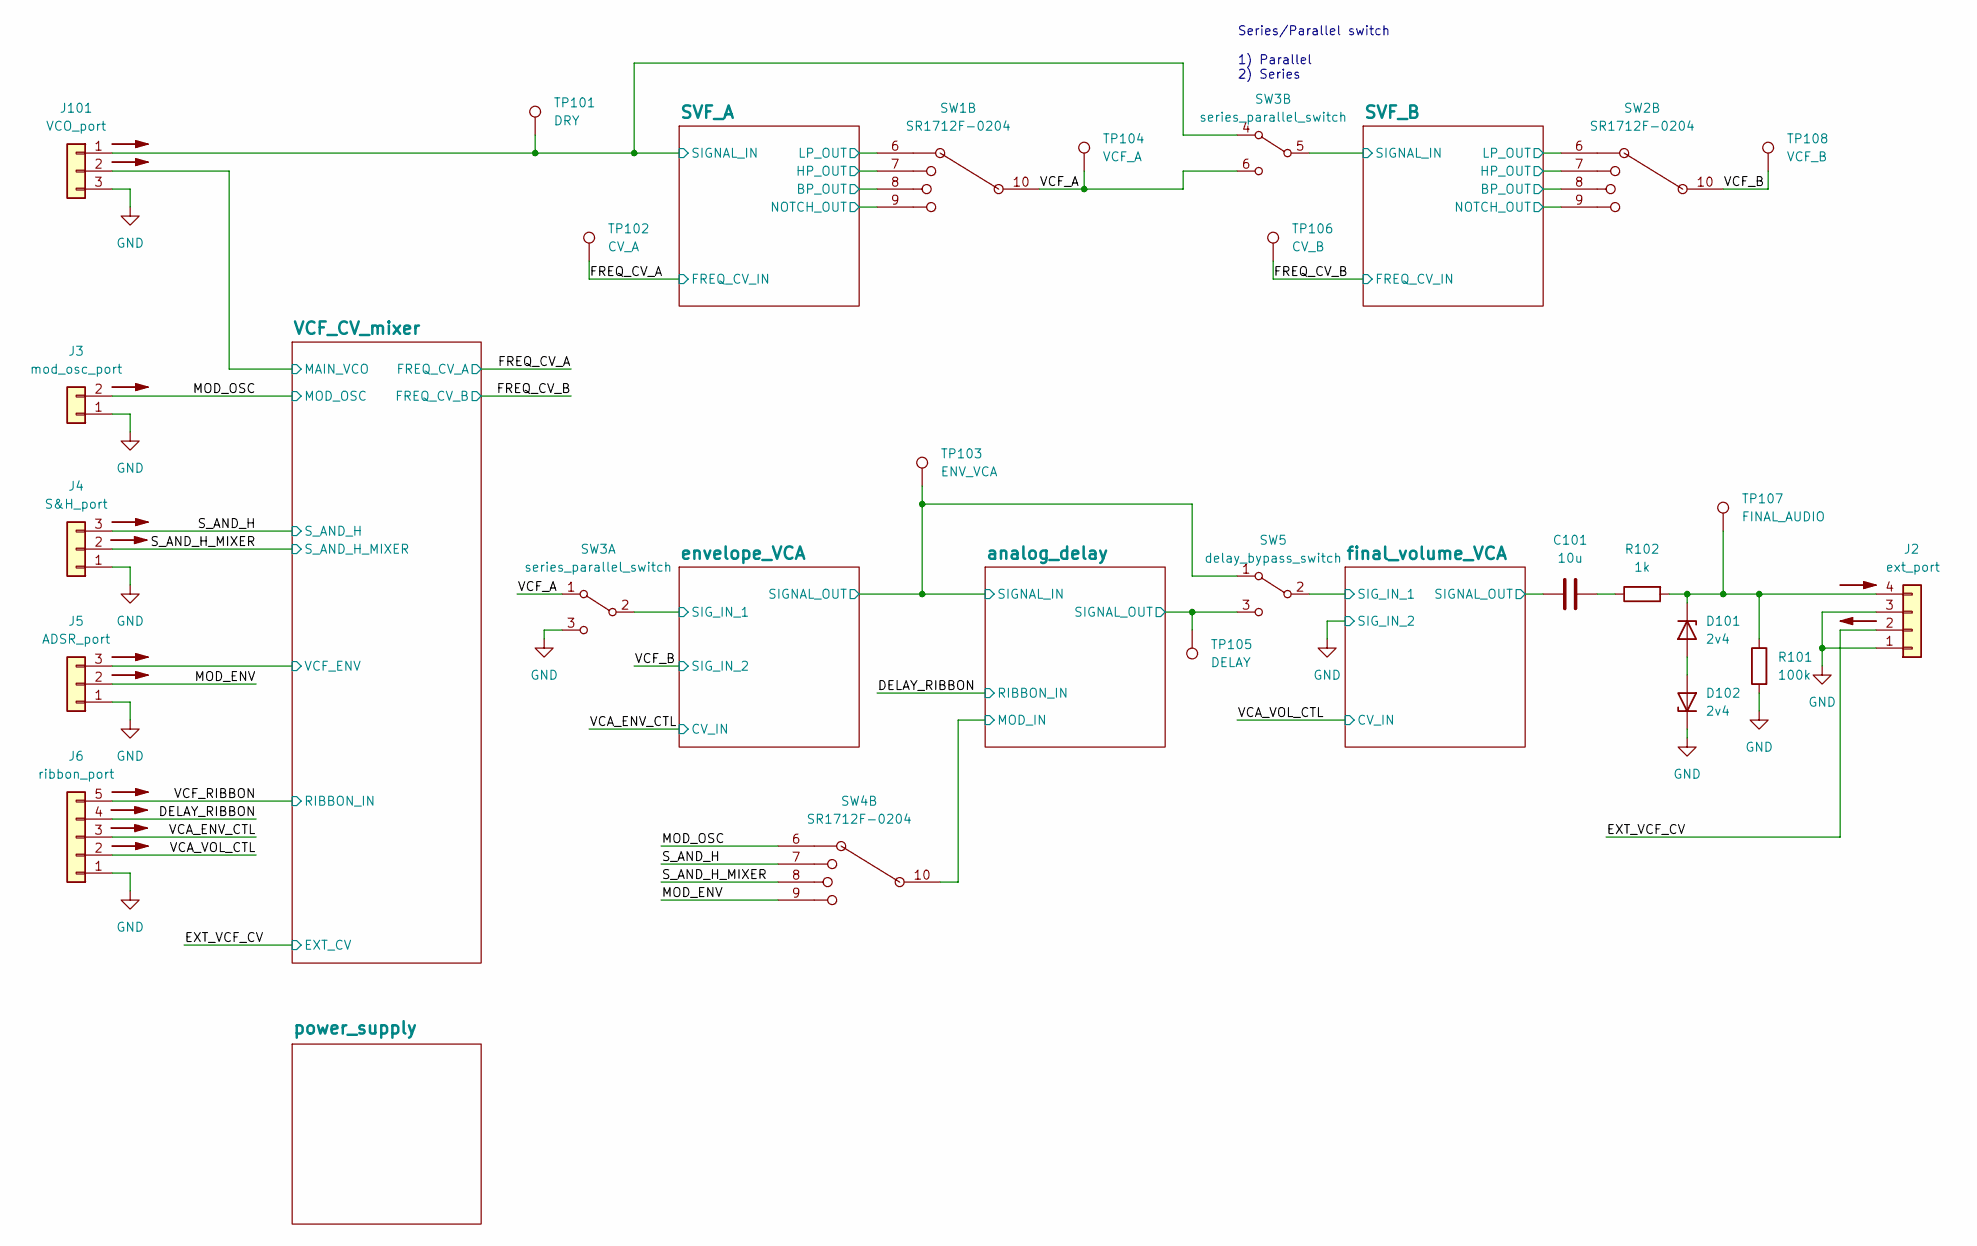
[picture p109: schematic VCF_VCA_BBD_board.kicad_sch]

Parts:
C101: 10u; C_Radial_D6.3mm_H7.0mm_P2.50mm
D101, D102: 2v4; D_SOD-123
J2: ext_port; Molex_KK-254_AE-6410-04A_1x04_P2.54mm_Vertical
J3: mod_osc_port; Molex_KK-254_AE-6410-02A_1x02_P2.54mm_Vertical
J4: S&H_port; Molex_KK-254_AE-6410-03A_1x03_P2.54mm_Vertical
J5: ADSR_port; Molex_KK-254_AE-6410-03A_1x03_P2.54mm_Vertical
J6: ribbon_port; Molex_KK-254_AE-6410-05A_1x05_P2.54mm_Vertical
J101: VCO_port; Molex_KK-254_AE-6410-03A_1x03_P2.54mm_Vertical
R101: 100k; R_0805_2012Metric
R102: 1k; R_0805_2012Metric
SW1, SW2, SW4: SR1712F-0204; SR1712F_rotary_switch
SW3: series_parallel_switch; DPDT_mini_toggle
SW5: delay_bypass_switch; SPDT_mini_toggle
TP101: DRY; TestPoint_Keystone_5000-5004_Miniature
TP102: CV_A; TestPoint_Keystone_5000-5004_Miniature
TP103: ENV_VCA; TestPoint_Keystone_5000-5004_Miniature
TP104: VCF_A; TestPoint_Keystone_5000-5004_Miniature
TP105: DELAY; TestPoint_Keystone_5000-5004_Miniature
TP106: CV_B; TestPoint_Keystone_5000-5004_Miniature
TP107: FINAL_AUDIO; TestPoint_Keystone_5000-5004_Miniature
TP108: VCF_B; TestPoint_Keystone_5000-5004_Miniature

Connections:
BP_OUT: SW1.8, SW2.8
DELAY_RIBBON: J6.4
EXT_VCF_CV: J2.2
FREQ_CV_A: TP102.1
FREQ_CV_B: TP106.1
GND: D102.1 (K), J2.1, J2.3, J3.1, J4.1, J5.1, J6.1, J101.3, R101.2, SW3.3 (C)
HP_OUT: SW1.7, SW2.7
LP_OUT: SW1.6, SW2.6
MAIN_VCO: J101.2
MOD_ENV: J5.2, SW4.9
MOD_IN: SW4.10
MOD_OSC: J3.2, SW4.6
NOTCH_OUT: SW1.9, SW2.9
unnamed: C101.2, R102.1
unnamed: D101.1 (K), J2.4, R101.1, R102.2, TP107.1
unnamed: D101.2 (A), D102.2 (A)
SIGNAL_IN: J101.1, SW3.4 (A), SW3.5 (B), TP101.1
SIGNAL_OUT: C101.1, SW5.1 (A), SW5.3 (C), TP103.1, TP105.1
SIG_IN_1: SW3.2 (B), SW5.2 (B)
S_AND_H: J4.3, SW4.7
S_AND_H_MIXER: J4.2, SW4.8
VCA_ENV_CTL: J6.3
VCA_VOL_CTL: J6.2
VCF_A: SW1.10, SW3.1 (A), SW3.6 (C), TP104.1
VCF_B: SW2.10, TP108.1
VCF_ENV: J5.3
VCF_RIBBON: J6.5

Notes on the sheet:
Series/Parallel switch 1) Parallel 2) Series
