JordanAceto/josh_Ox_ribbon_synth/circuit_boards/VCF_VCA_BBD_board/kicad_7/analog_delay.kicad_sch

## KiCad design circuit_boards/VCF_VCA_BBD_board/kicad_7/analog_delay.kicad_sch (2023-03-27)

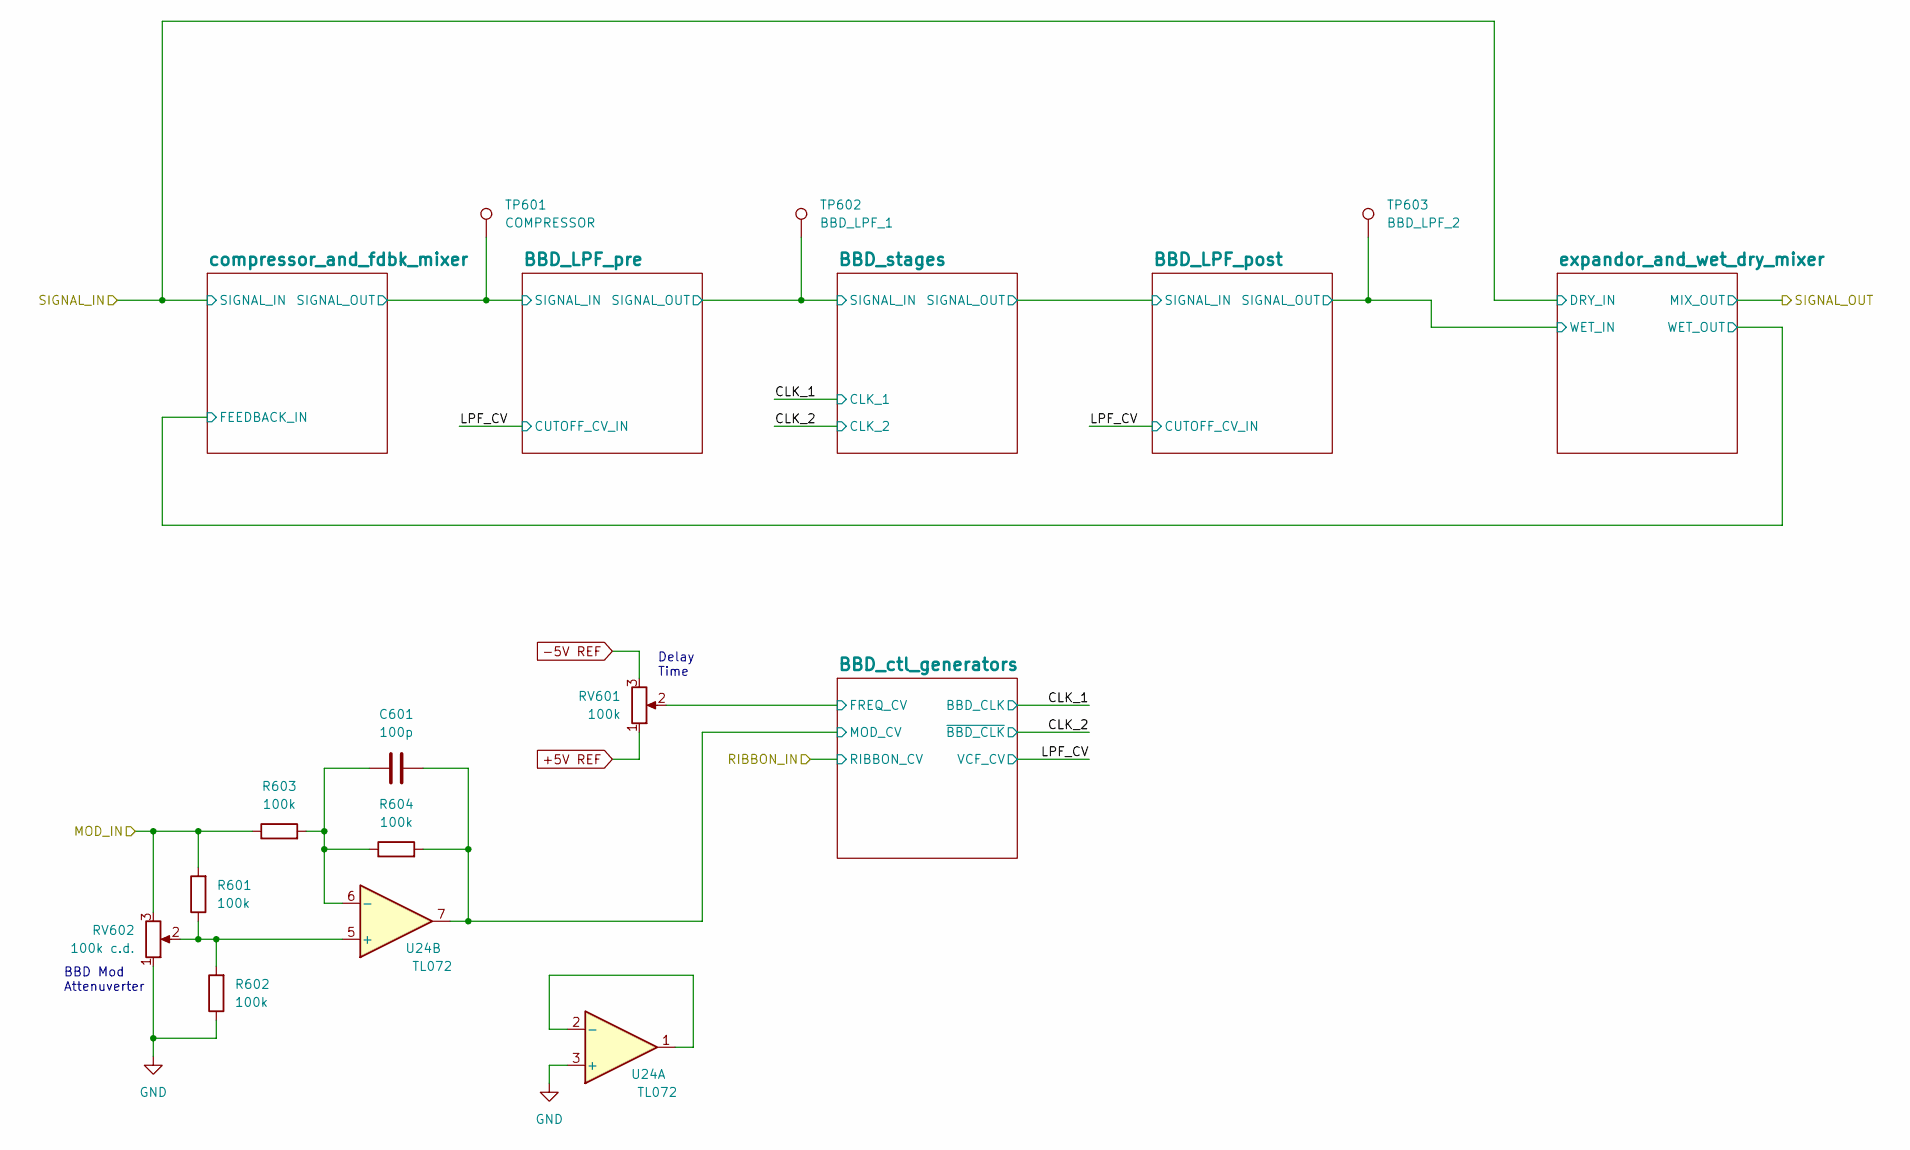
[picture p110: schematic analog_delay.kicad_sch]

Parts:
C601: 100p; C_0805_2012Metric
R601, R602, R603, R604: 100k; R_0805_2012Metric
RV601: 100k; Potentiometer_Alpha_RD901F-40-00D_Single_Vertical
RV602: 100k c.d.; Potentiometer_Alpha_RD901F-40-00D_Single_Vertical
TP601: COMPRESSOR; TestPoint_Keystone_5000-5004_Miniature
TP602: BBD_LPF_1; TestPoint_Keystone_5000-5004_Miniature
TP603: BBD_LPF_2; TestPoint_Keystone_5000-5004_Miniature
U24: TL072; SOIC-8_3.9x4.9mm_P1.27mm

Connections:
+5V REF: RV601.1
-5V REF: RV601.3
FREQ_CV: RV601.2
GND: R602.1, RV602.1, U24.3 (+)
MOD_CV: C601.2, R604.2, U24.7
MOD_IN: R601.2, R603.1, RV602.3
unnamed: C601.1, R603.2, R604.1, U24.6 (-)
unnamed: R601.1, R602.2, RV602.2, U24.5 (+)
unnamed: U24.1, U24.2 (-)
SIGNAL_IN: TP601.1
SIGNAL_OUT: TP602.1, TP603.1

Notes on the sheet:
Delay Time
BBD Mod Attenuverter
