JordanAceto/josh_Ox_ribbon_synth/circuit_boards/VCF_VCA_BBD_board/kicad_7/compressor_and_fdbk_mixer.kicad_sch

## KiCad design circuit_boards/VCF_VCA_BBD_board/kicad_7/compressor_and_fdbk_mixer.kicad_sch (2023-03-27)

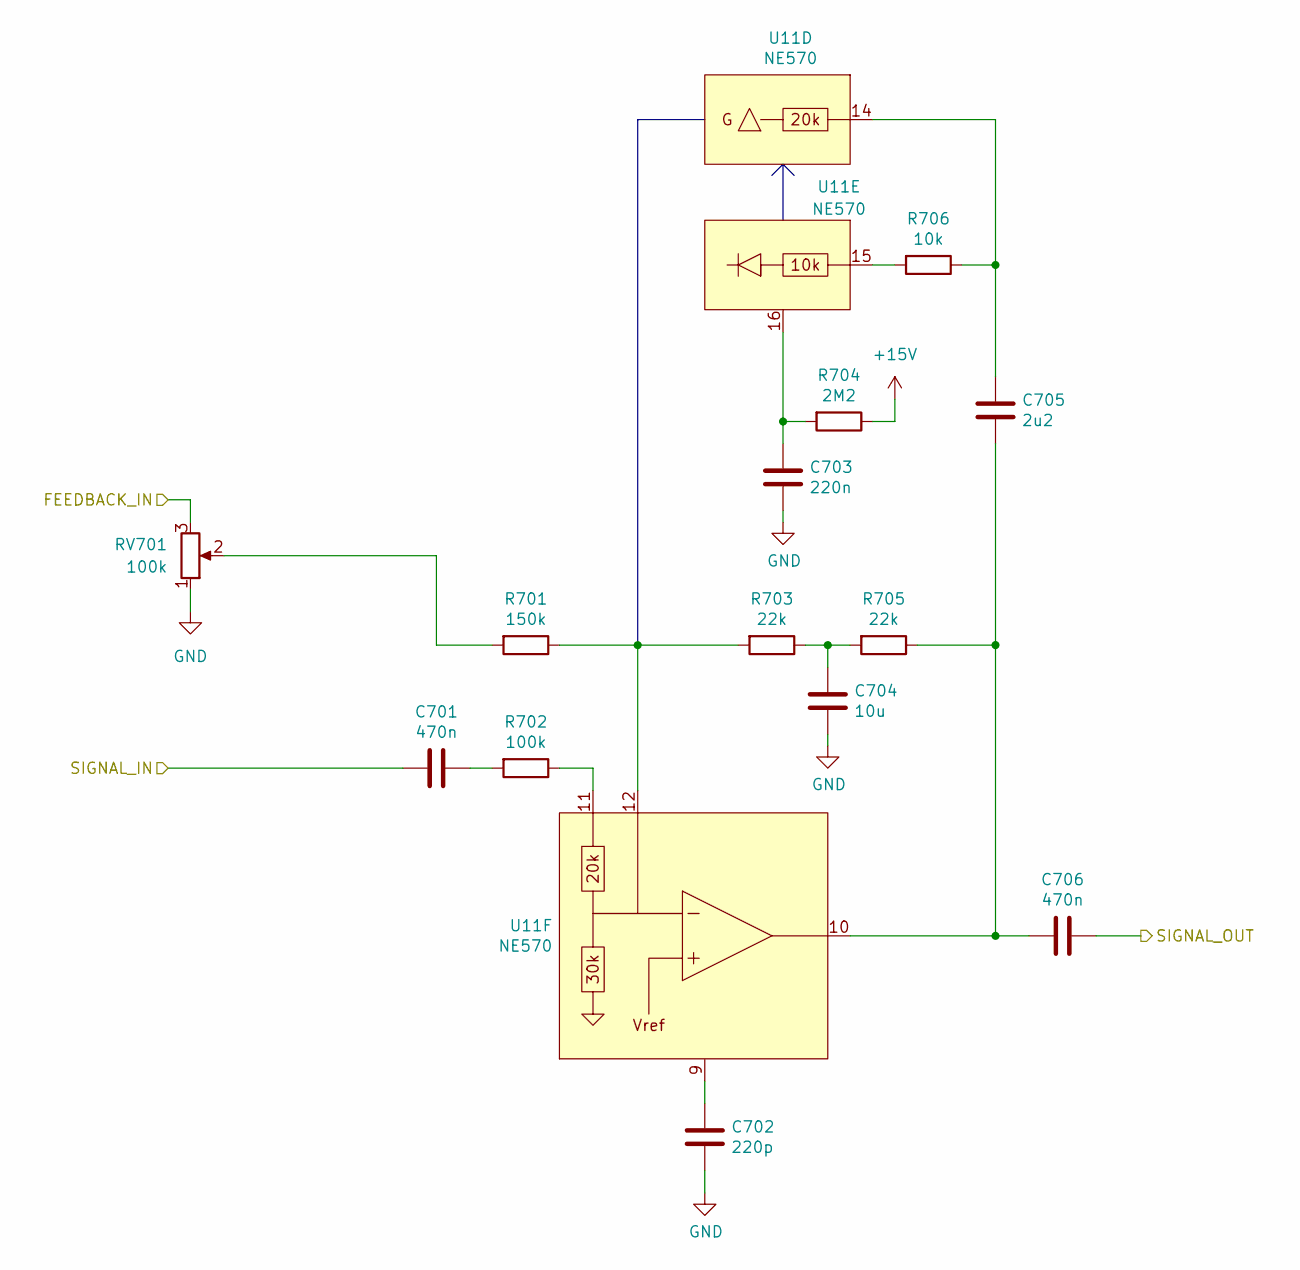
[picture p111: schematic compressor_and_fdbk_mixer.kicad_sch]

Parts:
C701, C706: 470n; C_Rect_L7.0mm_W3.5mm_P5.00mm
C702: 220p; C_0805_2012Metric
C703: 220n; C_0805_2012Metric
C704: 10u; C_0805_2012Metric
C705: 2u2; C_0805_2012Metric
R701: 150k; R_0805_2012Metric
R702: 100k; R_0805_2012Metric
R703, R705: 22k; R_0805_2012Metric
R704: 2M2; R_0805_2012Metric
R706: 10k; R_0805_2012Metric
RV701: 100k; Potentiometer_Alpha_RD901F-40-00D_Single_Vertical
U11: NE570; DIP-16_W7.62mm_Socket

Connections:
+15V: R704.1
FEEDBACK_IN: RV701.3
GND: C702.2, C703.2, C704.2, RV701.1
unnamed: C701.1, R702.2
unnamed: C702.1, U11.9
unnamed: C703.1, R704.2, U11.16
unnamed: C704.1, R703.1, R705.2
unnamed: C705.1, R706.1, U11.14
unnamed: C705.2, C706.2, R705.1, U11.10
unnamed: R701.1, R703.2, U11.12
unnamed: R701.2, RV701.2
unnamed: R702.1, U11.11
unnamed: R706.2, U11.15
SIGNAL_IN: C701.2
SIGNAL_OUT: C706.1
