JordanAceto/josh_Ox_ribbon_synth/circuit_boards/VCF_VCA_BBD_board/kicad_7/expandor_and_wet_dry_mixer.kicad_sch

## KiCad design circuit_boards/VCF_VCA_BBD_board/kicad_7/expandor_and_wet_dry_mixer.kicad_sch (2023-03-27)

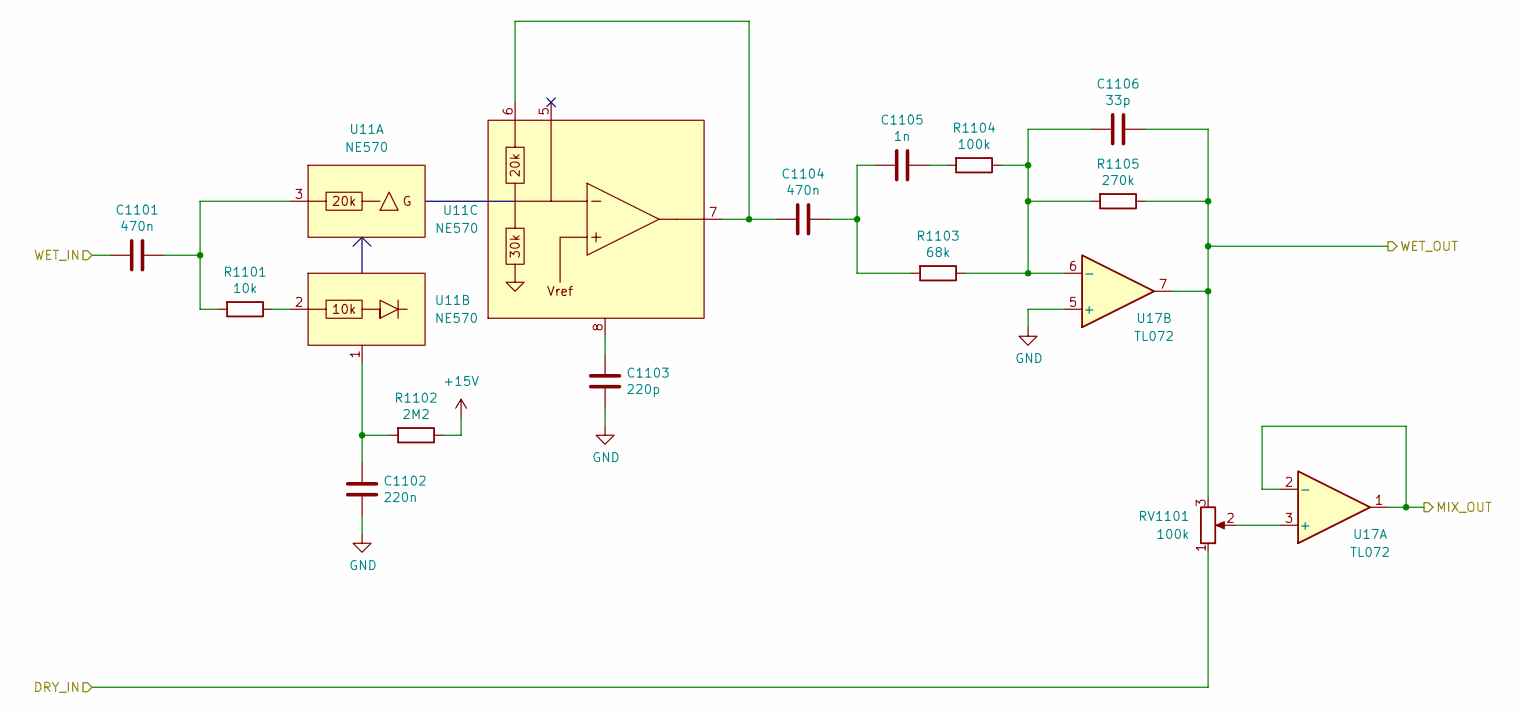
[picture p112: schematic expandor_and_wet_dry_mixer.kicad_sch]

Parts:
C1101, C1104: 470n; C_Rect_L7.0mm_W3.5mm_P5.00mm
C1102: 220n; C_0805_2012Metric
C1103: 220p; C_0805_2012Metric
C1105: 1n; C_0805_2012Metric
C1106: 33p; C_0805_2012Metric
R1101: 10k; R_0805_2012Metric
R1102: 2M2; R_0805_2012Metric
R1103: 68k; R_0805_2012Metric
R1104: 100k; R_0805_2012Metric
R1105: 270k; R_0805_2012Metric
RV1101: 100k; Potentiometer_Alpha_RD901F-40-00D_Single_Vertical
U11: NE570; DIP-16_W7.62mm_Socket
U17: TL072; SOIC-8_3.9x4.9mm_P1.27mm

Connections:
+15V: R1102.1
DRY_IN: RV1101.1
GND: C1102.2, C1103.2, U17.5 (+)
MIX_OUT: U17.1, U17.2 (-)
unnamed: C1101.1, R1101.2, U11.3
unnamed: C1102.1, R1102.2, U11.1
unnamed: C1103.1, U11.8
unnamed: C1104.1, C1105.2, R1103.2
unnamed: C1104.2, U11.6, U11.7
unnamed: C1105.1, R1104.2
unnamed: C1106.2, R1103.1, R1104.1, R1105.2, U17.6 (-)
unnamed: R1101.1, U11.2
unnamed: RV1101.2, U17.3 (+)
WET_IN: C1101.2
WET_OUT: C1106.1, R1105.1, RV1101.3, U17.7
