JordanAceto/josh_Ox_ribbon_synth/circuit_boards/VCF_VCA_BBD_board/kicad_7/power_supply.kicad_sch

## KiCad design circuit_boards/VCF_VCA_BBD_board/kicad_7/power_supply.kicad_sch (2023-03-27)

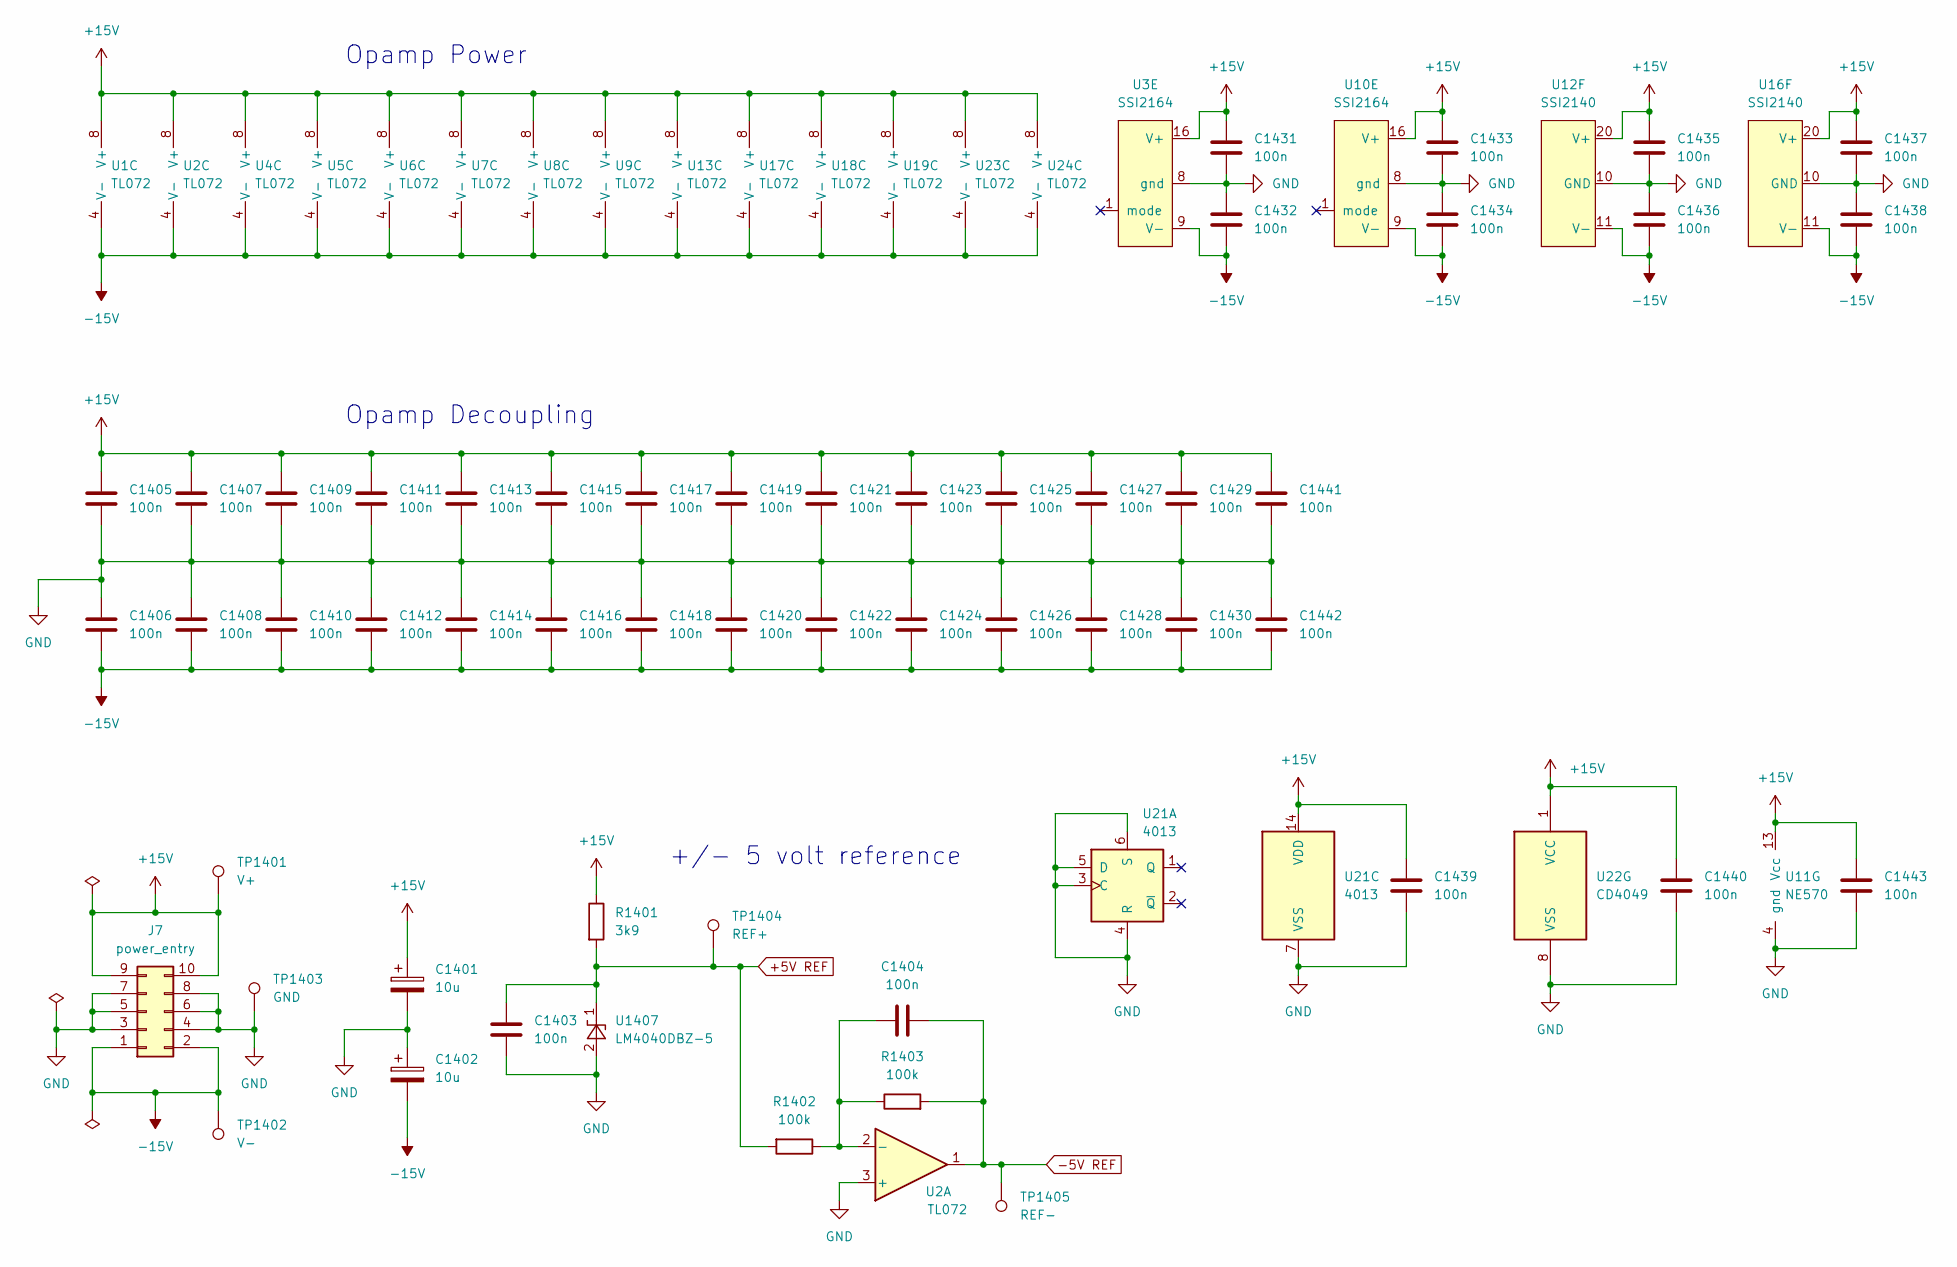
[picture p113: schematic power_supply.kicad_sch]

Parts:
C1401, C1402: 10u; CP_Radial_D6.3mm_P2.50mm
C1403, C1404, C1405, C1406, C1407, C1408, C1409, C1410, C1411, C1412, C1413, C1414, C1415, C1416, C1417, C1418, C1419, C1420, C1421, C1422, C1423, C1424, C1425, C1426, C1427, C1428, C1429, C1430, C1431, C1432, C1433, C1434, C1435, C1436, C1437, C1438, C1439, C1440, C1441, C1442, C1443: 100n; C_0805_2012Metric
J7: power_entry; IDC-Header_2x05_P2.54mm_Vertical
R1401: 3k9; R_0805_2012Metric
R1402, R1403: 100k; R_0805_2012Metric
TP1401: V+; TestPoint_Keystone_5000-5004_Miniature
TP1402: V-; TestPoint_Keystone_5000-5004_Miniature
TP1403: GND; TestPoint_Bridge_Pitch7.62mm_Drill1.3mm
TP1404: REF+; TestPoint_Keystone_5000-5004_Miniature
TP1405: REF-; TestPoint_Keystone_5000-5004_Miniature
U1, U2, U4, U5, U6, U7, U8, U9, U13, U17, U18, U19, U23, U24: TL072; SOIC-8_3.9x4.9mm_P1.27mm
U3, U10: SSI2164; SOIC-16_3.9x9.9mm_P1.27mm
U11: NE570; DIP-16_W7.62mm_Socket
U12, U16: SSI2140; TSSOP-20_4.4x6.5mm_P0.65mm
U21: 4013; SOIC-14_3.9x8.7mm_P1.27mm
U22: CD4049; TSSOP-16_4.4x5mm_P0.65mm
U1407: LM4040DBZ-5; SOT-23

Connections:
+5V REF: C1403.1, R1401.2, R1402.2, TP1404.1, U1407.1 (K)
+15V: C1401.1, C1405.1, C1407.1, C1409.1, C1411.1, C1413.1, C1415.1, C1417.1, C1419.1, C1421.1, C1423.1, C1425.1, C1427.1, C1429.1, C1431.1, C1433.1, C1435.1, C1437.1, C1439.1, C1440.1, C1441.1, C1443.1, J7.9, J7.10, R1401.1, TP1401.1, U1.8 (V+), U2.8 (V+), U3.16 (V+), U4.8 (V+), U5.8 (V+), U6.8 (V+), U7.8 (V+), U8.8 (V+), U9.8 (V+), U10.16 (V+), U11.13 (Vcc), U12.20 (V+), U13.8 (V+), U16.20 (V+), U17.8 (V+), U18.8 (V+), U19.8 (V+), U21.14 (VDD), U22.1 (VCC), U23.8 (V+), U24.8 (V+)
-5V REF: C1404.2, R1403.2, TP1405.1, U2.1
-15V: C1402.2, C1406.2, C1408.2, C1410.2, C1412.2, C1414.2, C1416.2, C1418.1, C1420.2, C1422.2, C1424.2, C1426.2, C1428.2, C1430.2, C1432.2, C1434.2, C1436.2, C1438.2, C1442.2, J7.1, J7.2, TP1402.1, U1.4 (V-), U2.4 (V-), U3.9 (V-), U4.4 (V-), U5.4 (V-), U6.4 (V-), U7.4 (V-), U8.4 (V-), U9.4 (V-), U10.9 (V-), U12.11 (V-), U13.4 (V-), U16.11 (V-), U17.4 (V-), U18.4 (V-), U19.4 (V-), U23.4 (V-), U24.4 (V-)
GND: C1401.2, C1402.1, C1403.2, C1405.2, C1406.1, C1407.2, C1408.1, C1409.2, C1410.1, C1411.2, C1412.1, C1413.2, C1414.1, C1415.2, C1416.1, C1417.2, C1418.2, C1419.2, C1420.1, C1421.2, C1422.1, C1423.2, C1424.1, C1425.2, C1426.1, C1427.2, C1428.1, C1429.2, C1430.1, C1431.2, C1432.1, C1433.2, C1434.1, C1435.2, C1436.1, C1437.2, C1438.1, C1439.2, C1440.2, C1441.2, C1442.1, C1443.2, J7.3, J7.4, J7.5, J7.6, J7.7, J7.8, TP1403.1, U2.3 (+), U3.8 (gnd), U10.8 (gnd), U11.4 (gnd), U12.10 (GND), U16.10 (GND), U21.3 (C), U21.4 (R), U21.5 (D), U21.6 (S), U21.7 (VSS), U22.8 (VSS), U1407.2 (A)
unnamed: C1404.1, R1402.1, R1403.1, U2.2 (-)

Notes on the sheet:
Opamp Decoupling
Opamp Power
+/- 5 volt reference
