JordanAceto/josh_Ox_ribbon_synth/circuit_boards/main_VCO_board/kicad_7/PWM_generator.kicad_sch

## KiCad design circuit_boards/main_VCO_board/kicad_7/PWM_generator.kicad_sch (2023-03-27)

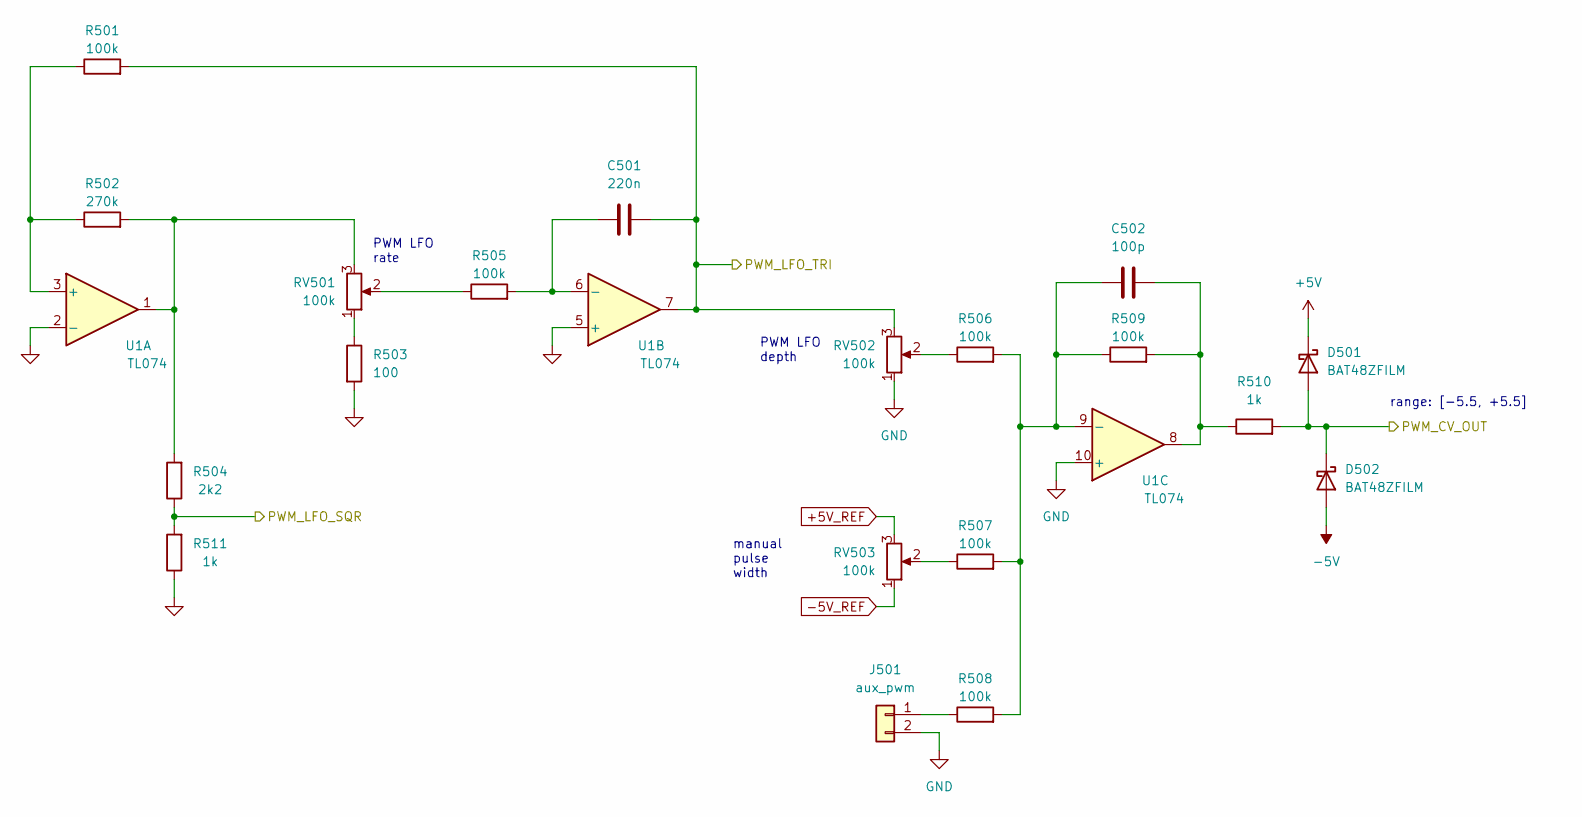
[picture p114: schematic PWM_generator.kicad_sch]

Parts:
C501: 220n; C_Rect_L7.0mm_W2.5mm_P5.00mm
C502: 100p; C_0805_2012Metric
D501, D502: BAT48ZFILM; D_SOD-123
J501: aux_pwm; PinHeader_1x02_P2.54mm_Vertical
R501, R505, R506, R507, R508, R509: 100k; R_0805_2012Metric
R502: 270k; R_0805_2012Metric
R503: 100; R_0805_2012Metric
R504: 2k2; R_0805_2012Metric
R510, R511: 1k; R_0805_2012Metric
RV501, RV502, RV503: 100k; Potentiometer_Alpha_RD901F-40-00D_Single_Vertical
U1: TL074; SOIC-14_3.9x8.7mm_P1.27mm

Connections:
+5V: D501.1 (K)
+5V_REF: RV503.3
-5V: D502.2 (A)
-5V_REF: RV503.1
GND: J501.2, RV502.1, U1.10 (+)
unnamed: C501.1, R505.2, U1.6 (-)
unnamed: C502.1, R506.2, R507.2, R508.2, R509.1, U1.9 (-)
unnamed: C502.2, R509.2, R510.1, U1.8
unnamed: J501.1, R508.1
unnamed: R501.1, R502.1, U1.3 (+)
unnamed: R502.2, R504.2, RV501.3, U1.1
unnamed: R503.1, RV501.1
unnamed: R505.1, RV501.2
unnamed: R506.1, RV502.2
unnamed: R507.1, RV503.2
PWM_CV_OUT: D501.2 (A), D502.1 (K), R510.2
PWM_LFO_SQR: R504.1, R511.2
PWM_LFO_TRI: C501.2, R501.2, RV502.3, U1.7
~: R503.2, R511.1, U1.2 (-), U1.5 (+)

Notes on the sheet:
PWM LFO depth
range: [-5.5, +5.5]
manual pulse width
PWM LFO rate
