JordanAceto/josh_Ox_ribbon_synth/circuit_boards/main_VCO_board/kicad_7/VCO_core.kicad_sch

## KiCad design circuit_boards/main_VCO_board/kicad_7/VCO_core.kicad_sch (2023-03-27)

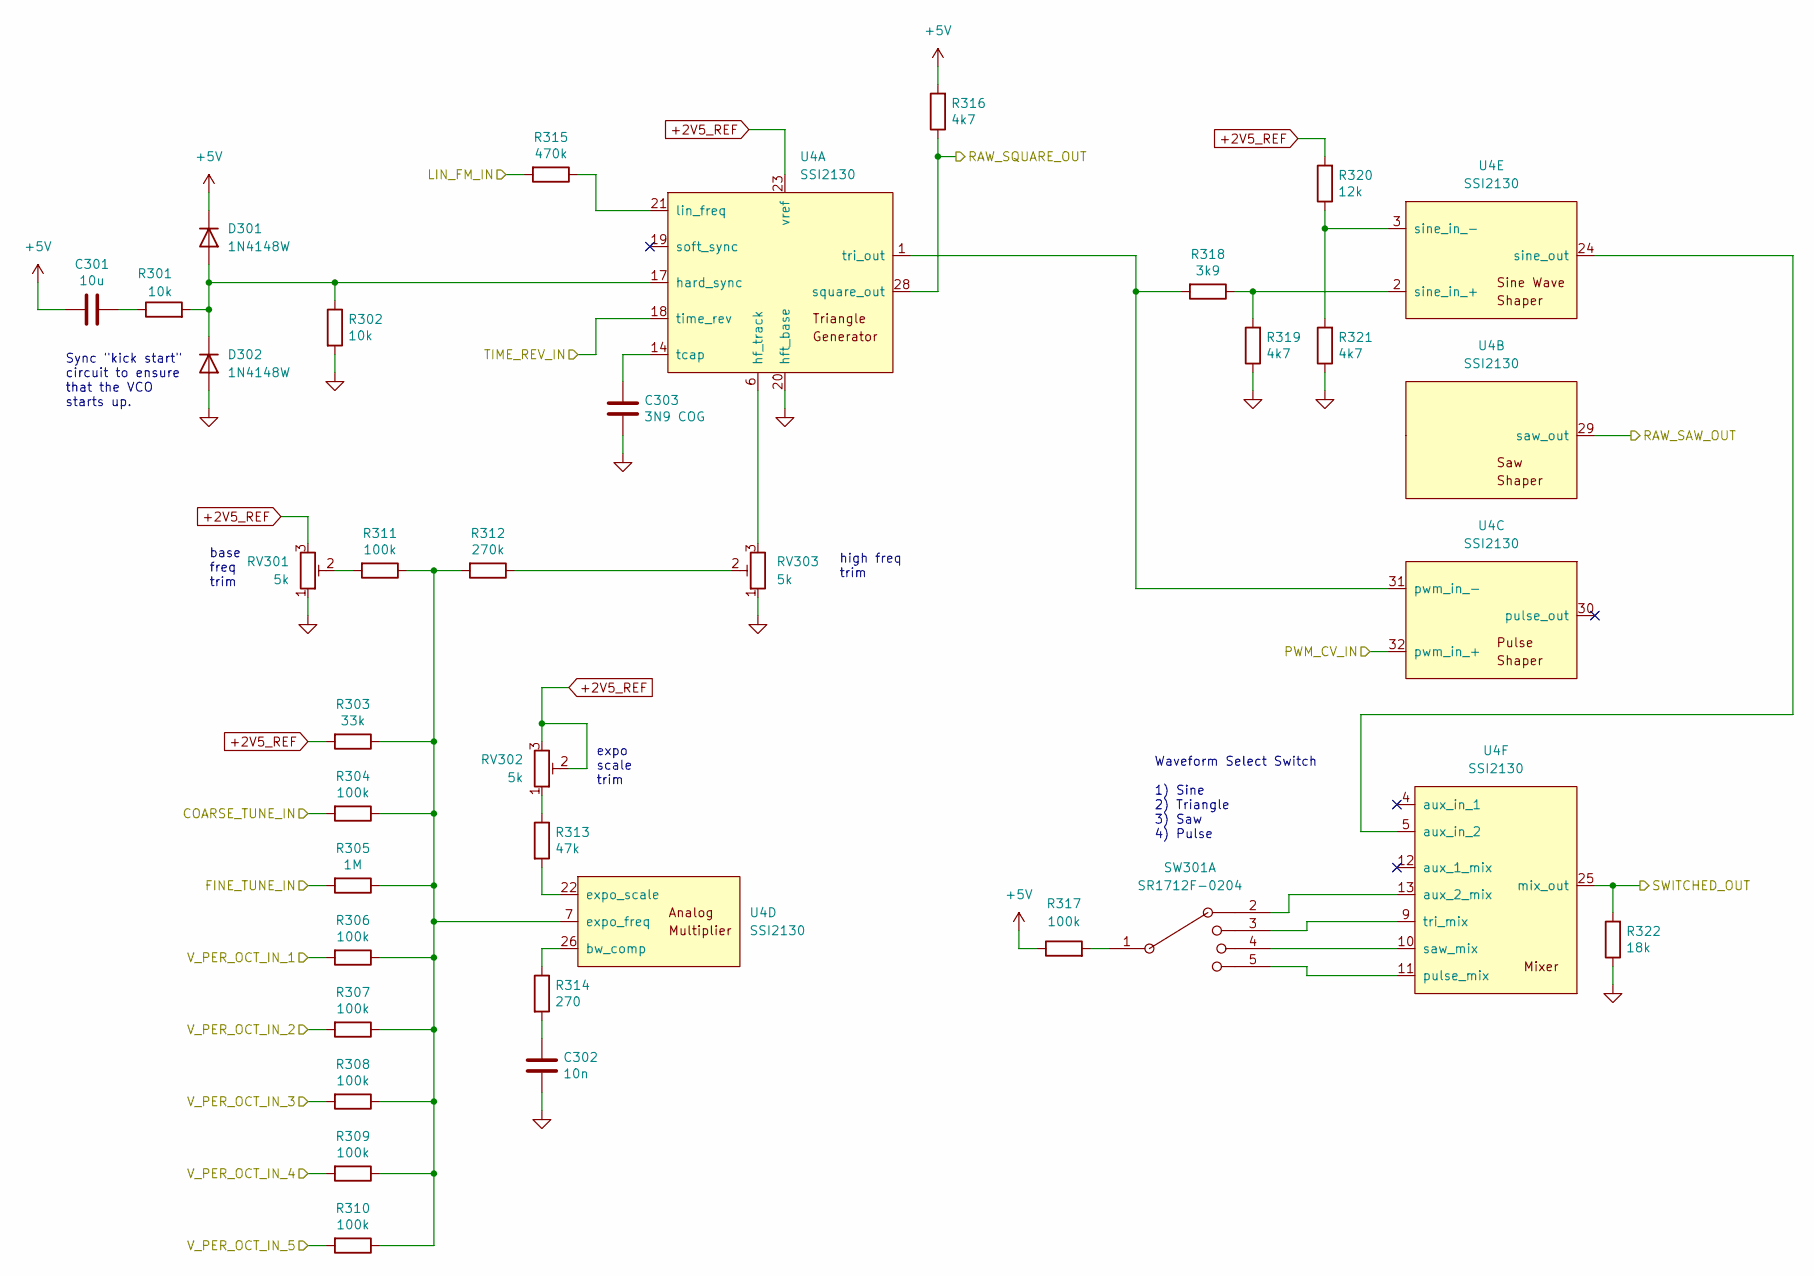
[picture p115: schematic VCO_core.kicad_sch]

Parts:
C301: 10u; C_0805_2012Metric
C302: 10n; C_0805_2012Metric
C303: 3N9 COG; C_0805_2012Metric
D301, D302: 1N4148W; D_SOD-123
R301, R302: 10k; R_0805_2012Metric
R303: 33k; R_0805_2012Metric
R304, R306, R307, R308, R309, R310, R311, R317: 100k; R_0805_2012Metric
R305: 1M; R_0805_2012Metric
R312: 270k; R_0805_2012Metric
R313: 47k; R_0805_2012Metric
R314: 270; R_0805_2012Metric
R315: 470k; R_0805_2012Metric
R316, R319, R321: 4k7; R_0805_2012Metric
R318: 3k9; R_0805_2012Metric
R320: 12k; R_0805_2012Metric
R322: 18k; R_0805_2012Metric
RV301, RV302, RV303: 5k; Potentiometer_Bourns_3296W_Vertical
SW301: SR1712F-0204; SR1712F_rotary_switch
U4: SSI2130; PQN32_HandSoldering

Connections:
+2V5_REF: R303.2, R320.2, RV301.3, RV302.2, RV302.3, U4.23 (vref)
+5V: C301.2, D301.1 (K), R316.2, R317.1
COARSE_TUNE_IN: R304.2
FINE_TUNE_IN: R305.2
LIN_FM_IN: R315.2
unnamed: C301.1, R301.1
unnamed: C302.1, R314.2
unnamed: C303.1, U4.14 (tcap)
unnamed: D301.2 (A), D302.1 (K), R301.2, R302.1, U4.17 (hard_sync)
unnamed: R303.1, R304.1, R305.1, R306.1, R307.1, R308.1, R309.1, R310.1, R311.1, R312.2, U4.7 (expo_freq)
unnamed: R311.2, RV301.2
unnamed: R312.1, RV303.2
unnamed: R313.1, RV302.1
unnamed: R313.2, U4.22 (expo_scale)
unnamed: R314.1, U4.26 (bw_comp)
unnamed: R315.1, U4.21 (lin_freq)
unnamed: R317.2, SW301.1
unnamed: R318.1, R319.2, U4.2 (sine_in_+)
unnamed: R318.2, U4.1 (tri_out), U4.31 (pwm_in_-)
unnamed: R320.1, R321.2, U4.3 (sine_in_-)
unnamed: RV303.3, U4.6 (hf_track)
unnamed: SW301.2, U4.13 (aux_2_mix)
unnamed: SW301.3, U4.9 (tri_mix)
unnamed: SW301.4, U4.10 (saw_mix)
unnamed: SW301.5, U4.11 (pulse_mix)
unnamed: U4.5 (aux_in_2), U4.24 (sine_out)
PWM_CV_IN: U4.32 (pwm_in_+)
RAW_SAW_OUT: U4.29 (saw_out)
RAW_SQUARE_OUT: R316.1, U4.28 (square_out)
SWITCHED_OUT: R322.2, U4.25 (mix_out)
TIME_REV_IN: U4.18 (time_rev)
V_PER_OCT_IN_1: R306.2
V_PER_OCT_IN_2: R307.2
V_PER_OCT_IN_3: R308.2
V_PER_OCT_IN_4: R309.2
V_PER_OCT_IN_5: R310.2
~: C302.2, C303.2, D302.2 (A), R302.2, R319.1, R321.1, R322.1, RV301.1, RV303.1, U4.20 (hft_base)

Notes on the sheet:
Waveform Select Switch 1) Sine 2) Triangle 3) Saw 4) Pulse
Sync "kick start" circuit to ensure that the VCO starts up.
high freq trim
base freq trim
expo scale trim
