JordanAceto/josh_Ox_ribbon_synth/circuit_boards/main_VCO_board/kicad_7/audio_mixer.kicad_sch

## KiCad design circuit_boards/main_VCO_board/kicad_7/audio_mixer.kicad_sch (2023-03-27)

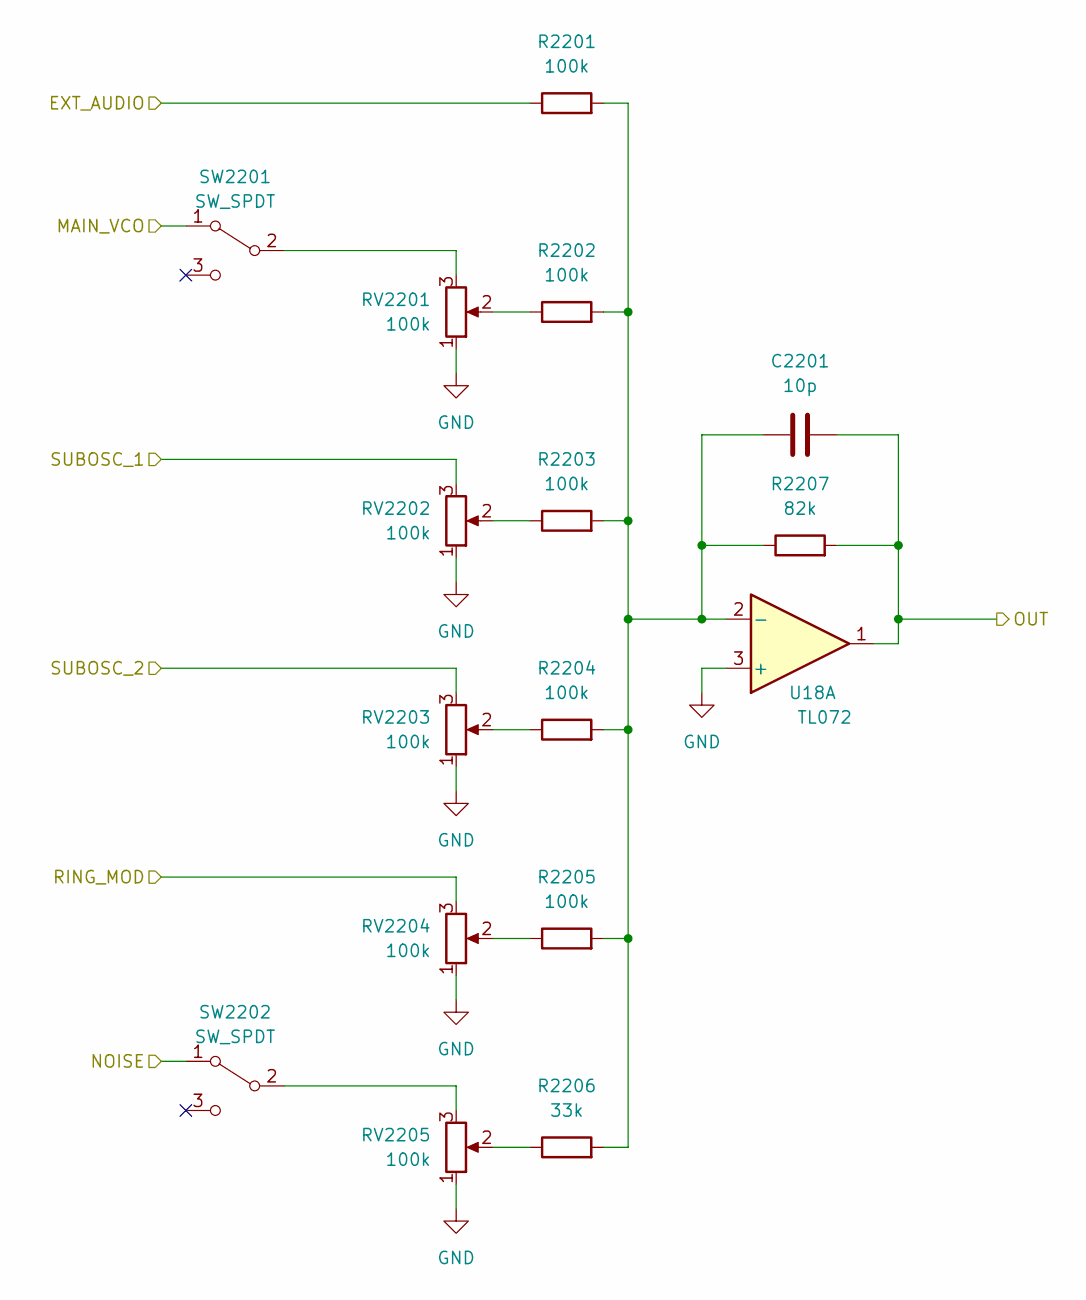
[picture p116: schematic audio_mixer.kicad_sch]

Parts:
C2201: 10p; C_0805_2012Metric
R2201, R2202, R2203, R2204, R2205: 100k; R_0805_2012Metric
R2206: 33k; R_0805_2012Metric
R2207: 82k; R_0805_2012Metric
RV2201, RV2202, RV2203, RV2204, RV2205: 100k; Potentiometer_Alpha_RD901F-40-00D_Single_Vertical
SW2201, SW2202: SW_SPDT; SPDT_mini_toggle
U18: TL072; SOIC-8_3.9x4.9mm_P1.27mm

Connections:
EXT_AUDIO: R2201.1
GND: RV2201.1, RV2202.1, RV2203.1, RV2204.1, RV2205.1, U18.3 (+)
MAIN_VCO: SW2201.1 (A)
NOISE: SW2202.1 (A)
unnamed: C2201.1, R2201.2, R2202.2, R2203.2, R2204.2, R2205.2, R2206.2, R2207.1, U18.2 (-)
unnamed: R2202.1, RV2201.2
unnamed: R2203.1, RV2202.2
unnamed: R2204.1, RV2203.2
unnamed: R2205.1, RV2204.2
unnamed: R2206.1, RV2205.2
unnamed: RV2201.3, SW2201.2 (B)
unnamed: RV2205.3, SW2202.2 (B)
OUT: C2201.2, R2207.2, U18.1
RING_MOD: RV2204.3
SUBOSC_1: RV2202.3
SUBOSC_2: RV2203.3
