JordanAceto/josh_Ox_ribbon_synth/circuit_boards/main_VCO_board/kicad_7/basic_pulse_shaper.kicad_sch

## KiCad design circuit_boards/main_VCO_board/kicad_7/basic_pulse_shaper.kicad_sch (2023-03-27)

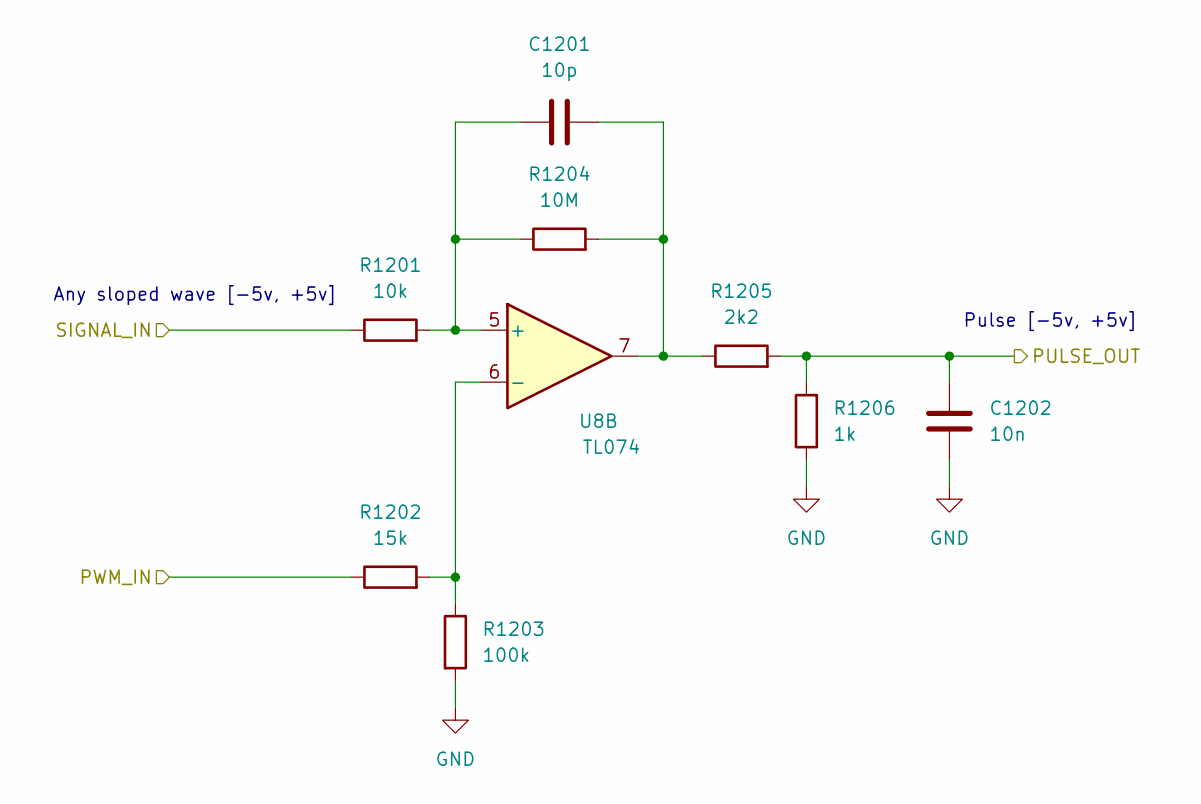
[picture p117: schematic basic_pulse_shaper.kicad_sch]

Parts:
C1201: 10p; C_0805_2012Metric
C1202: 10n; C_0805_2012Metric
R1201: 10k; R_0805_2012Metric
R1202: 15k; R_0805_2012Metric
R1203: 100k; R_0805_2012Metric
R1204: 10M; R_0805_2012Metric
R1205: 2k2; R_0805_2012Metric
R1206: 1k; R_0805_2012Metric
U8: TL074; SOIC-14_3.9x8.7mm_P1.27mm

Connections:
GND: C1202.1, R1203.2, R1206.1
unnamed: C1201.1, R1201.2, R1204.1, U8.5 (+)
unnamed: C1201.2, R1204.2, R1205.1, U8.7
unnamed: R1202.2, R1203.1, U8.6 (-)
PULSE_OUT: C1202.2, R1205.2, R1206.2
PWM_IN: R1202.1
SIGNAL_IN: R1201.1

Notes on the sheet:
Any sloped wave [-5v, +5v]
Pulse [-5v, +5v]
