JordanAceto/josh_Ox_ribbon_synth/circuit_boards/main_VCO_board/kicad_7/harmonic_pulse_shaper.kicad_sch

## KiCad design circuit_boards/main_VCO_board/kicad_7/harmonic_pulse_shaper.kicad_sch (2023-03-27)

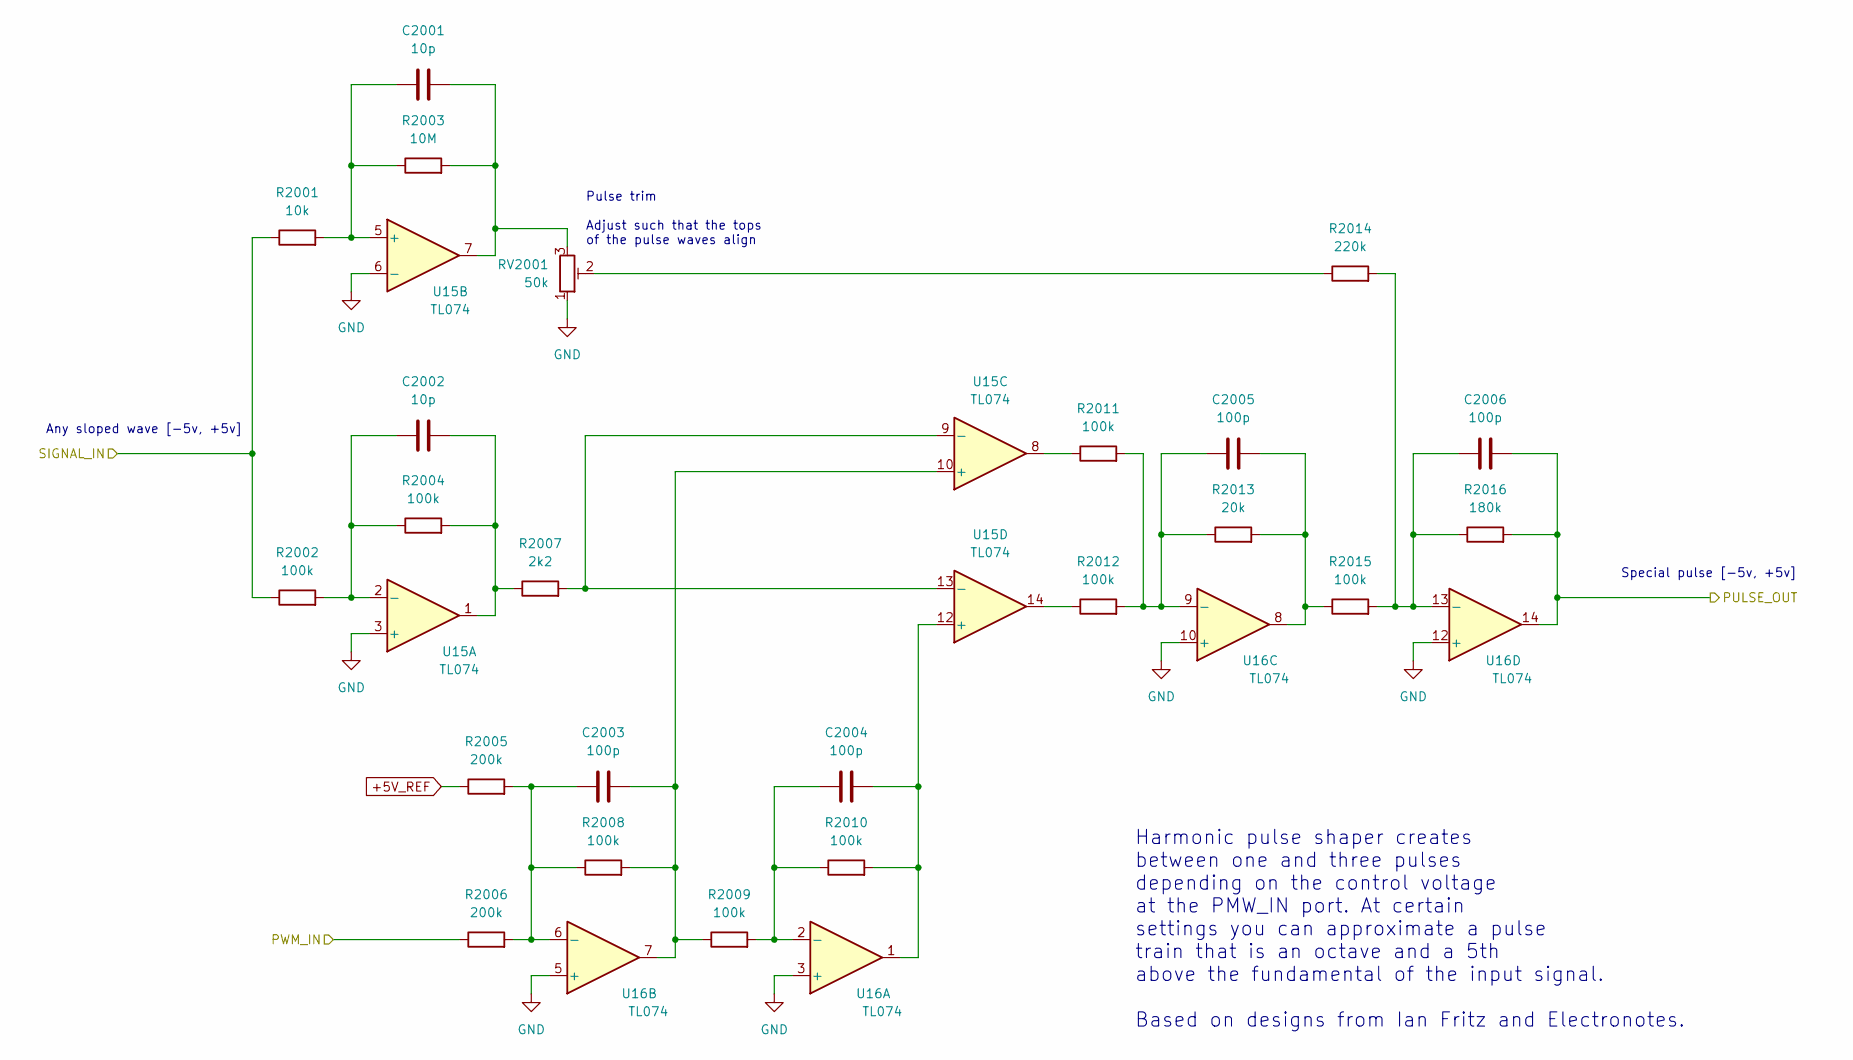
[picture p118: schematic harmonic_pulse_shaper.kicad_sch]

Parts:
C2001, C2002: 10p; C_0805_2012Metric
C2003, C2004, C2005, C2006: 100p; C_0805_2012Metric
R2001: 10k; R_0805_2012Metric
R2002, R2004, R2008, R2009, R2010, R2011, R2012, R2015: 100k; R_0805_2012Metric
R2003: 10M; R_0805_2012Metric
R2005, R2006: 200k; R_0805_2012Metric
R2007: 2k2; R_0805_2012Metric
R2013: 20k; R_0805_2012Metric
R2014: 220k; R_0805_2012Metric
R2016: 180k; R_0805_2012Metric
RV2001: 50k; Potentiometer_Bourns_3296W_Vertical
U15, U16: TL074; SOIC-14_3.9x8.7mm_P1.27mm

Connections:
+5V_REF: R2005.1
GND: RV2001.1, U15.3 (+), U15.6 (-), U16.3 (+), U16.5 (+), U16.10 (+), U16.12 (+)
unnamed: C2001.1, R2001.2, R2003.1, U15.5 (+)
unnamed: C2001.2, R2003.2, RV2001.3, U15.7
unnamed: C2002.1, R2002.2, R2004.1, U15.2 (-)
unnamed: C2002.2, R2004.2, R2007.1, U15.1
unnamed: C2003.1, R2005.2, R2006.2, R2008.1, U16.6 (-)
unnamed: C2003.2, R2008.2, R2009.1, U15.10 (+), U16.7
unnamed: C2004.1, R2009.2, R2010.1, U16.2 (-)
unnamed: C2004.2, R2010.2, U15.12 (+), U16.1
unnamed: C2005.1, R2011.2, R2012.2, R2013.1, U16.9 (-)
unnamed: C2005.2, R2013.2, R2015.1, U16.8
unnamed: C2006.1, R2014.2, R2015.2, R2016.1, U16.13 (-)
unnamed: R2007.2, U15.9 (-), U15.13 (-)
unnamed: R2011.1, U15.8
unnamed: R2012.1, U15.14
unnamed: R2014.1, RV2001.2
PULSE_OUT: C2006.2, R2016.2, U16.14
PWM_IN: R2006.1
SIGNAL_IN: R2001.1, R2002.1

Notes on the sheet:
Special pulse [-5v, +5v]
Harmonic pulse shaper creates between one and three pulses depending on the control voltage at the PMW_IN port. At certain settings you can approximate a pulse train that is an octave and a 5th above the fundamental of the input signal. Based on designs from Ian Fritz and Electronotes.
Any sloped wave [-5v, +5v]
Pulse trim Adjust such that the tops of the pulse waves align
