JordanAceto/josh_Ox_ribbon_synth/circuit_boards/main_VCO_board/kicad_7/level_shifter.kicad_sch

## KiCad design circuit_boards/main_VCO_board/kicad_7/level_shifter.kicad_sch (2023-03-27)

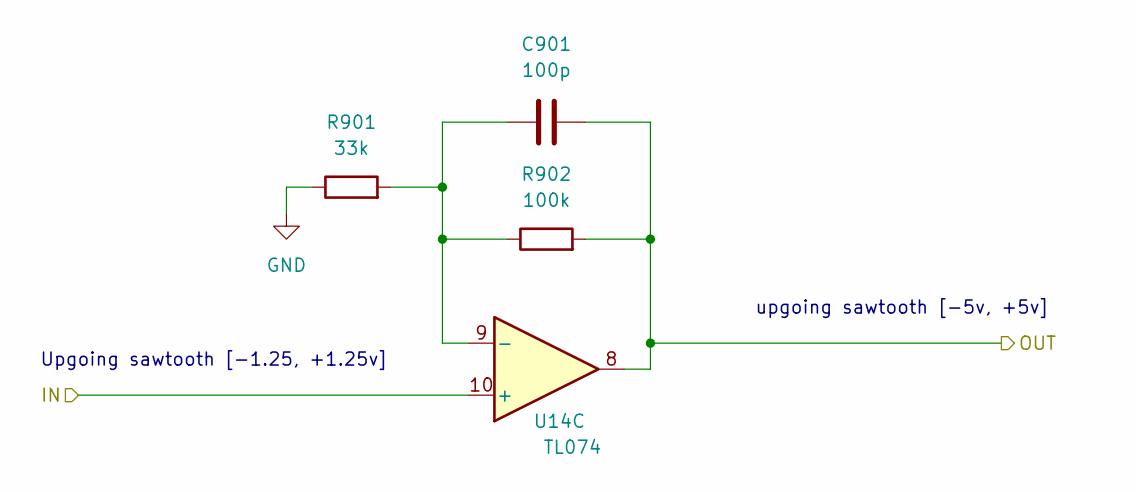
[picture p119: schematic level_shifter.kicad_sch]

Parts:
C901: 100p; C_0805_2012Metric
R901: 33k; R_0805_2012Metric
R902: 100k; R_0805_2012Metric
U14: TL074; SOIC-14_3.9x8.7mm_P1.27mm

Connections:
GND: R901.1
IN: U14.10 (+)
unnamed: C901.1, R901.2, R902.1, U14.9 (-)
OUT: C901.2, R902.2, U14.8

Notes on the sheet:
Upgoing sawtooth [-1.25, +1.25v]
upgoing sawtooth [-5v, +5v]
