JordanAceto/josh_Ox_ribbon_synth/circuit_boards/main_VCO_board/kicad_7/lin_FM_conditioner.kicad_sch

## KiCad design circuit_boards/main_VCO_board/kicad_7/lin_FM_conditioner.kicad_sch (2023-03-27)

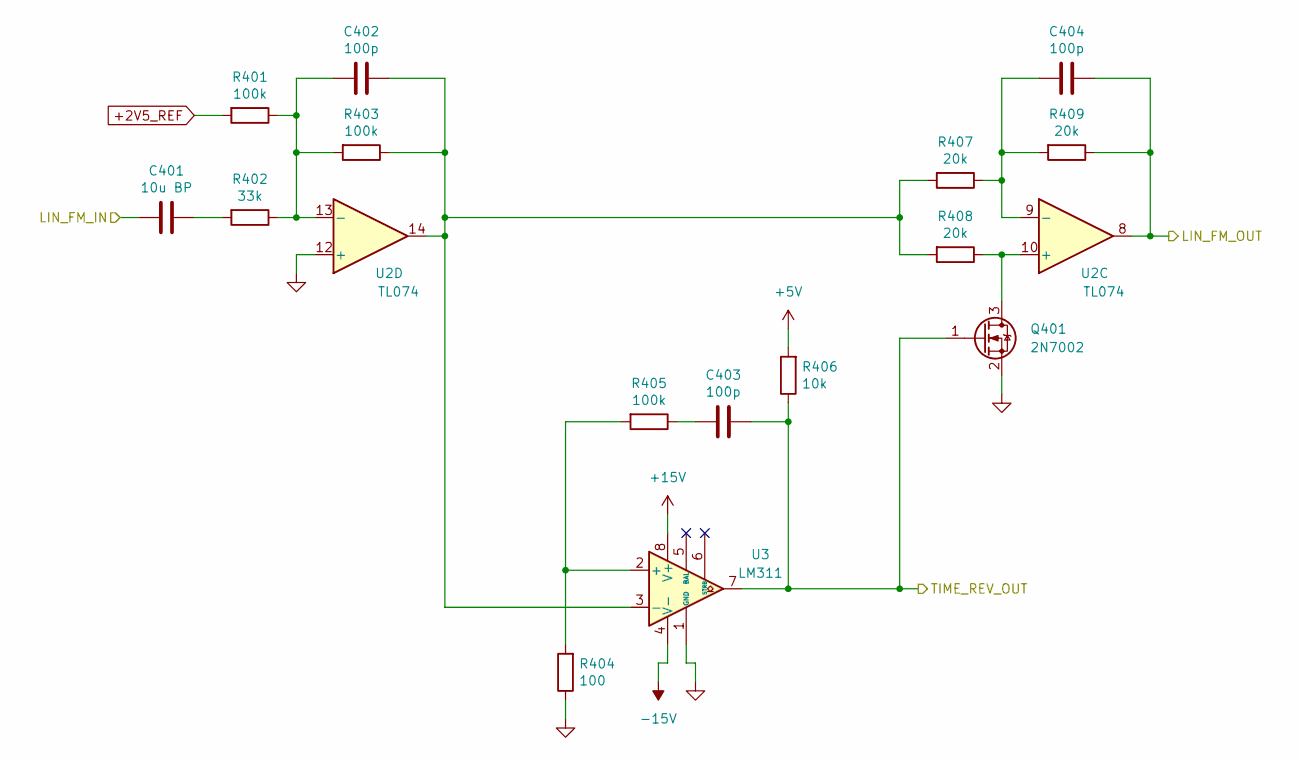
[picture p120: schematic lin_FM_conditioner.kicad_sch]

Parts:
C401: 10u BP; C_Rect_L7.2mm_W3.5mm_P5.00mm_FKS2_FKP2_MKS2_MKP2
C402, C403, C404: 100p; C_0805_2012Metric
Q401: 2N7002; SOT-23
R401, R403, R405: 100k; R_0805_2012Metric
R402: 33k; R_0805_2012Metric
R404: 100; R_0805_2012Metric
R406: 10k; R_0805_2012Metric
R407, R408, R409: 20k; R_0805_2012Metric
U2: TL074; SOIC-14_3.9x8.7mm_P1.27mm
U3: LM311; SOIC-8_3.9x4.9mm_P1.27mm

Connections:
+2V5_REF: R401.2
+5V: R406.2
+15V: U3.8 (V+)
-15V: U3.4 (V-)
LIN_FM_IN: C401.2
LIN_FM_OUT: C404.1, R409.1, U2.8
unnamed: C401.1, R402.2
unnamed: C402.1, R403.1, R407.2, R408.2, U2.14, U3.3 (-)
unnamed: C402.2, R401.1, R402.1, R403.2, U2.13 (-)
unnamed: C403.2, R405.1
unnamed: C404.2, R407.1, R409.2, U2.9 (-)
unnamed: Q401.3 (D), R408.1, U2.10 (+)
unnamed: R404.2, R405.2, U3.2 (+)
TIME_REV_OUT: C403.1, Q401.1 (G), R406.1, U3.7
~: Q401.2 (S), R404.1, U2.12 (+), U3.1 (GND)
