JordanAceto/josh_Ox_ribbon_synth/circuit_boards/main_VCO_board/kicad_7/main_VCO.kicad_sch

## KiCad design circuit_boards/main_VCO_board/kicad_7/main_VCO.kicad_sch (2023-03-27)

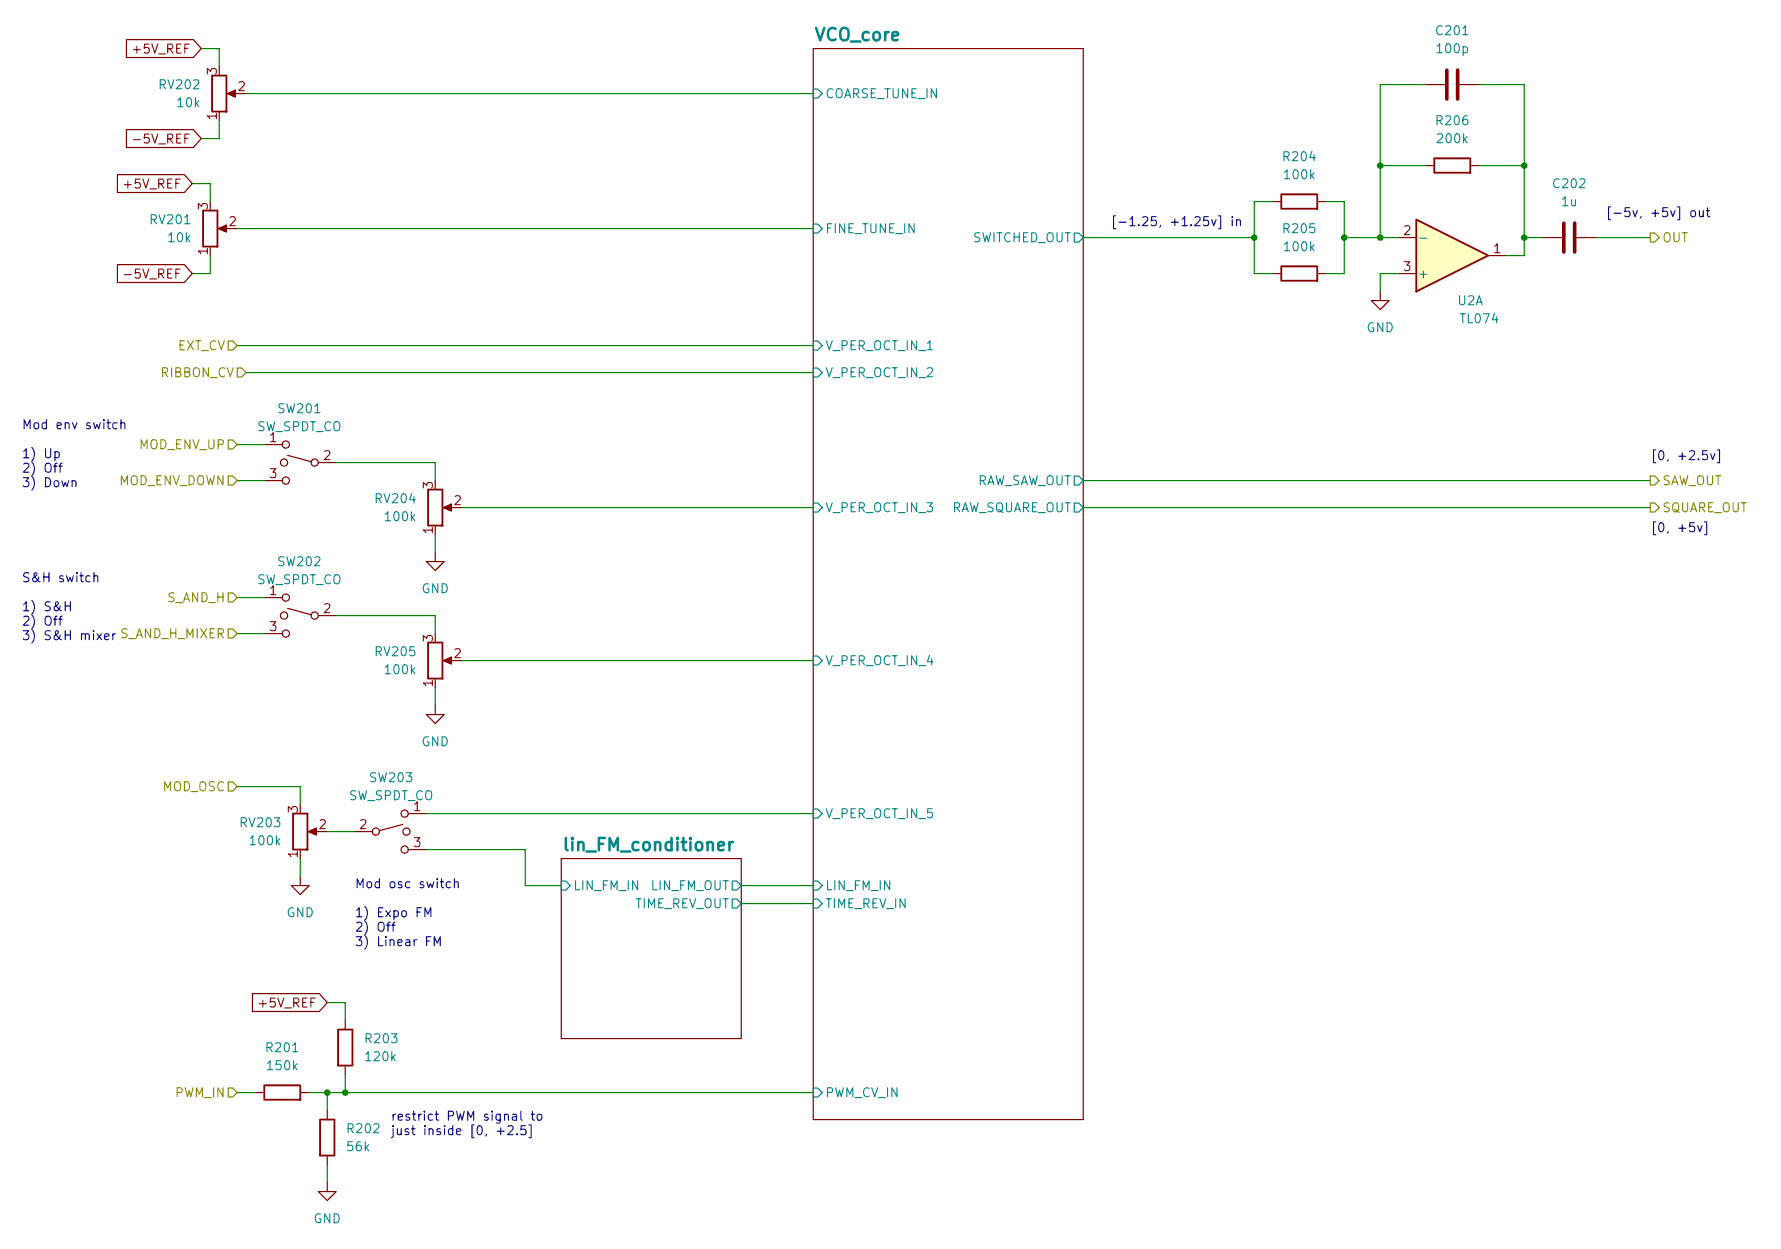
[picture p121: schematic main_VCO.kicad_sch]

Parts:
C201: 100p; C_0805_2012Metric
C202: 1u; C_Rect_L7.2mm_W5.5mm_P5.00mm_FKS2_FKP2_MKS2_MKP2
R201: 150k; R_0805_2012Metric
R202: 56k; R_0805_2012Metric
R203: 120k; R_0805_2012Metric
R204, R205: 100k; R_0805_2012Metric
R206: 200k; R_0805_2012Metric
RV201, RV202: 10k; Potentiometer_Alpha_RD901F-40-00D_Single_Vertical
RV203, RV204, RV205: 100k; Potentiometer_Alpha_RD901F-40-00D_Single_Vertical
SW201, SW202, SW203: SW_SPDT_CO; SPDT_mini_toggle
U2: TL074; SOIC-14_3.9x8.7mm_P1.27mm

Connections:
+5V_REF: R203.1, RV201.3, RV202.3
-5V_REF: RV201.1, RV202.1
COARSE_TUNE_IN: RV202.2
FINE_TUNE_IN: RV201.2
GND: R202.2, RV203.1, RV204.1, RV205.1, U2.3 (+)
LIN_FM_IN: SW203.3
MOD_ENV_DOWN: SW201.3
MOD_ENV_UP: SW201.1
MOD_OSC: RV203.3
unnamed: C201.1, R204.2, R205.2, R206.1, U2.2 (-)
unnamed: C201.2, C202.1, R206.2, U2.1
unnamed: RV203.2, SW203.2
unnamed: RV204.3, SW201.2
unnamed: RV205.3, SW202.2
OUT: C202.2
PWM_CV_IN: R201.2, R202.1, R203.2
PWM_IN: R201.1
SWITCHED_OUT: R204.1, R205.1
S_AND_H: SW202.1
S_AND_H_MIXER: SW202.3
V_PER_OCT_IN_3: RV204.2
V_PER_OCT_IN_4: RV205.2
V_PER_OCT_IN_5: SW203.1

Notes on the sheet:
[0, +2.5v]
Mod osc switch 1) Expo FM 2) Off 3) Linear FM
restrict PWM signal to just inside [0, +2.5]
Mod env switch 1) Up 2) Off 3) Down
[0, +5v]
[-1.25, +1.25v] in
S&H switch 1) S&H 2) Off 3) S&H mixer
[-5v, +5v] out
