JordanAceto/josh_Ox_ribbon_synth/circuit_boards/main_VCO_board/kicad_7/main_VCO_board.kicad_sch

## KiCad design circuit_boards/main_VCO_board/kicad_7/main_VCO_board.kicad_sch (2023-03-27)

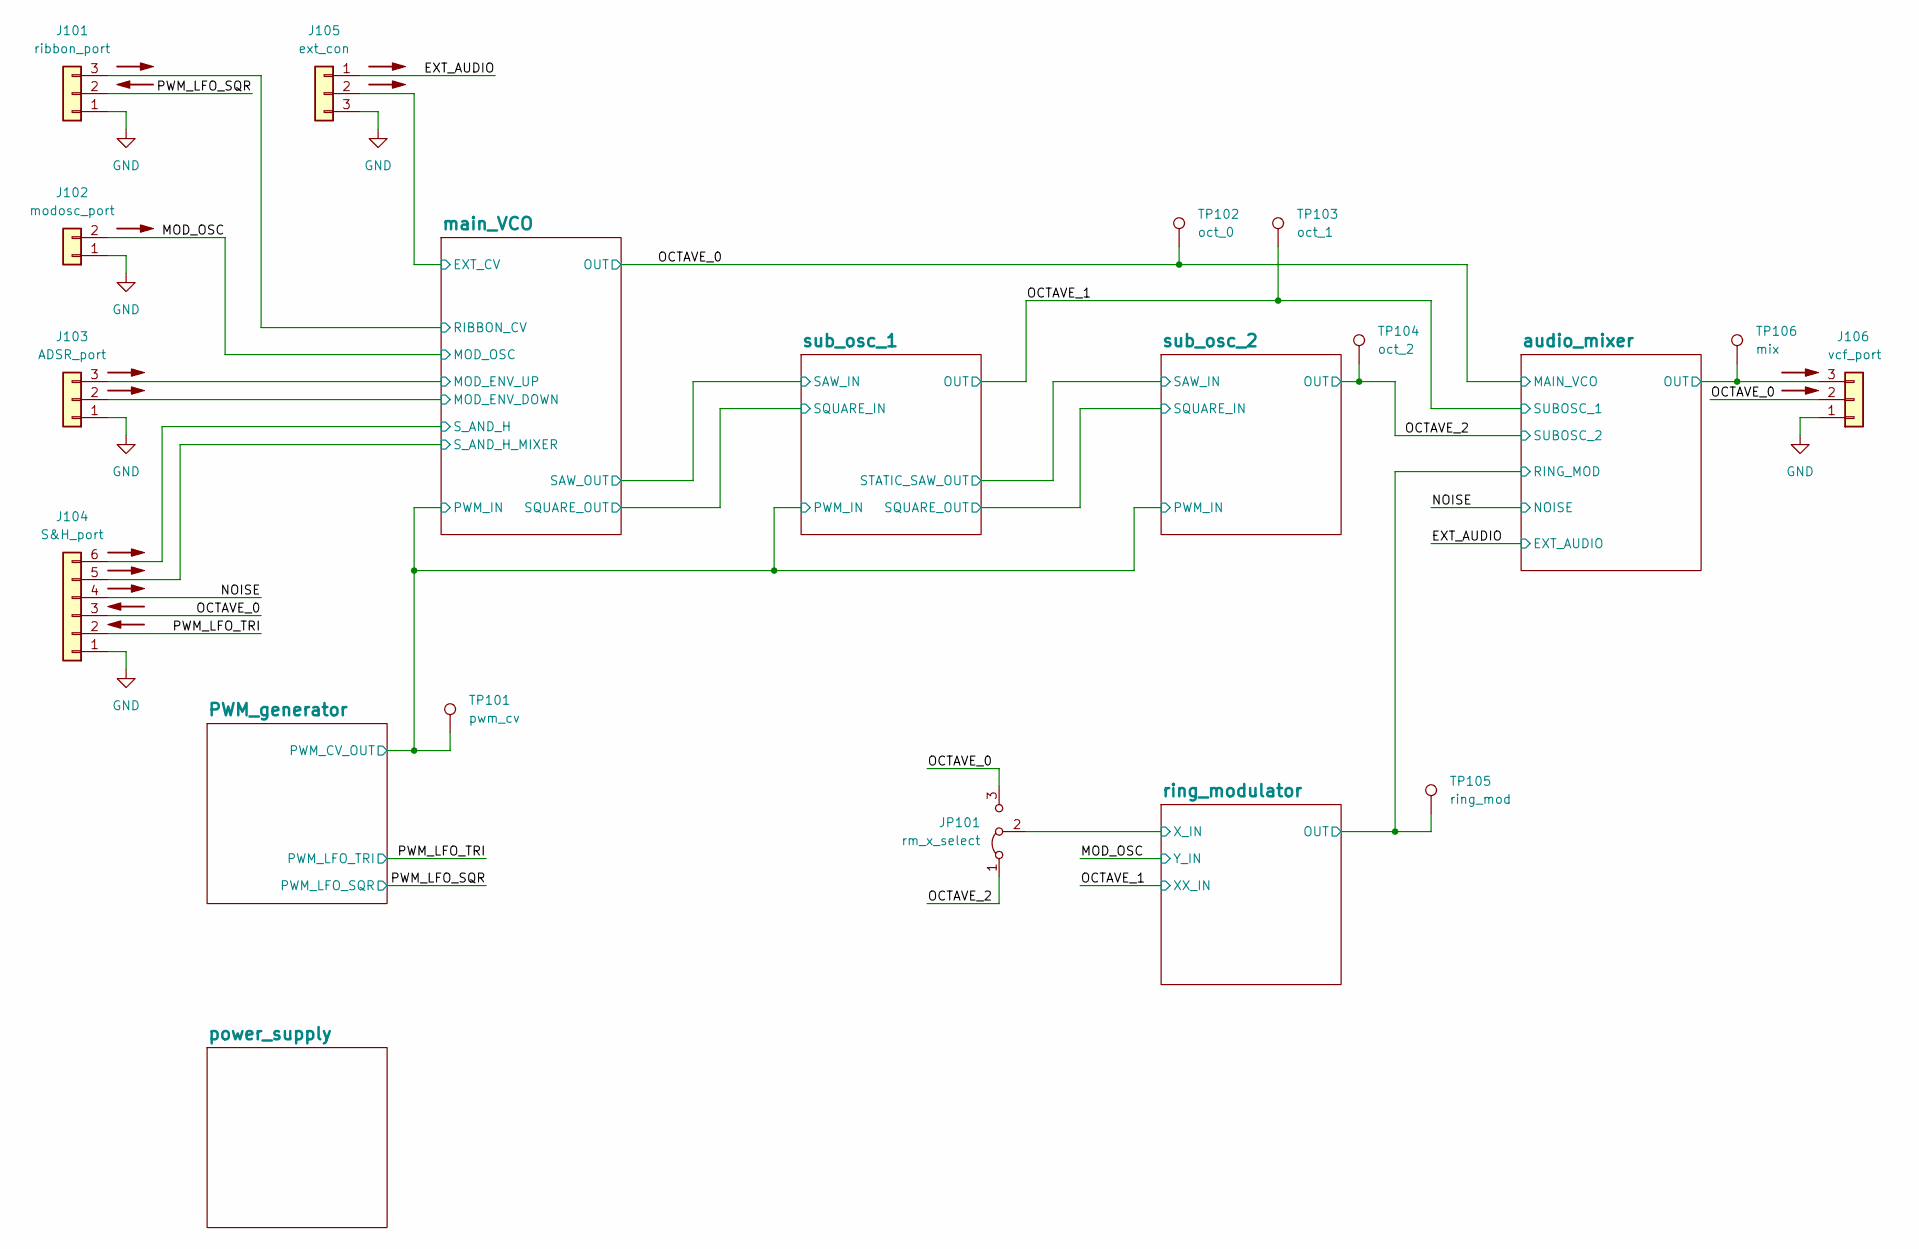
[picture p122: schematic main_VCO_board.kicad_sch]

Parts:
J101: ribbon_port; Molex_KK-254_AE-6410-03A_1x03_P2.54mm_Vertical
J102: modosc_port; Molex_KK-254_AE-6410-02A_1x02_P2.54mm_Vertical
J103: ADSR_port; Molex_KK-254_AE-6410-03A_1x03_P2.54mm_Vertical
J104: S&H_port; Molex_KK-254_AE-6410-06A_1x06_P2.54mm_Vertical
J105: ext_con; Molex_KK-254_AE-6410-03A_1x03_P2.54mm_Vertical
J106: vcf_port; Molex_KK-254_AE-6410-03A_1x03_P2.54mm_Vertical
JP101: rm_x_select; PinHeader_1x03_P2.54mm_Vertical
TP101: pwm_cv; TestPoint_Keystone_5000-5004_Miniature
TP102: oct_0; TestPoint_Keystone_5000-5004_Miniature
TP103: oct_1; TestPoint_Keystone_5000-5004_Miniature
TP104: oct_2; TestPoint_Keystone_5000-5004_Miniature
TP105: ring_mod; TestPoint_Keystone_5000-5004_Miniature
TP106: mix; TestPoint_Keystone_5000-5004_Miniature

Connections:
EXT_AUDIO: J105.1
EXT_CV: J105.2
GND: J101.1, J102.1, J103.1, J104.1, J105.3, J106.1
MOD_ENV_DOWN: J103.2
MOD_ENV_UP: J103.3
MOD_OSC: J102.2
NOISE: J104.4
OCTAVE_0: J104.3, J106.2, JP101.3 (B), TP102.1
OCTAVE_1: TP103.1
OCTAVE_2: JP101.1 (A), TP104.1
OUT: J106.3, TP105.1, TP106.1
PWM_IN: TP101.1
PWM_LFO_SQR: J101.2
PWM_LFO_TRI: J104.2
RIBBON_CV: J101.3
S_AND_H: J104.6
S_AND_H_MIXER: J104.5
X_IN: JP101.2 (C)
