JordanAceto/josh_Ox_ribbon_synth/circuit_boards/main_VCO_board/kicad_7/octave_divider.kicad_sch

## KiCad design circuit_boards/main_VCO_board/kicad_7/octave_divider.kicad_sch (2023-03-27)

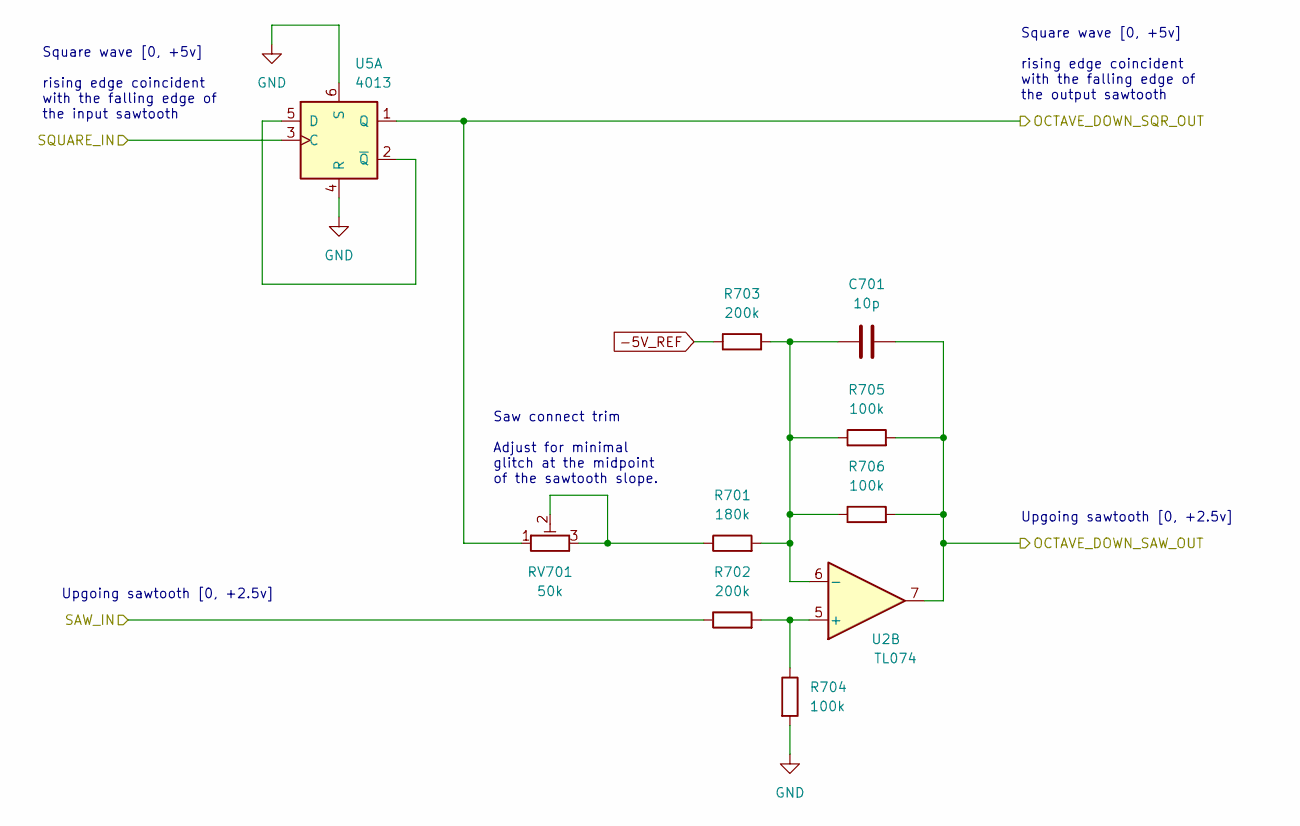
[picture p123: schematic octave_divider.kicad_sch]

Parts:
C701: 10p; C_0805_2012Metric
R701: 180k; R_0805_2012Metric
R702, R703: 200k; R_0805_2012Metric
R704, R705, R706: 100k; R_0805_2012Metric
RV701: 50k; Potentiometer_Bourns_3296W_Vertical
U2: TL074; SOIC-14_3.9x8.7mm_P1.27mm
U5: 4013; SOIC-14_3.9x8.7mm_P1.27mm

Connections:
-5V_REF: R703.1
GND: R704.2, U5.4 (R), U5.6 (S)
unnamed: C701.1, R701.2, R703.2, R705.1, R706.1, U2.6 (-)
unnamed: R701.1, RV701.2, RV701.3
unnamed: R702.2, R704.1, U2.5 (+)
unnamed: U5.2 (~Q), U5.5 (D)
OCTAVE_DOWN_SAW_OUT: C701.2, R705.2, R706.2, U2.7
OCTAVE_DOWN_SQR_OUT: RV701.1, U5.1 (Q)
SAW_IN: R702.1
SQUARE_IN: U5.3 (C)

Notes on the sheet:
Square wave [0, +5v] rising edge coincident with the falling edge of the output sawtooth
Square wave [0, +5v] rising edge coincident with the falling edge of the input sawtooth
Saw connect trim Adjust for minimal glitch at the midpoint of the sawtooth slope.
Upgoing sawtooth [0, +2.5v]
