JordanAceto/josh_Ox_ribbon_synth/circuit_boards/main_VCO_board/kicad_7/passthrough_switching.kicad_sch

## KiCad design circuit_boards/main_VCO_board/kicad_7/passthrough_switching.kicad_sch (2023-03-27)

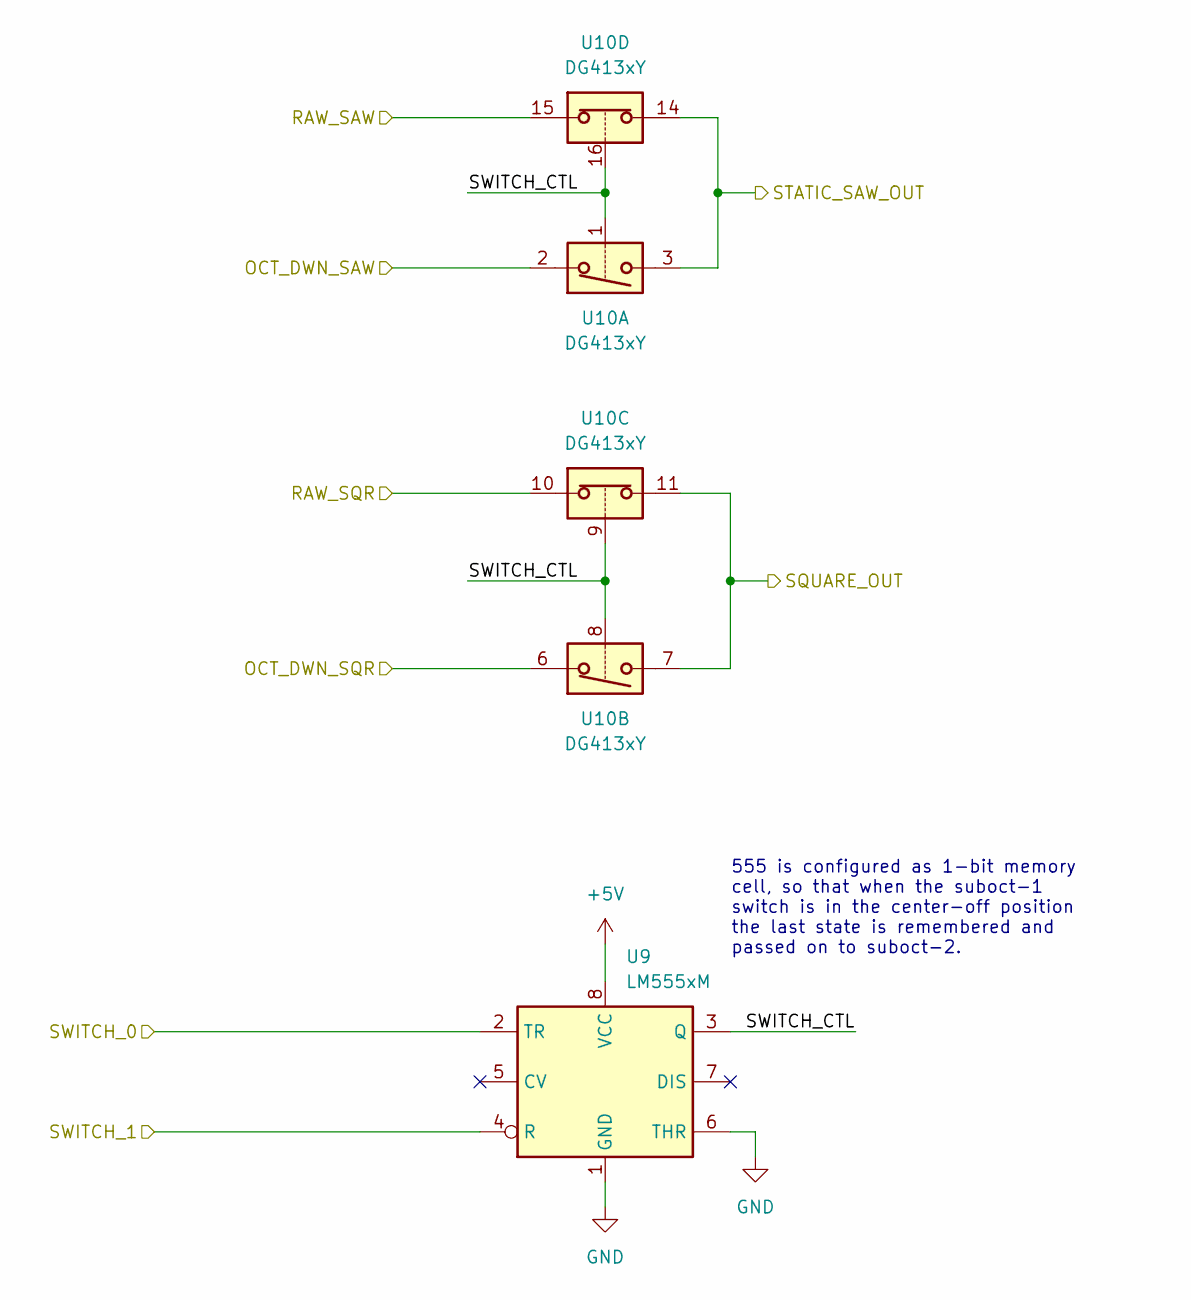
[picture p124: schematic passthrough_switching.kicad_sch]

Parts:
U9: LM555xM; SOIC-8_3.9x4.9mm_P1.27mm
U10: DG413xY; SOIC-16_3.9x9.9mm_P1.27mm

Connections:
+5V: U9.8 (VCC)
GND: U9.1 (GND), U9.6 (THR)
OCT_DWN_SAW: U10.2
OCT_DWN_SQR: U10.6
RAW_SAW: U10.15
RAW_SQR: U10.10
SQUARE_OUT: U10.7, U10.11
STATIC_SAW_OUT: U10.3, U10.14
SWITCH_0: U9.2 (TR)
SWITCH_1: U9.4 (R)
SWITCH_CTL: U9.3 (Q), U10.1, U10.8, U10.9, U10.16

Notes on the sheet:
555 is configured as 1-bit memory cell, so that when the suboct-1 switch is in the center-off position the last state is remembered and passed on to suboct-2.
