JordanAceto/josh_Ox_ribbon_synth/circuit_boards/main_VCO_board/kicad_7/power_supply.kicad_sch

## KiCad design circuit_boards/main_VCO_board/kicad_7/power_supply.kicad_sch (2023-03-27)

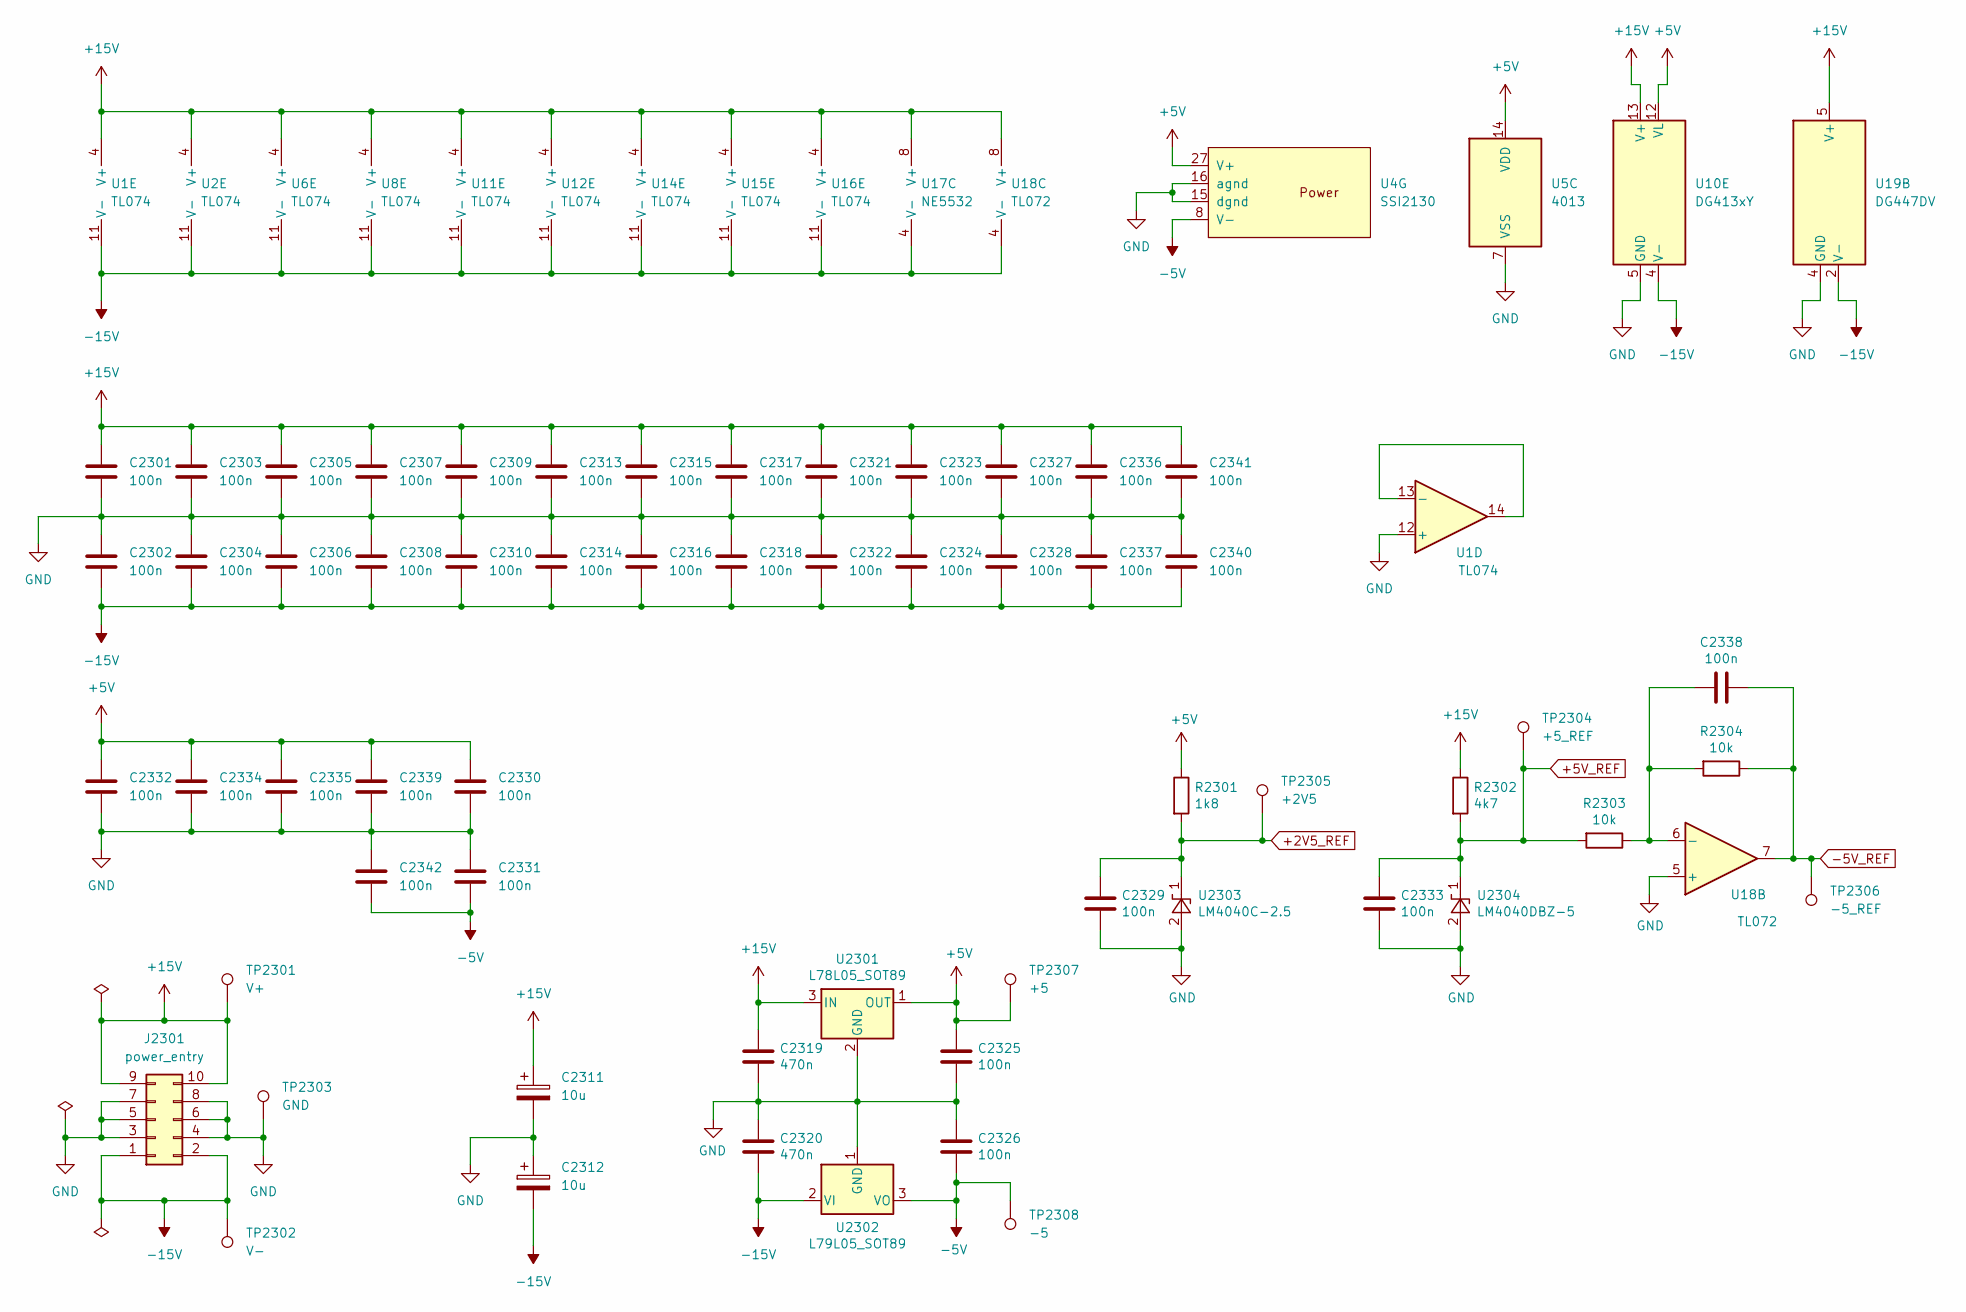
[picture p125: schematic power_supply.kicad_sch]

Parts:
C2301, C2302, C2303, C2304, C2305, C2306, C2307, C2308, C2309, C2310, C2313, C2314, C2315, C2316, C2317, C2318, C2321, C2322, C2323, C2324, C2325, C2326, C2327, C2328, C2329, C2330, C2331, C2332, C2333, C2334, C2335, C2336, C2337, C2338, C2339, C2340, C2341, C2342: 100n; C_0805_2012Metric
C2311, C2312: 10u; CP_Radial_D6.3mm_P2.50mm
C2319, C2320: 470n; C_0805_2012Metric
J2301: power_entry; IDC-Header_2x05_P2.54mm_Vertical
R2301: 1k8; R_0805_2012Metric
R2302: 4k7; R_0805_2012Metric
R2303, R2304: 10k; R_0805_2012Metric
TP2301: V+; TestPoint_Keystone_5000-5004_Miniature
TP2302: V-; TestPoint_Keystone_5000-5004_Miniature
TP2303: GND; TestPoint_Bridge_Pitch7.62mm_Drill1.3mm
TP2304: +5_REF; TestPoint_Keystone_5000-5004_Miniature
TP2305: +2V5; TestPoint_Keystone_5000-5004_Miniature
TP2306: -5_REF; TestPoint_Keystone_5000-5004_Miniature
TP2307: +5; TestPoint_Keystone_5000-5004_Miniature
TP2308: -5; TestPoint_Keystone_5000-5004_Miniature
U1, U2, U6, U8, U11, U12, U14, U15, U16: TL074; SOIC-14_3.9x8.7mm_P1.27mm
U4: SSI2130; PQN32_HandSoldering
U5: 4013; SOIC-14_3.9x8.7mm_P1.27mm
U10: DG413xY; SOIC-16_3.9x9.9mm_P1.27mm
U17: NE5532; SOIC-8_3.9x4.9mm_P1.27mm
U18: TL072; SOIC-8_3.9x4.9mm_P1.27mm
U19: DG447DV; TSOP-6_1.65x3.05mm_P0.95mm
U2301: L78L05_SOT89; SOT-89-3
U2302: L79L05_SOT89; SOT-89-3
U2303: LM4040C-2.5; SOT-23
U2304: LM4040DBZ-5; SOT-23

Connections:
+2V5_REF: C2329.1, R2301.2, TP2305.1, U2303.1 (K)
+5V: C2325.1, C2330.1, C2332.1, C2334.1, C2335.1, C2339.1, R2301.1, TP2307.1, U4.27 (V+), U5.14 (VDD), U10.12 (VL), U2301.1 (OUT)
+5V_REF: C2333.1, R2302.2, R2303.2, TP2304.1, U2304.1 (K)
+15V: C2301.1, C2303.1, C2305.1, C2307.1, C2309.1, C2311.1, C2313.1, C2315.1, C2317.1, C2319.1, C2321.1, C2323.1, C2327.1, C2336.1, C2341.1, J2301.9, J2301.10, R2302.1, TP2301.1, U1.4 (V+), U2.4 (V+), U6.4 (V+), U8.4 (V+), U10.13 (V+), U11.4 (V+), U12.4 (V+), U14.4 (V+), U15.4 (V+), U16.4 (V+), U17.8 (V+), U18.8 (V+), U19.5 (V+), U2301.3 (IN)
-5V: C2326.2, C2331.2, C2342.2, TP2308.1, U4.8 (V-), U2302.3 (VO)
-5V_REF: C2338.1, R2304.1, TP2306.1, U18.7
-15V: C2302.2, C2304.2, C2306.2, C2308.2, C2310.2, C2312.2, C2314.2, C2316.2, C2318.2, C2320.2, C2322.2, C2324.2, C2328.2, C2337.2, C2340.2, J2301.1, J2301.2, TP2302.1, U1.11 (V-), U2.11 (V-), U6.11 (V-), U8.11 (V-), U10.4 (V-), U11.11 (V-), U12.11 (V-), U14.11 (V-), U15.11 (V-), U16.11 (V-), U17.4 (V-), U18.4 (V-), U19.2 (V-), U2302.2 (VI)
GND: C2301.2, C2302.1, C2303.2, C2304.1, C2305.2, C2306.1, C2307.2, C2308.1, C2309.2, C2310.1, C2311.2, C2312.1, C2313.2, C2314.1, C2315.2, C2316.1, C2317.2, C2318.1, C2319.2, C2320.1, C2321.2, C2322.1, C2323.2, C2324.1, C2325.2, C2326.1, C2327.2, C2328.1, C2329.2, C2330.2, C2331.1, C2332.2, C2333.2, C2334.2, C2335.2, C2336.2, C2337.1, C2339.2, C2340.1, C2341.2, C2342.1, J2301.3, J2301.4, J2301.5, J2301.6, J2301.7, J2301.8, TP2303.1, U1.12 (+), U4.15 (dgnd), U4.16 (agnd), U5.7 (VSS), U10.5 (GND), U18.5 (+), U19.4 (GND), U2301.2 (GND), U2302.1 (GND), U2303.2 (A), U2304.2 (A)
unnamed: C2338.2, R2303.1, R2304.2, U18.6 (-)
unnamed: U1.13 (-), U1.14
