JordanAceto/josh_Ox_ribbon_synth/circuit_boards/main_VCO_board/kicad_7/ring_modulator.kicad_sch

## KiCad design circuit_boards/main_VCO_board/kicad_7/ring_modulator.kicad_sch (2023-03-27)

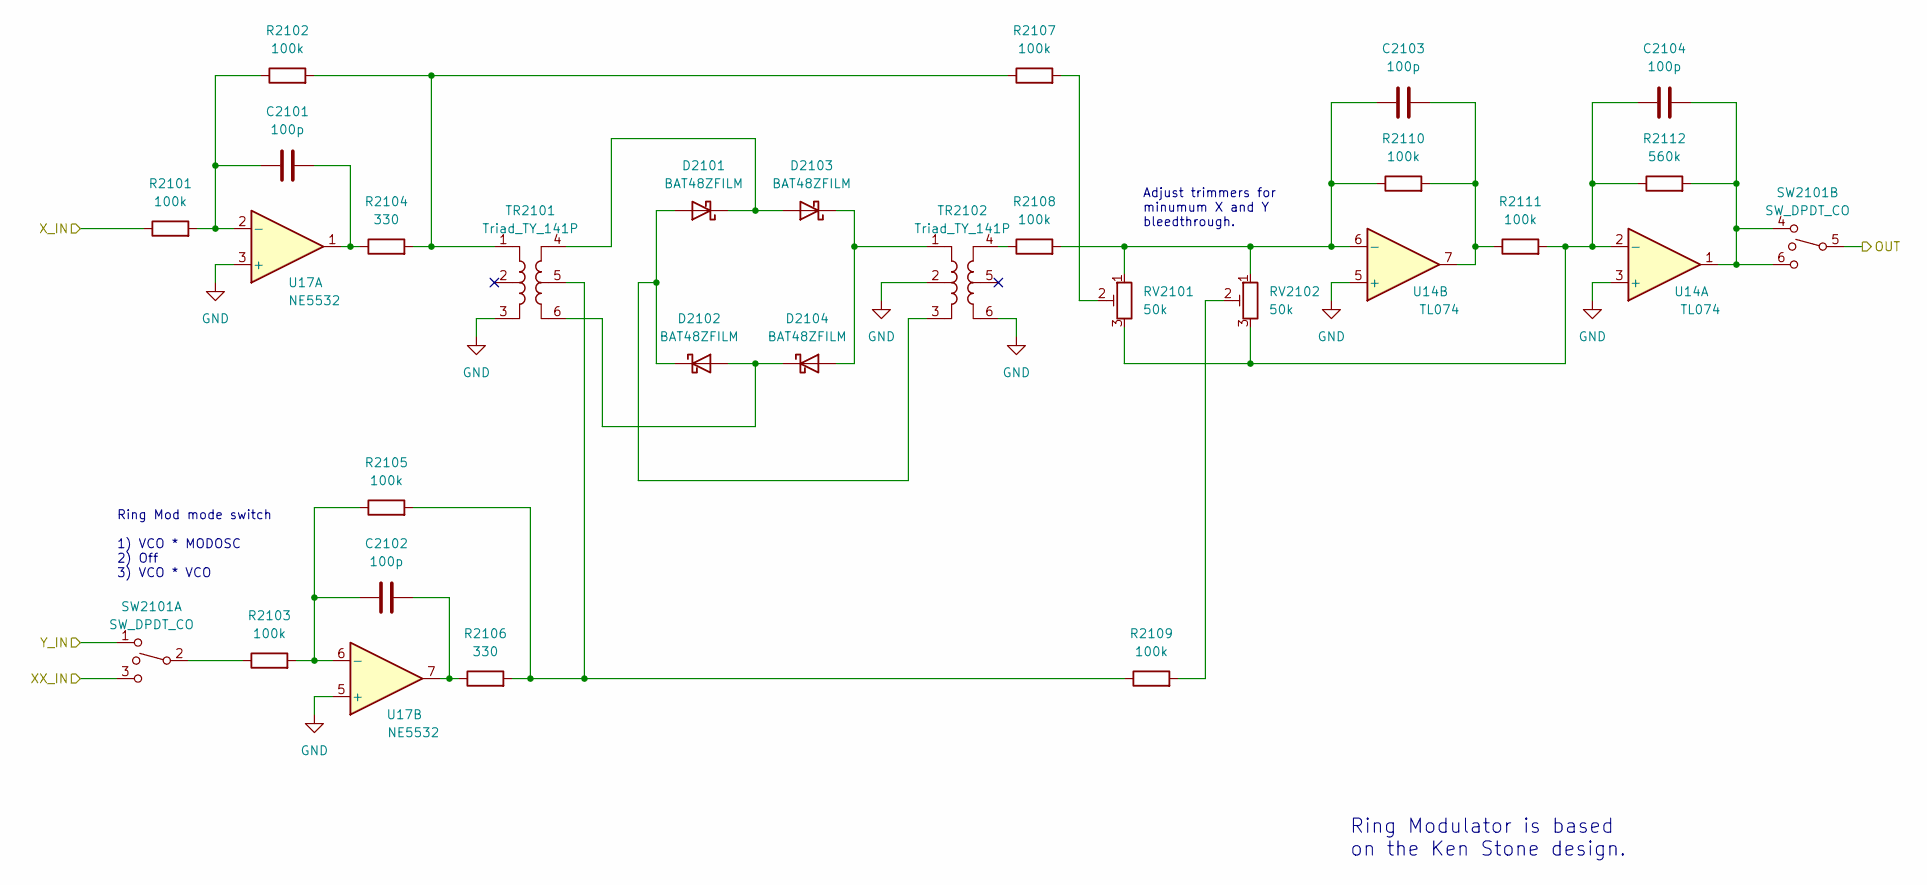
[picture p126: schematic ring_modulator.kicad_sch]

Parts:
C2101, C2102, C2103, C2104: 100p; C_0805_2012Metric
D2101, D2102, D2103, D2104: BAT48ZFILM; D_SOD-123
R2101, R2102, R2103, R2105, R2107, R2108, R2109, R2110, R2111: 100k; R_0805_2012Metric
R2104, R2106: 330; R_0805_2012Metric
R2112: 560k; R_0805_2012Metric
RV2101, RV2102: 50k; Potentiometer_Bourns_3296W_Vertical
SW2101: SW_DPDT_CO; DPDT_mini_toggle
TR2101, TR2102: Triad_TY_141P; Triad_TY-141P
U14: TL074; SOIC-14_3.9x8.7mm_P1.27mm
U17: NE5532; SOIC-8_3.9x4.9mm_P1.27mm

Connections:
GND: TR2101.3, TR2102.2, TR2102.6, U14.3 (+), U14.5 (+), U17.3 (+), U17.5 (+)
unnamed: C2101.1, R2101.2, R2102.1, U17.2 (-)
unnamed: C2101.2, R2104.1, U17.1
unnamed: C2102.1, R2103.2, R2105.1, U17.6 (-)
unnamed: C2102.2, R2106.1, U17.7
unnamed: C2103.1, R2108.2, R2110.1, RV2101.1, RV2102.1, U14.6 (-)
unnamed: C2103.2, R2110.2, R2111.1, U14.7
unnamed: C2104.1, R2111.2, R2112.1, RV2101.3, RV2102.3, U14.2 (-)
unnamed: C2104.2, R2112.2, SW2101.4, SW2101.6, U14.1
unnamed: D2101.1 (K), D2103.2 (A), TR2101.4
unnamed: D2101.2 (A), D2102.1 (K), TR2102.3
unnamed: D2102.2 (A), D2104.1 (K), TR2101.6
unnamed: D2103.1 (K), D2104.2 (A), TR2102.1
unnamed: R2102.2, R2104.2, R2107.1, TR2101.1
unnamed: R2103.1, SW2101.2
unnamed: R2105.2, R2106.2, R2109.1, TR2101.5
unnamed: R2107.2, RV2101.2
unnamed: R2108.1, TR2102.4
unnamed: R2109.2, RV2102.2
OUT: SW2101.5
XX_IN: SW2101.3
X_IN: R2101.1
Y_IN: SW2101.1

Notes on the sheet:
Ring Mod mode switch 1) VCO * MODOSC 2) Off 3) VCO * VCO
Ring Modulator is based on the Ken Stone design.
Adjust trimmers for minumum X and Y bleedthrough.
