JordanAceto/josh_Ox_ribbon_synth/circuit_boards/main_VCO_board/kicad_7/saw_animator.kicad_sch

## KiCad design circuit_boards/main_VCO_board/kicad_7/saw_animator.kicad_sch (2023-03-27)

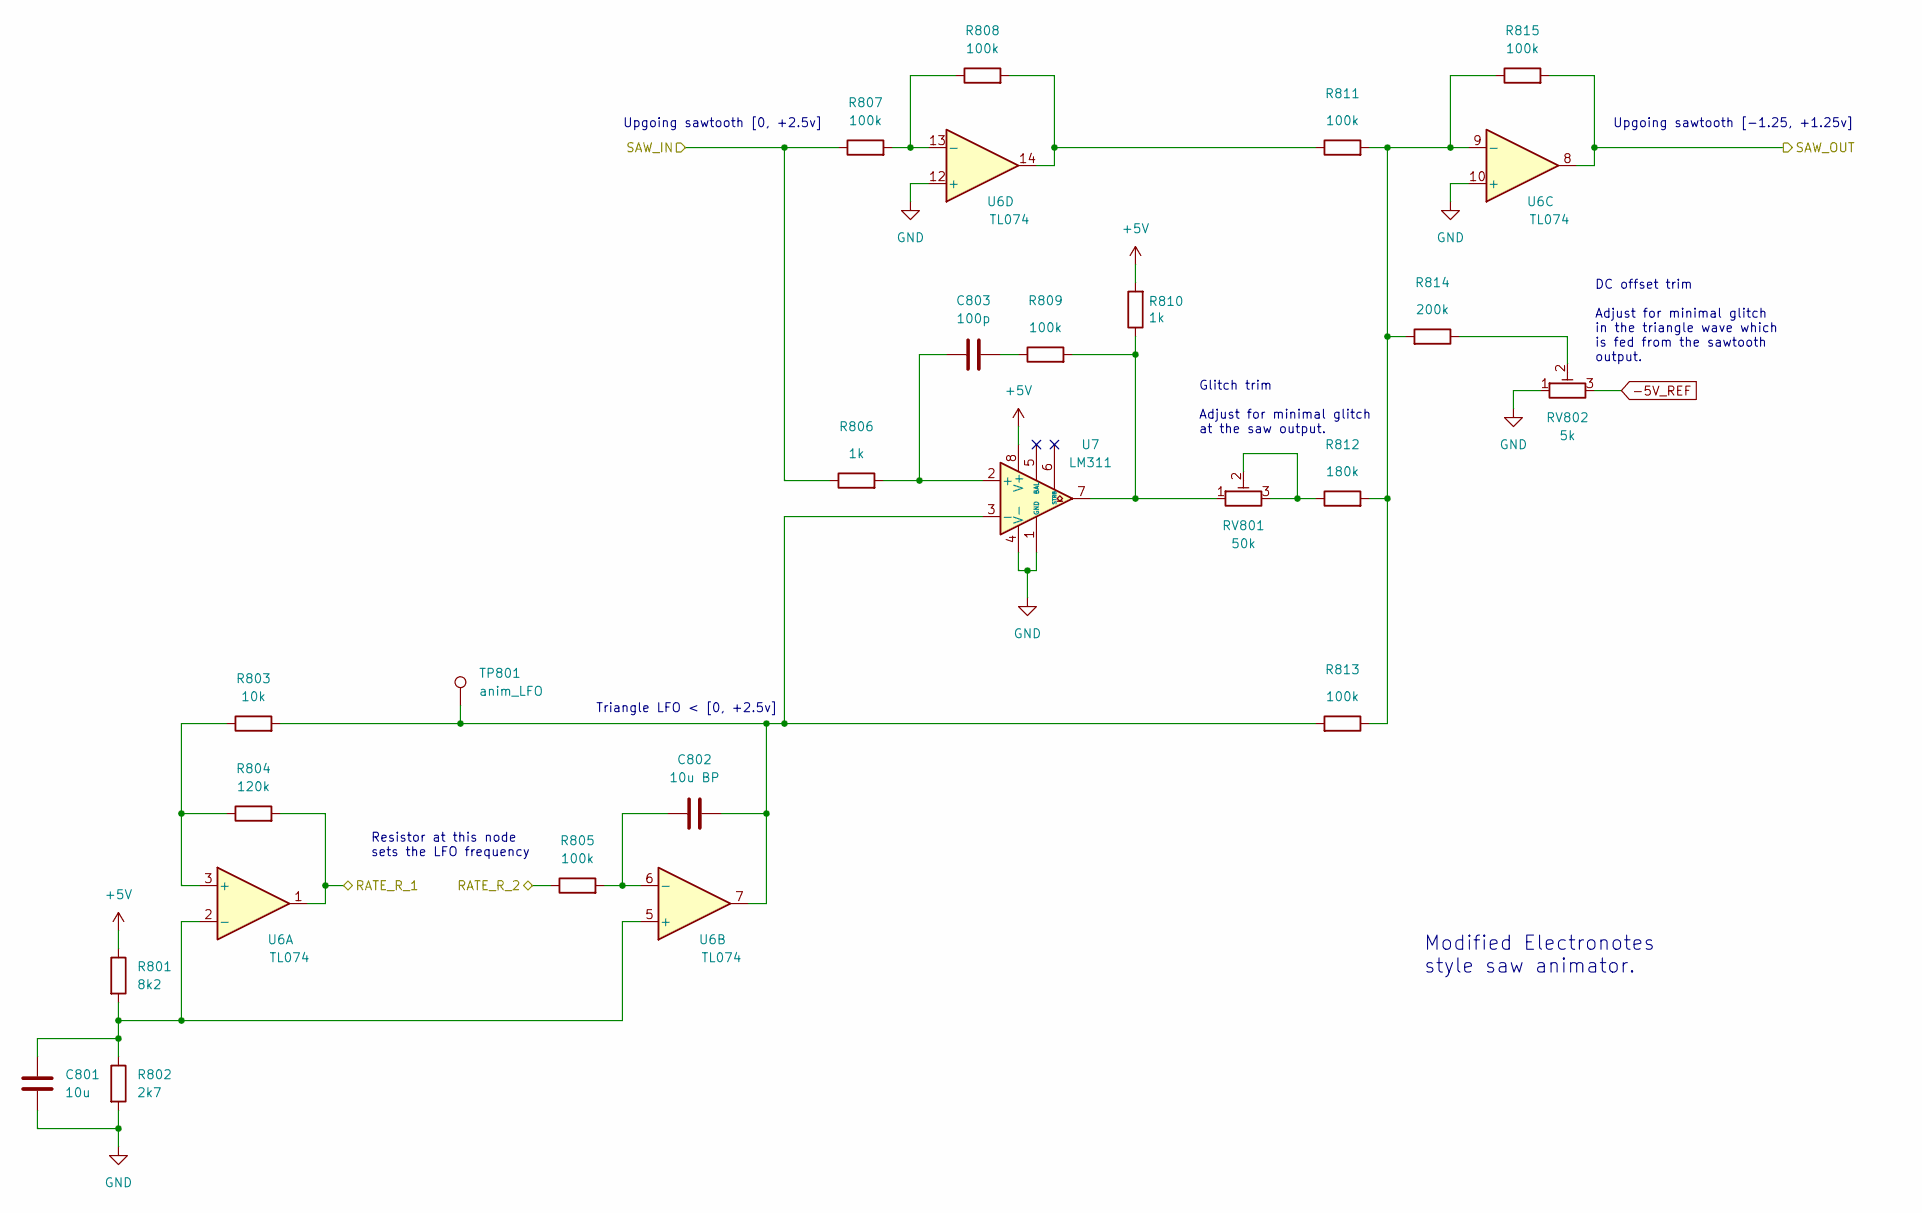
[picture p127: schematic saw_animator.kicad_sch]

Parts:
C801: 10u; C_0805_2012Metric
C802: 10u BP; C_Radial_D6.3mm_H5.0mm_P2.50mm
C803: 100p; C_0805_2012Metric
R801: 8k2; R_0805_2012Metric
R802: 2k7; R_0805_2012Metric
R803: 10k; R_0805_2012Metric
R804: 120k; R_0805_2012Metric
R805, R807, R808, R809, R811, R813, R815: 100k; R_0805_2012Metric
R806, R810: 1k; R_0805_2012Metric
R812: 180k; R_0805_2012Metric
R814: 200k; R_0805_2012Metric
RV801: 50k; Potentiometer_Bourns_3296W_Vertical
RV802: 5k; Potentiometer_Bourns_3296W_Vertical
TP801: anim_LFO; TestPoint_Keystone_5000-5004_Miniature
U6: TL074; SOIC-14_3.9x8.7mm_P1.27mm
U7: LM311; SOIC-8_3.9x4.9mm_P1.27mm

Connections:
+5V: R801.1, R810.2, U7.8 (V+)
-5V_REF: RV802.3
GND: C801.2, R802.2, RV802.1, U6.10 (+), U6.12 (+), U7.1 (GND), U7.4 (V-)
unnamed: C801.1, R801.2, R802.1, U6.2 (-), U6.5 (+)
unnamed: C802.1, R805.2, U6.6 (-)
unnamed: C802.2, R803.2, R813.2, TP801.1, U6.7, U7.3 (-)
unnamed: C803.1, R806.2, U7.2 (+)
unnamed: C803.2, R809.1
unnamed: R803.1, R804.1, U6.3 (+)
unnamed: R807.2, R808.1, U6.13 (-)
unnamed: R808.2, R811.1, U6.14
unnamed: R809.2, R810.1, RV801.1, U7.7
unnamed: R811.2, R812.2, R813.1, R814.2, R815.1, U6.9 (-)
unnamed: R812.1, RV801.2, RV801.3
unnamed: R814.1, RV802.2
RATE_R_1: R804.2, U6.1
RATE_R_2: R805.1
SAW_IN: R806.1, R807.1
SAW_OUT: R815.2, U6.8

Notes on the sheet:
DC offset trim Adjust for minimal glitch in the triangle wave which is fed from the sawtooth output.
Modified Electronotes style saw animator.
Resistor at this node sets the LFO frequency
Triangle LFO < [0, +2.5v]
Upgoing sawtooth [-1.25, +1.25v]
Glitch trim Adjust for minimal glitch at the saw output.
Upgoing sawtooth [0, +2.5v]
