JordanAceto/josh_Ox_ribbon_synth/circuit_boards/main_VCO_board/kicad_7/saw_to_tri_shaper.kicad_sch

## KiCad design circuit_boards/main_VCO_board/kicad_7/saw_to_tri_shaper.kicad_sch (2023-03-27)

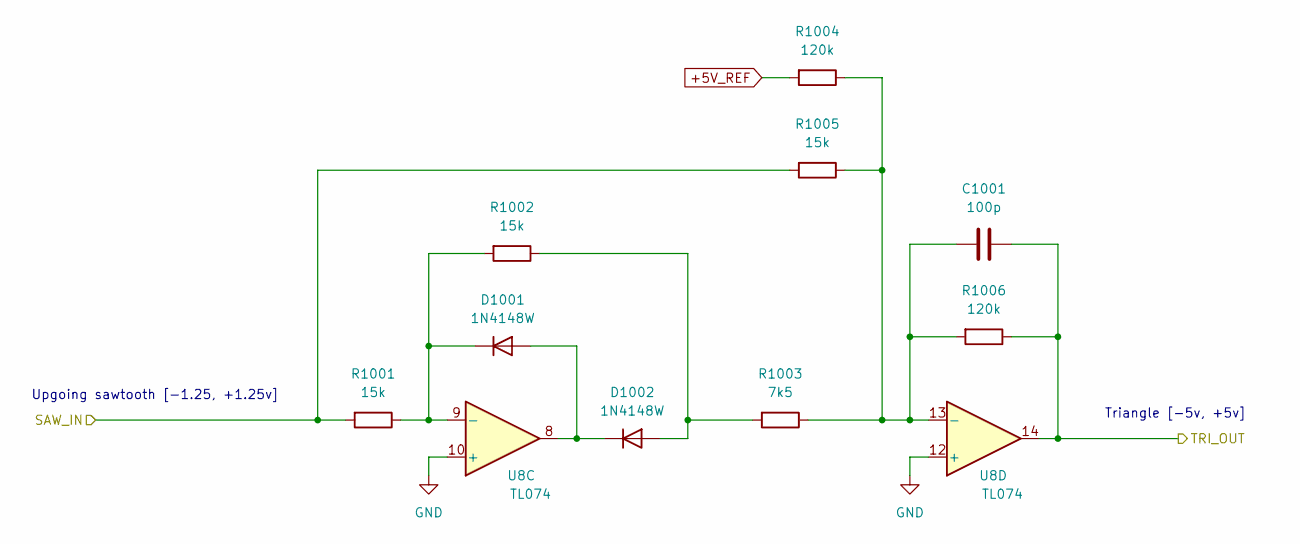
[picture p128: schematic saw_to_tri_shaper.kicad_sch]

Parts:
C1001: 100p; C_0805_2012Metric
D1001, D1002: 1N4148W; D_SOD-123
R1001, R1002, R1005: 15k; R_0805_2012Metric
R1003: 7k5; R_0805_2012Metric
R1004, R1006: 120k; R_0805_2012Metric
U8: TL074; SOIC-14_3.9x8.7mm_P1.27mm

Connections:
+5V_REF: R1004.2
GND: U8.10 (+), U8.12 (+)
unnamed: C1001.1, R1003.1, R1004.1, R1005.1, R1006.2, U8.13 (-)
unnamed: D1001.1 (K), R1001.1, R1002.2, U8.9 (-)
unnamed: D1001.2 (A), D1002.1 (K), U8.8
unnamed: D1002.2 (A), R1002.1, R1003.2
SAW_IN: R1001.2, R1005.2
TRI_OUT: C1001.2, R1006.1, U8.14

Notes on the sheet:
Triangle [-5v, +5v]
Upgoing sawtooth [-1.25, +1.25v]
