JordanAceto/josh_Ox_ribbon_synth/circuit_boards/main_VCO_board/kicad_7/sub_osc_1.kicad_sch

## KiCad design circuit_boards/main_VCO_board/kicad_7/sub_osc_1.kicad_sch (2023-03-27)

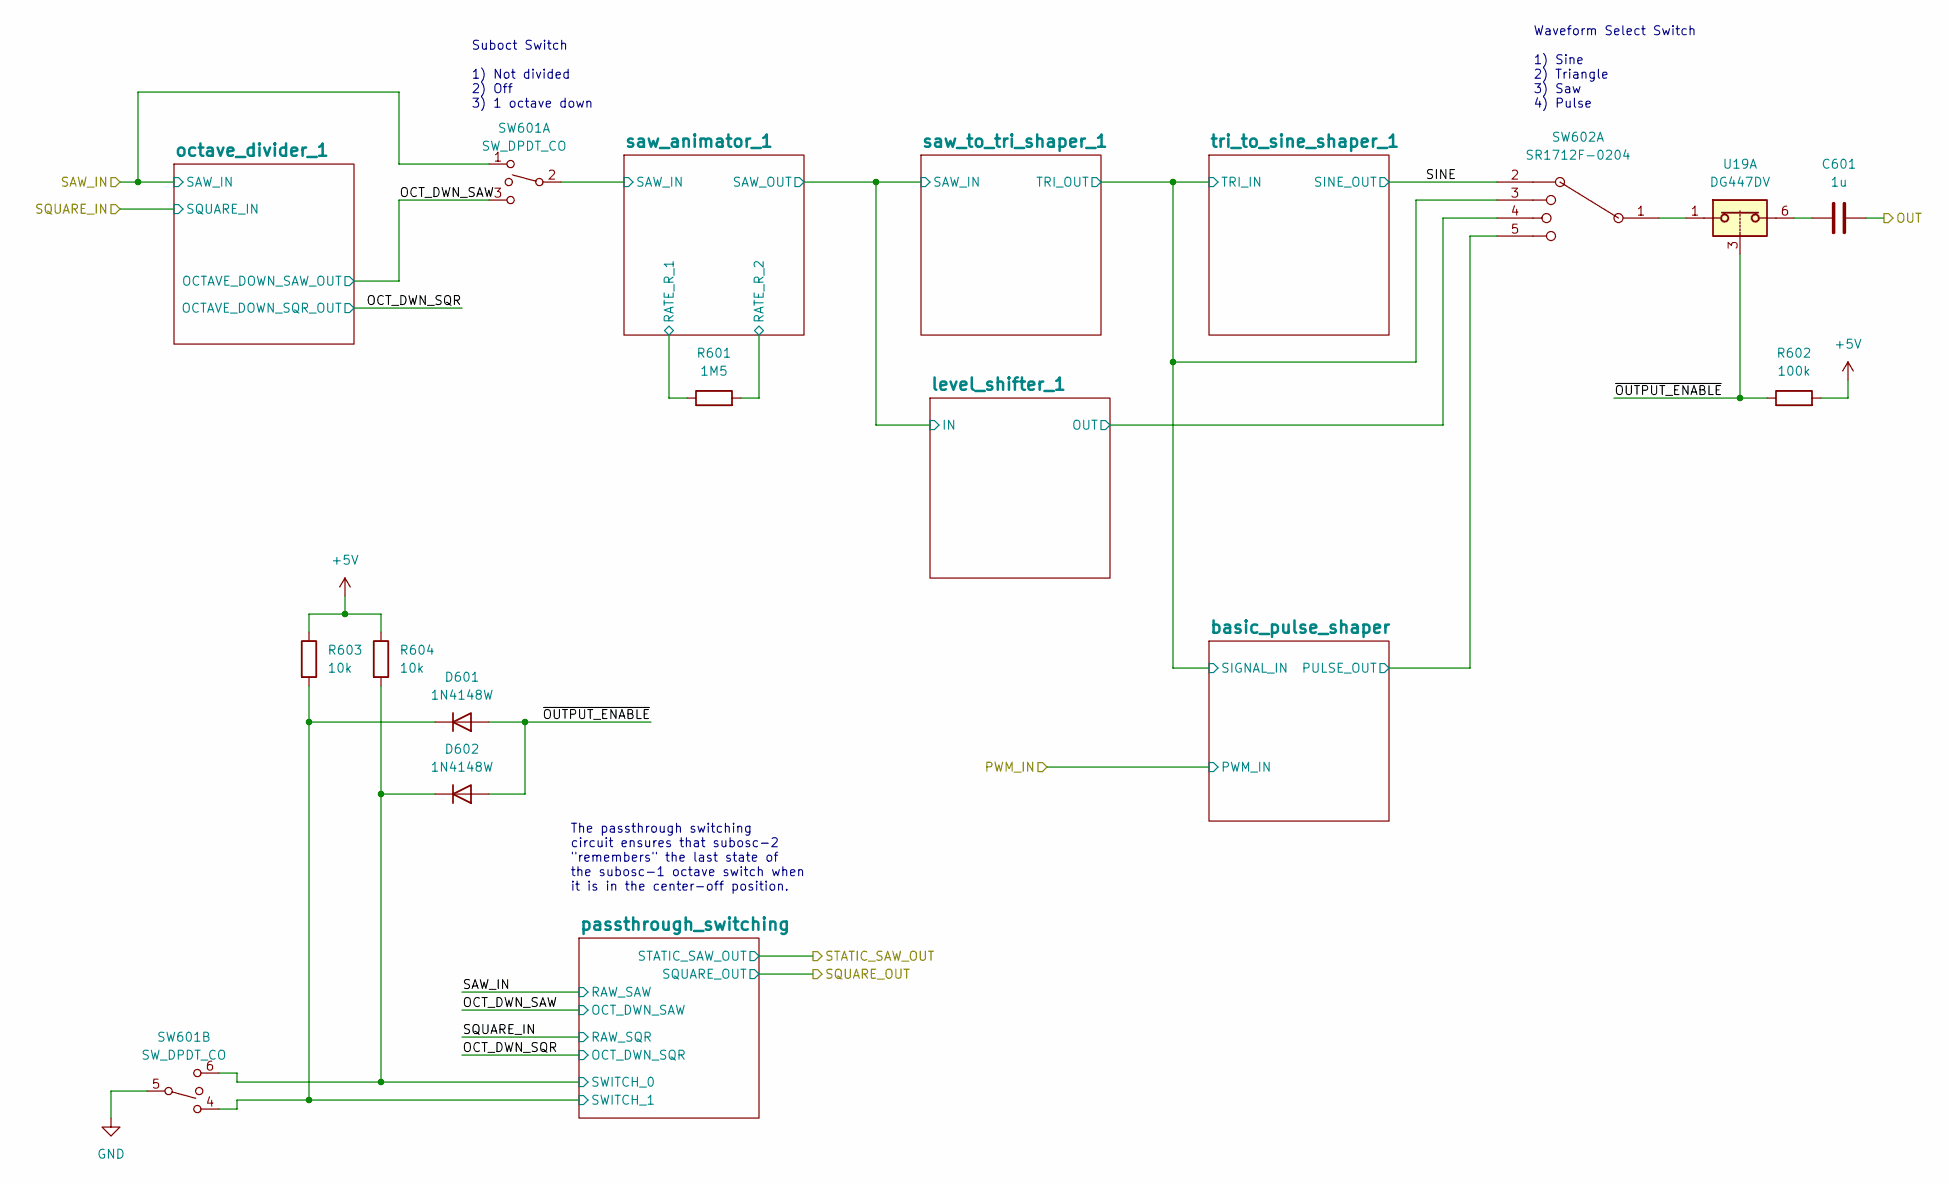
[picture p129: schematic sub_osc_1.kicad_sch]

Parts:
C601: 1u; C_Rect_L7.2mm_W5.5mm_P5.00mm_FKS2_FKP2_MKS2_MKP2
D601, D602: 1N4148W; D_SOD-123
R601: 1M5; R_0805_2012Metric
R602: 100k; R_0805_2012Metric
R603, R604: 10k; R_0805_2012Metric
SW601: SW_DPDT_CO; DPDT_mini_toggle
SW602: SR1712F-0204; SR1712F_rotary_switch
U19: DG447DV; TSOP-6_1.65x3.05mm_P0.95mm

Connections:
+5V: R602.2, R603.1, R604.1
GND: SW601.5
unnamed: C601.1, U19.6
unnamed: SW602.1, U19.1
OCT_DWN_SAW: SW601.3
OUT: C601.2, SW602.4
PULSE_OUT: SW602.5
RATE_R_1: R601.1
RATE_R_2: R601.2
SAW_IN: SW601.1, SW601.2
SINE: SW602.2
SWITCH_0: D602.1 (K), R604.2, SW601.6
SWITCH_1: D601.1 (K), R603.2, SW601.4
TRI_IN: SW602.3
~OUTPUT_ENABLE: D601.2 (A), D602.2 (A), R602.1, U19.3

Notes on the sheet:
Waveform Select Switch 1) Sine 2) Triangle 3) Saw 4) Pulse
Suboct Switch 1) Not divided 2) Off 3) 1 octave down
The passthrough switching circuit ensures that subosc-2 "remembers" the last state of the subosc-1 octave switch when it is in the center-off position.
