JordanAceto/josh_Ox_ribbon_synth/circuit_boards/main_VCO_board/kicad_7/sub_osc_2.kicad_sch

## KiCad design circuit_boards/main_VCO_board/kicad_7/sub_osc_2.kicad_sch (2023-03-27)

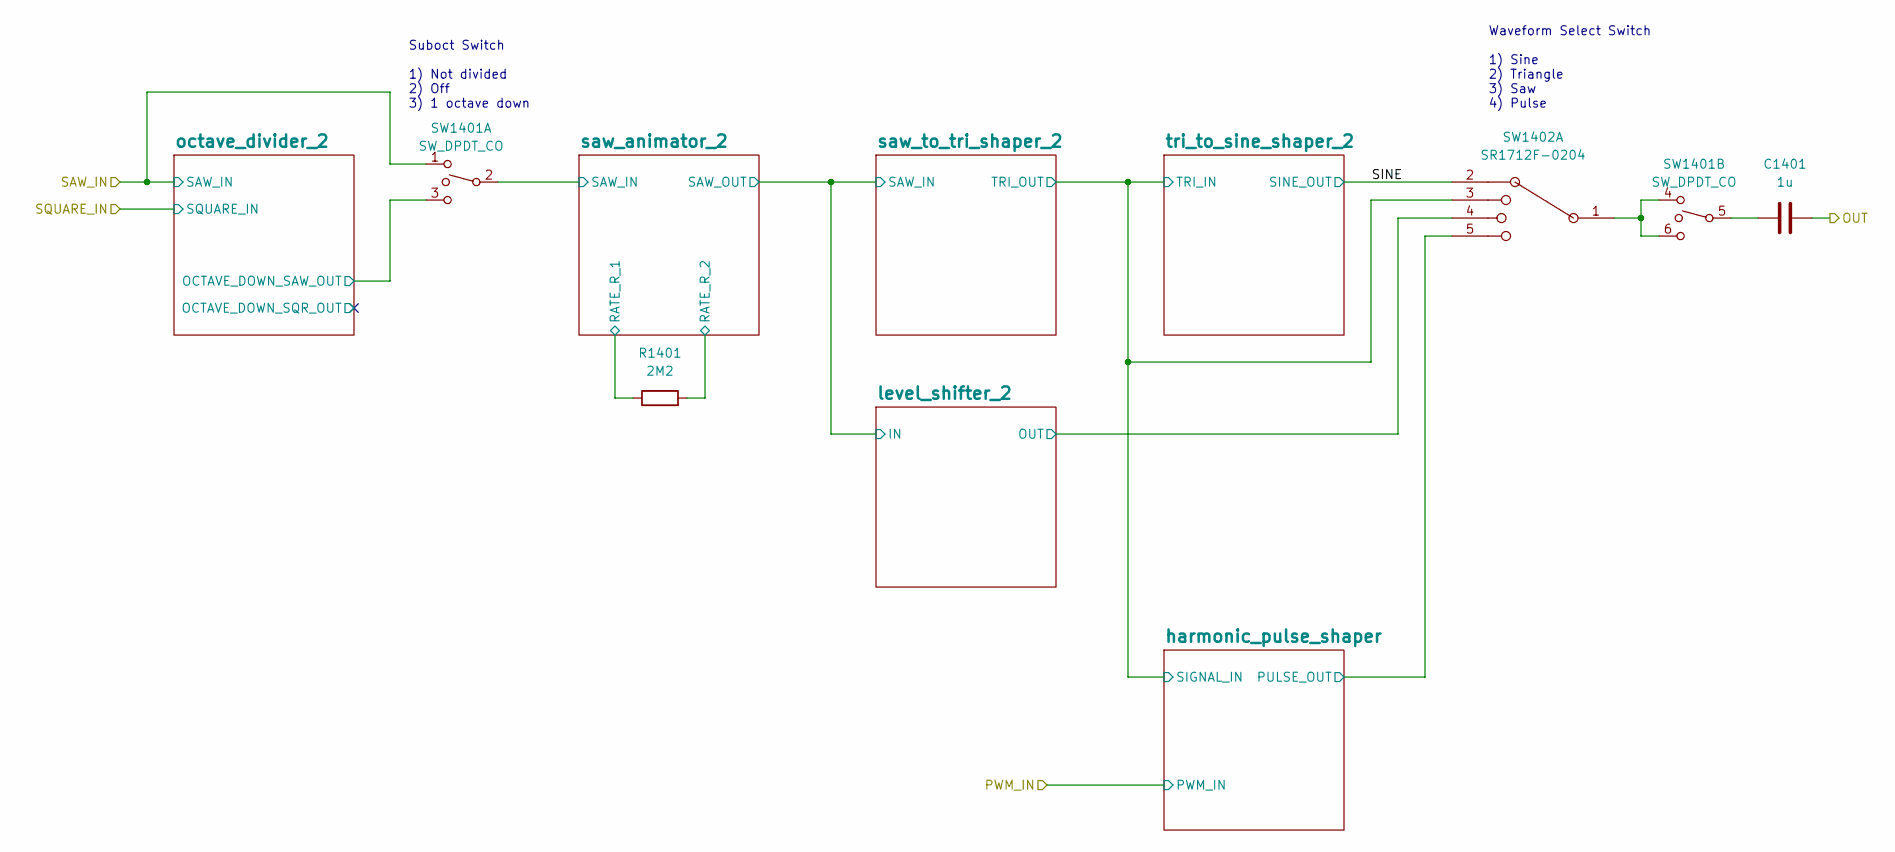
[picture p130: schematic sub_osc_2.kicad_sch]

Parts:
C1401: 1u; C_Rect_L7.2mm_W5.5mm_P5.00mm_FKS2_FKP2_MKS2_MKP2
R1401: 2M2; R_0805_2012Metric
SW1401: SW_DPDT_CO; DPDT_mini_toggle
SW1402: SR1712F-0204; SR1712F_rotary_switch

Connections:
unnamed: C1401.1, SW1401.5
unnamed: SW1401.4, SW1401.6, SW1402.1
OCTAVE_DOWN_SAW_OUT: SW1401.3
OUT: C1401.2, SW1402.4
PULSE_OUT: SW1402.5
RATE_R_1: R1401.1
RATE_R_2: R1401.2
SAW_IN: SW1401.1, SW1401.2
SINE: SW1402.2
TRI_IN: SW1402.3

Notes on the sheet:
Suboct Switch 1) Not divided 2) Off 3) 1 octave down
Waveform Select Switch 1) Sine 2) Triangle 3) Saw 4) Pulse
