JordanAceto/josh_Ox_ribbon_synth/circuit_boards/main_VCO_board/kicad_7/tri_to_sine_shaper.kicad_sch

## KiCad design circuit_boards/main_VCO_board/kicad_7/tri_to_sine_shaper.kicad_sch (2023-03-27)

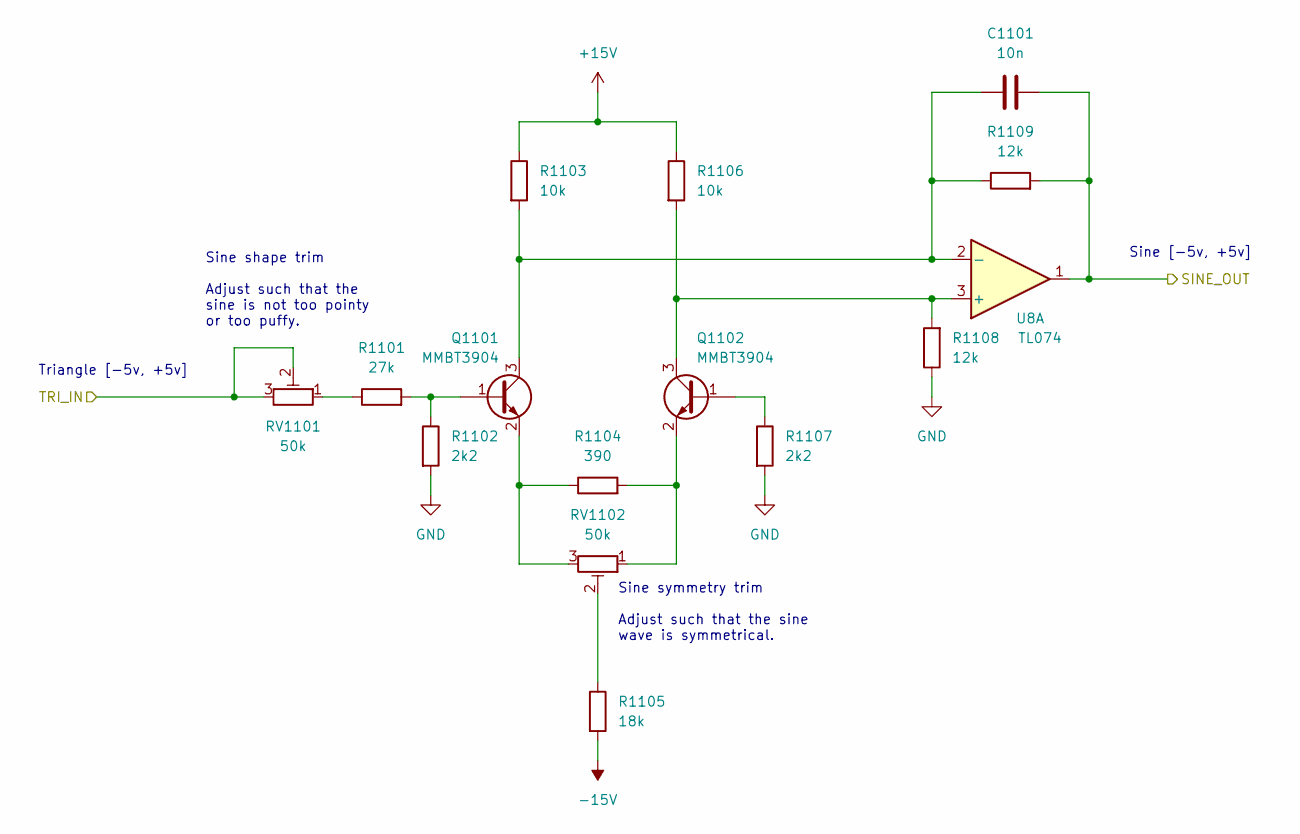
[picture p131: schematic tri_to_sine_shaper.kicad_sch]

Parts:
C1101: 10n; C_0805_2012Metric
Q1101, Q1102: MMBT3904; SOT-23
R1101: 27k; R_0805_2012Metric
R1102, R1107: 2k2; R_0805_2012Metric
R1103, R1106: 10k; R_0805_2012Metric
R1104: 390; R_0805_2012Metric
R1105: 18k; R_0805_2012Metric
R1108, R1109: 12k; R_0805_2012Metric
RV1101, RV1102: 50k; Potentiometer_Bourns_3296W_Vertical
U8: TL074; SOIC-14_3.9x8.7mm_P1.27mm

Connections:
+15V: R1103.1, R1106.1
-15V: R1105.2
GND: R1102.2, R1107.2, R1108.1
unnamed: C1101.1, Q1101.3 (C), R1103.2, R1109.1, U8.2 (-)
unnamed: Q1101.1 (B), R1101.2, R1102.1
unnamed: Q1101.2 (E), R1104.1, RV1102.3
unnamed: Q1102.1 (B), R1107.1
unnamed: Q1102.2 (E), R1104.2, RV1102.1
unnamed: Q1102.3 (C), R1106.2, R1108.2, U8.3 (+)
unnamed: R1101.1, RV1101.1
unnamed: R1105.1, RV1102.2
SINE_OUT: C1101.2, R1109.2, U8.1
TRI_IN: RV1101.2, RV1101.3

Notes on the sheet:
Sine shape trim Adjust such that the sine is not too pointy or too puffy.
Sine symmetry trim Adjust such that the sine wave is symmetrical.
Triangle [-5v, +5v]
Sine [-5v, +5v]
